dancvan/AlGaAs_electrooptic_effect/documents/internal_notes/stefan/coaximpedanceExpanded.pdf

cable | impedance
Typical | coax | cables | in | labs (

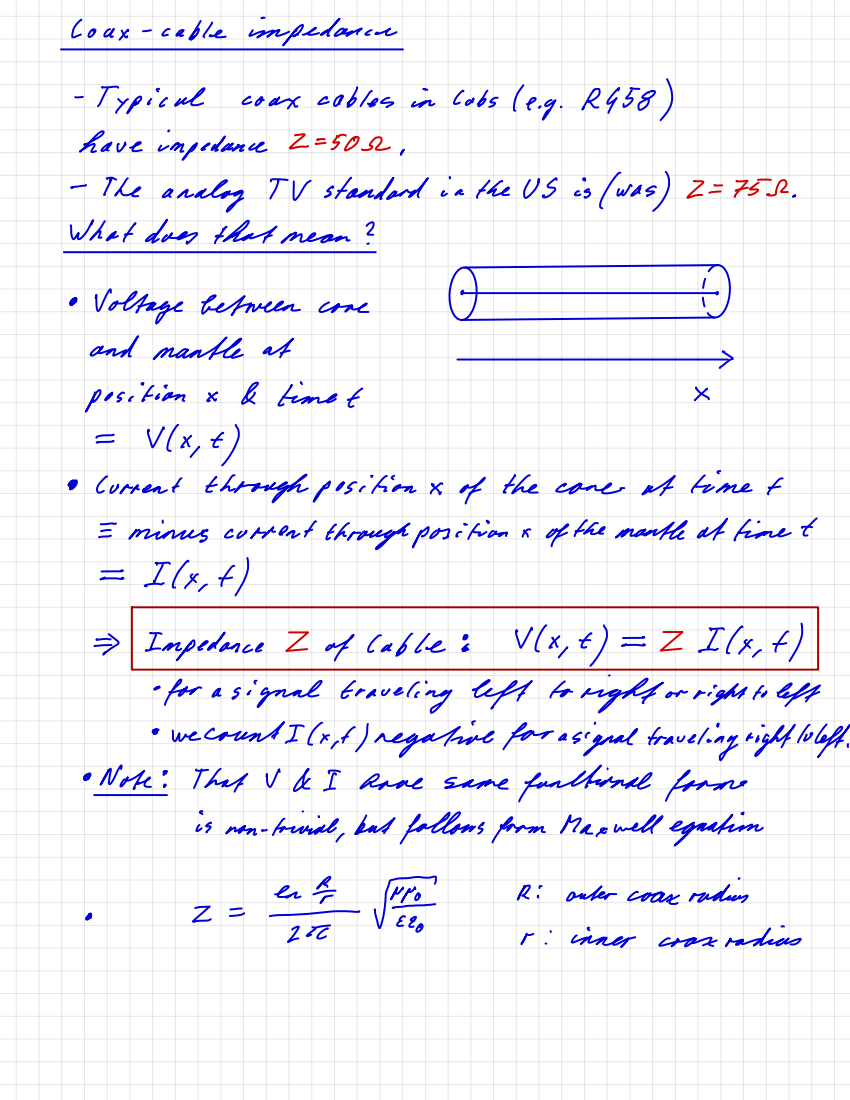
[picture p15: page 1]
Coax; have; impedance; The; analog; standard in; the; is (was); What does; thatmean; Voltage; between; cone; and; mantle; position; time t; Vlx,; Current; through position; cane; time; = minus; current throughposition; of the; mantle attime t; Itx. t; Impedance; cable; for a; signal; traveling; left; to nightor right to; • Note; That; same; functional; forme; non -; trivial,; butfollows from; Maxwell equation; JOE; outer coat radius; inner; coat; radius

• wecountI(xf)negative for a

signal traveling righttoleft.

A) | Cable | termination | & reflector | .

# Haq r

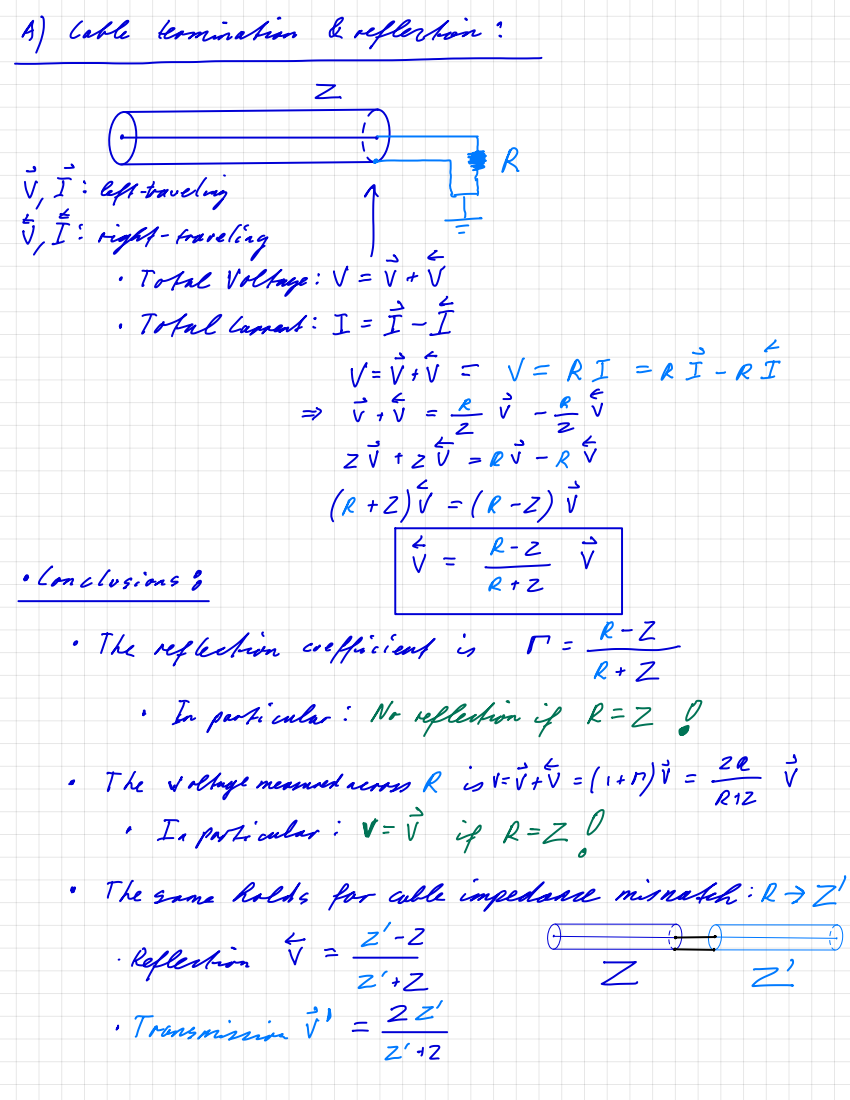
[picture p16: page 2]
I : eye.; traveling; right ⁻; Total; Voltage : V; Total Lamont :; Conclusions 8; reflection; coefficient; particular; reflection if; The; voltage measuredacross R; In particular; same; holds; for; cable; impedance; mismatch : R →; Reflection; Transmission

B) | Driving | a | coat | cable
.Ew# •

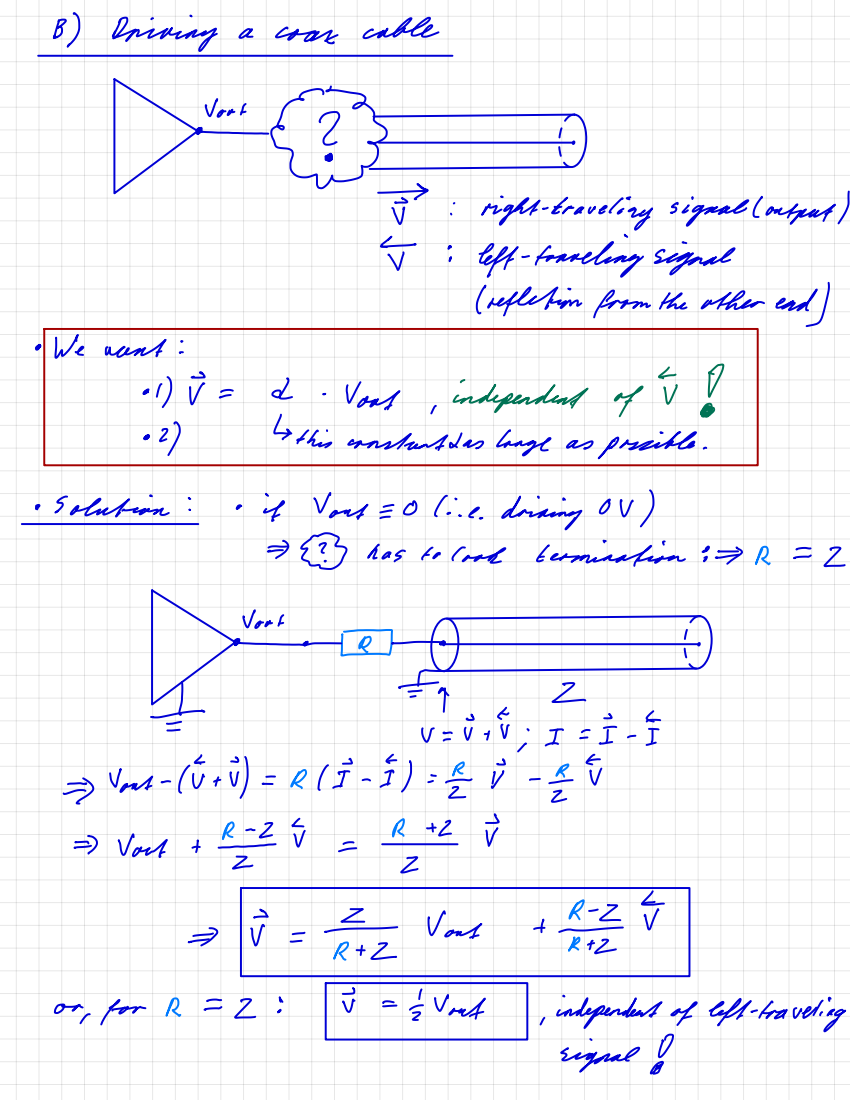
[picture p17: page 3]
right ⁻; traveling; signal⁽output); left ⁻; trawling signal; (reflection; from the; other; end) •; want; Voat; independent; ↳this; camshaftas; Lange; aspossible .; solution; Vont; driving; has to; cook; termination; ✓out; vomit; Van.; REZ; Vous; RLIF; ,for; Vout; independent af; left-; signal I

## On RF Interference and Noise Rejection

Stefan Ballmer, Dec 14, 2020

This write-up summarizes a few simple principles that help when dealing with RF noise.

- RF interference can be thought of as an additional voltage signal picked up along cables. Particularly bad are any induction loops, that is large areas outlined by separated signal and ground wires. Faraday’s law of Induction works against us in this situation.
- We therefore always route two wires (signal/ground, or signal & reference) together. Either in twisted pair cables or more commonly in our lab in coaxial cables.
- Note that we still pick up RF interference on the common signal of the pair (signal+reference), while we want to encode information of the differential signal (signal-reference).
- There are fundamentally two ways to try to reject signal contamination:
- Balanced lines: Example: twisted-pair cable. The idea is to have two conductors with the same impedance, so any RF interference affects both cables exactly equal. For this to work, the receiver has to be differential and balanced (i.e. same impedance on both receiver inputs). The driver also has to have balanced impedance on both lines. Note though that the driver DOES NOT have to be differential for the noise cancellation to work.
Wikipedia article:
https://en.wikipedia.org/wiki/Balanced_line
- Shielded (but unbalanced) cables: Example: coaxial cable. A coax cable has the advantage that the whole signal is contained between the inner conductor (or core) and the outer conductor (or shield). This helps to keep any unwanted signals out but requires as low as possible resistance on the shield. Thus, coax cables are typically not balanced. On long cables this can lead to some conversion of common to differential signal. There are simple strategies to kill this common signal, see e.g. the RF choke in the picture.
Wikipedia article:
https://en.wikipedia.org/wiki/Coaxial_cable
- Twin-axial cables are sometimes used to get shielded and balanced signal transmission.

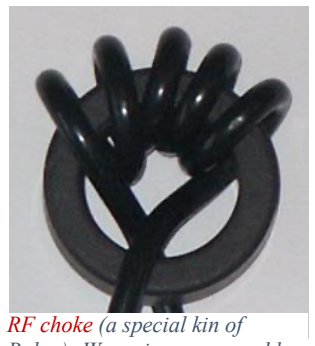
[picture p18: figure]
RF choke (a special kin of

Another link on balanced vs. unbalanced: http://www.bluejeanscable.com/articles/balanced.htm

Balun): Wrapping a coax cable around an iron core increases the inductance for the common mode signal (but not the
differential mode signal), thus killing any common-mode RF interference.

## Strategies for mitigating RF interference:

- Always use coaxial cables (between electronics boxes) or twisted pair (short connections inside an electronics box).
- Shield you RF electronics boxes (metal box, or metal-covered plastic box).
- Keep cables as short as possible, pay attention to routing.
- Use cables with heavy gauge shields.
- Maintain good connections. (You won’t believe how much time I have wasted due to bad connections.)
- Do not add unnecessary grounds. This might be surprising at first glance. But note that any additional ground connection forms an induction loop, putting additional signal on to your transmission line.
- Use ground isolators in problem signal paths.
- Install RFI filters in signal path. An example is the RF choke, or any balun.
- Locate and treat the offending source.

Here is an nice article on mitigating RF interference: https://www.svconline.com/resources/understanding-and-controlling-rf-interference-364849

## What about differential drive?

A common misconception is that a balanced line or a differential
receiver require a differential drive (i.e. a. drive that puts the same signal with opposite sign on each of the two leads). This is wrong. A
differential receiver obviously can receive single-sided signals. And
the figure shows an example of a balanced, single-ended drive.

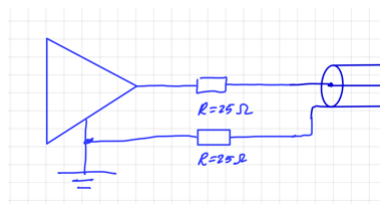
[picture p19: figure]

The only advantage of a differential drive is that the common-mode signal of a line is not driven. This reduces its effectiveness as antenna, thus reducing RF interference for other circuits.

Wikipedia article: https://en.wikipedia.org/wiki/Differential_signaling

## Simple rules to live by

- Make all drives single-sided. This also makes connecting an oscilloscope easy.
- Ground the cable shield at the driver end only.
- For RF signals put a 50 Ohm resistor in series between the driver opamp and the center conductor of the cable.
- The receiver should always be differential. Only exception:
- Receiver in the same box or rack as driver, with a strong common ground.
- An RF receiver should have 50Ohm impedance.
- A low-frequency receiver (below ~100kHz) should have high impedance (>1kOhm, 10kOhm is typical).

An example of a balanced,
single-ended drive.

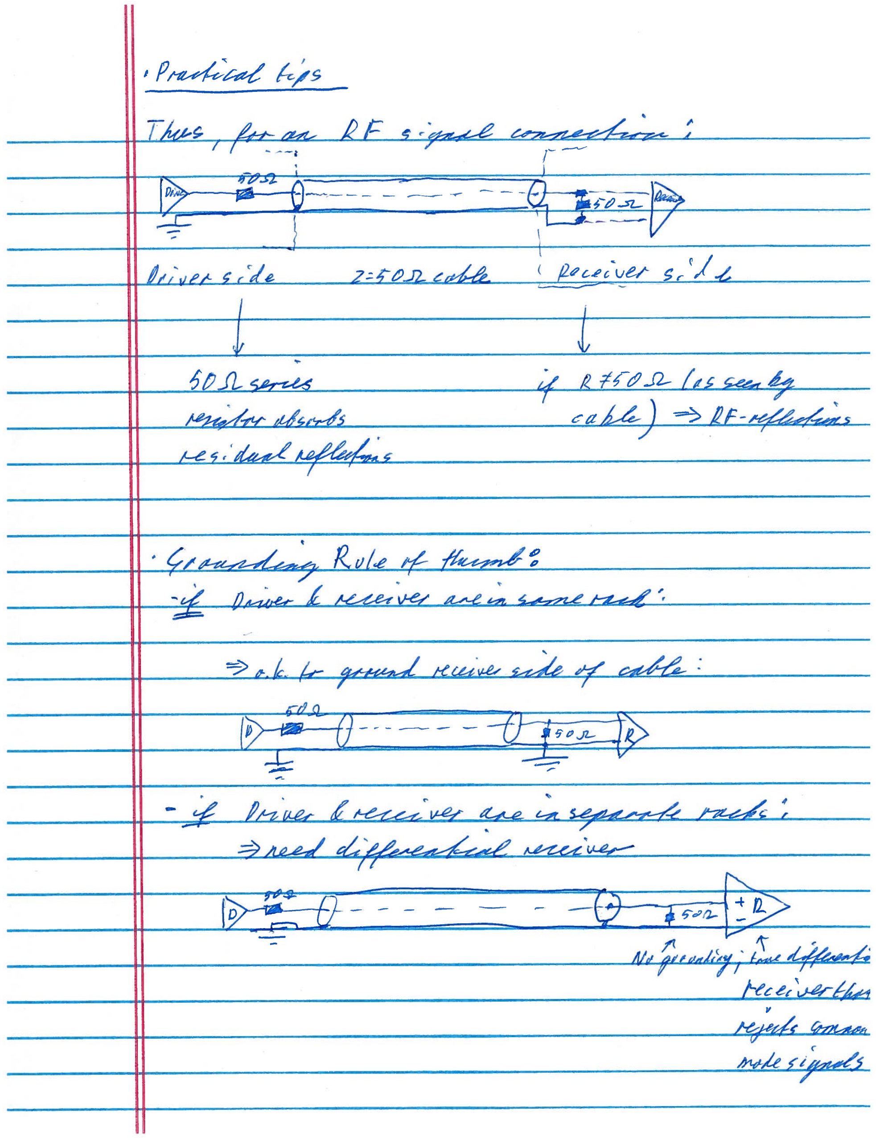
[picture p20: page 6]
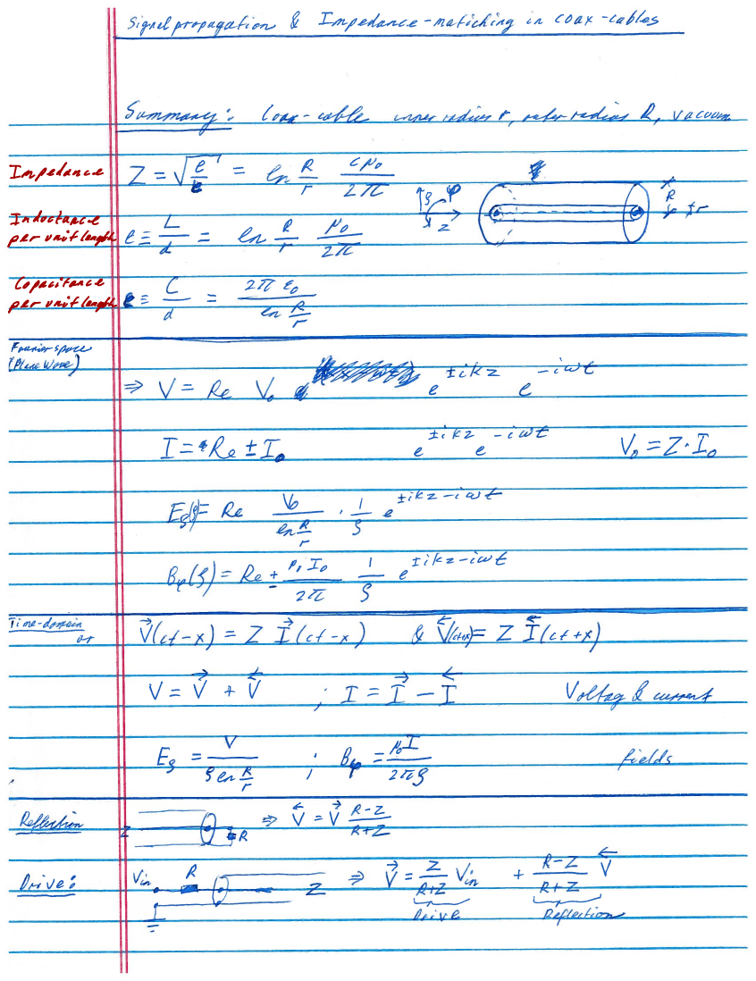
[picture p21: page 7]
Impedance; Inductance per unitlength; capacitance per unitlength
