dancvan/AlGaAs_electrooptic_effect/documents/internal_notes/mode_matching/modematching_notes.pdf

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
## Mode Matching to in-air cavity

MMT = Mode matching telescope
MML = Mode matching lens

## Initial plan

Beam scan after SM2 -> Which is now a 50-50 BS for s-polarization light Calculate the waist size necessary for the cavity
Measure lengths for approximate (waist position) cavity location
Insert parameters into JAMMT
Install MMT
Take another scan somewhere after the telescope to verify the solution Do best to match JAMMT to on-table situation
Install cavity
Calculate, Measure and Install all that is necessary for REFL PD Fine-tune cavity

## 10-23-2019

Set up 2 Lens MMT after SM2
f_MML1 = 57.4 mm
f_MML2 = 171.9 mm
Note: there should probably be a standardized procedure to make sure the center of the lenses will be at the same location within the holders We set up the MMT and steering mirrors but are having issues with the rough waist position
The only way to know how well the mode matching solution agrees with the JAMMT solution is to measure the lengths from all the optics after SM2 and scan the beam from after the last steering mirror

## 10-24-2019

Measure the lengths between installed optics after SM2
SM2 to MML1 : 4 and 20/32 inches (.1174 [m]) MML1 to MML2: 10 and 16/32 inches (.2667 [m]) MML2 to SM3*: 6 inches
SM3* to SM4*: 2 and 15/32 inches
SM4* to SM5*: 19 inches

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
Total distance between SM2 and SM5*: 1.08 meters Beam scan from SM5*
Results:

Report two sets of measurements between the two scans: Between u and v and minor and major respectively: U (x) vs minor:
Waist position difference: 7 mm Waist size difference: 20 um
V (y) vs major:
Waist position difference: .8 mm Waist size difference: 1 um
JAMMT solution was set so that the beam waist is to be approximately 1.330 (1.325-1.335) meters away from SM2
The measured x-waist position: 1.08 [m] + .338 [m] = 1.418 [m] Discrepancy of .008 [m] = 3.46 inches
Write log entry on which part of DataRay Software we should be measuring (consult with WinCamD manual) [DRAFTED]
Summary of what we want to measure:
Standard gaussian beam diameter / radius measurements (Where the intensity drops off 1/(e^2))
DataRay by default sets this for Clip[a]
To set the u-axis as the x-axis and the v-axis to the y-axis, set the cursors to zero degrees
Consult JAMMT solution again
How well reality reflects the model
Double check solution with proper lenses

10_24_2019
folder
162 KB

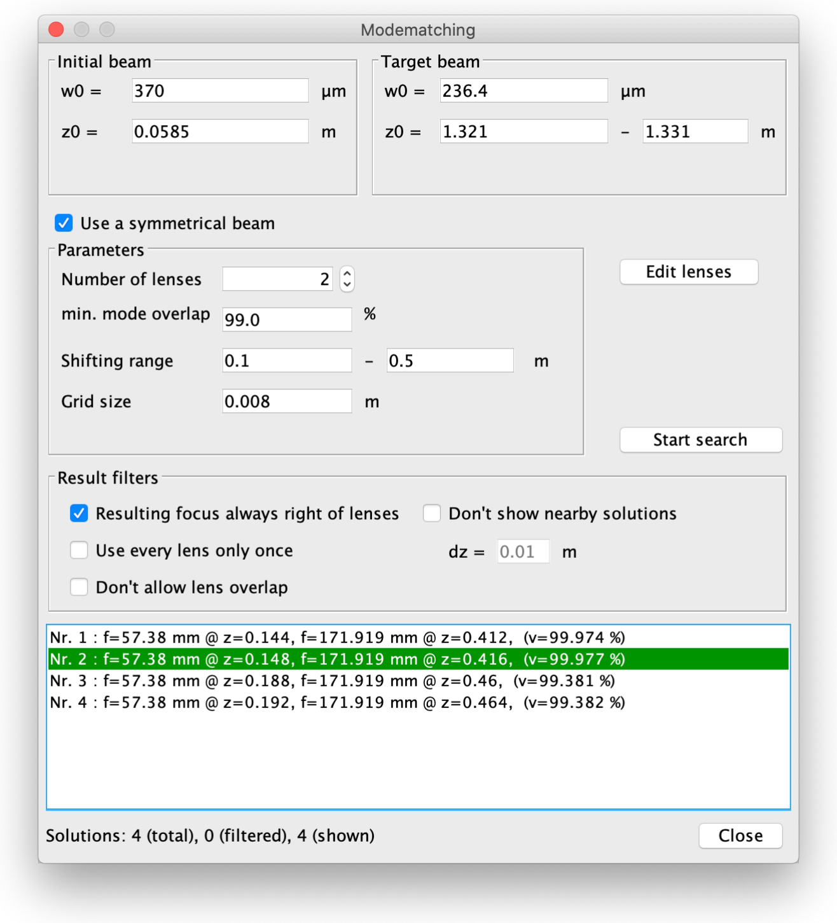
[picture p22: figure]

◆
◆

◆

◆
◆
◆

This assumes a beam size of 231.345 [um] at 1.331 [m]
Can actually perform a bit better with MML1 at 1.488 [m] which will shift your beam to 1.346 [m] away
Also suggests that if I am about a .8 mm off with the placement of MML1 then:
The beam position shifts by about .015 [m]
The beam size shifts by about 236.153 [um]
If we assume that this change is linear, then we can say that the final waist position shift and size shift (respectively) for a change in length between the two MMLs are: .01875 [m]/[mm] (or .74

◆

◆

◆

○

○

○
◆

[in] / [mm]) and 6 [um]/[mm]
Shift lenses to measured positions
With the measured positions we estimate that the waist size is 236.702 [um] and is 1.313 [m] away from SM3*
A secondary scan today revealed that the beam waist should be at 1.418
This amounts to a discrepancy of .105 [m]
Tackle discrepancy between JAMMT solution and solution on the table Currently are not including error bars on our length measurements Re-measure lengths and add error bars
Currently have not created a standardized procedure for centering the lens in the holder.
Re-install lenses that are approximately set (MAY NOT BE NECESSARY IF WAIST SIZE IS GOOD ENOUGH. CALCULATE % MM GIVEN SCAN MEASUREMENT [Power overlap])
Is astigmatism problematic?
Possibly (can include astigmatism in power overlap integral to see how bad mode matching might be)
Calculate mode overlap percentage Symmetric beams
Asymmetric beams

Scanned Documents

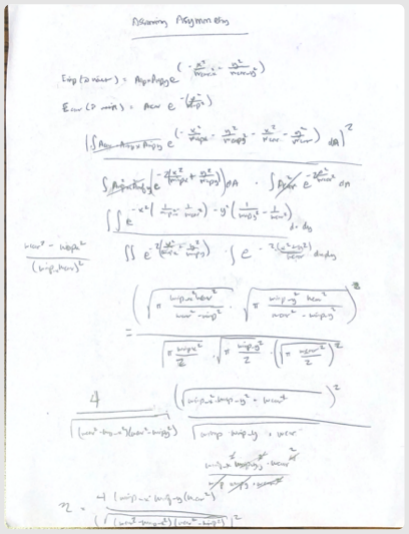
[picture p23: figure]
