dancvan/AlGaAs_electrooptic_effect/documents/internal_notes/PDH/LAB_PMC_T010037-00.pdf

LIGO-T010037-00-W | March 19,2001

## Characterization of the Pre-modecleaner for the Pre-stabilized Laser on the Hanford 4-km Interferometer

M. Rakhmanov and R. Savage

The goal of this effort is to assess the internal losses in the pre-modecleaner (PMC) utilized in the LIGO pre-stabilized laser system (PSL). We use design parameters for the dimensions of the pre-modecleaner cavity and laboratory measurements (cavity bandwidth, input power, transmitted powers, and reflected power) to estimate the mirror transmissions and losses due to absorption and scattering. We are unable to determine the losses for each mirror, so only the total cavity loss and average loss per mirror are given. We assume that the transmissions of the two flat mirrors are equal.

## FSR and Finesse

The PMC is a high-aspect-ratio, triangular Fabry-Perot cavity. If the base of the triangular optical path is denoted by d and the height by h, the optical path length, L, is given by,

L = d + p
d2 +4h2. | (1)

The free spectral range (FSR) of the cavity is given by

ffsr = c
L | (2)

where c is the speed of light. The finesse, F, is defined as the ratio of the free spectral range to the width (FWHM) of the cavity resonance peak,

F = ffsr
∆f , | (3)

where ∆f is the width of the resonance (power, measured in transmission or reflection). The design parameters and calculated values are given in Table 1, below.

1

Table 1: PMC Parameters

parameter | symbol num. value
height (cm) | h | 20
base (cm) | d | 2
path length (cm) | L | 42.1
free spectral range (MHz) | ffsr | 713.0

## Mirror Reflectivities

With the amplitude reflectivity and transmissivity of the cavity mirrors given by ri and ti for i =1, 2, 3, the corresponding power reflectivity and transmissivity are given by

Ri | = r2
i , | (4)
Ti | = t

2
i . | (5)

These are not entirely independent quantities. They are related by energy conservation;
Ri + Ti + Li =1, | (6)

where Li are the mirror power losses due to scattering and absorption. In what follows we assume that Ti and Li are independent variables, and determine Ri from energy conservation.
A useful quantity for these calculations is the round-trip field reflectivity, r, given by
r = r1r2r3. | (7)

The quantity which is directly related to the mirror reflectivities is the coefficient of finesse, F, given by

F = | 4r
(1 − r)² . | (8)

The coefficient of finesse, F, and the finesse, F, are related by
F = π

√
F
2 . | (9)

2

## Power Budget

The power of the laser beam incident on PMC is denoted by Plas. The incident laser power that is in the fundamental mode (TEM00in this case) of the PMC, the mode-matched power, is given by is

Pmm = MPlas, | (10)

where M is the mode-matching factor.
The laser power circulating in the cavity is given by
P = GPmm = GMPlas, | (11)

where G is the cavity amplification factor or power gain given by

G = | T1
(1 − r)² . | (12)

The subscript 1 denotes the input mirror of the cavity. Strictly speaking, the power in the cavity is different after reflection from the different cavity mirrors. P given above corresponds to the laser field immediately after the cavity input mirror. The powers inside the cavity immediately after the second and third mirrors are given by R2P and R3R2P, respectively. Thus the power transmitted (leaked) through the back mirror (the curved mirror at the vertex of the triangle between the two flat mirrors, mirror 3) is
Pleak = T3R2P. | (13)

The power transmitted through the cavity on resonance is given by

Ptr = T2P. | (14)

Therefore the cavity throughput, the ratio of transmitted to incident power, is given by

Tcav ≡

Ptr

Plas

= T1T2M
(1 − r)² . | (15)

## Visibility and Mode-matching

The power reflected by the cavity is maximum when the cavity is antiresonant (out of lock). In this case, for a reasonably high finesse cavity, it reflects almost all of the incident power,

Pmax ≈ Plas. | (16)

3

The minimum power reflected by the cavity (when it is in lock) is Pmin. When the power in the sidebands used to lock the cavity is negligible (as it is for the PMC in the PSL), then

Pmin ≈ Pref | (17)

where Pref is the power reflected by the cavity when it is locked. Plas, Pref, Ptr,and Pleak are measured in the laboratory.
To calculate the cavity reflectivity when on resonance , we separate the mode-matched and non-mode-matched powers. The mode-matched and non-mode-matched powers are given by MPlas, and (1 − M)Plas, respectively. The total power reflected by the cavity can be written as
Pref = RcavMPlas + R1(1 − M)Plas. | (18)

where Rcav ≡|ρ|

2 is the reflectivity of the cavity for perfectly mode-matched power. ρ is given by
ρ = r1 − t

2
1r2r3

1 − r1r2r3

. | (19)

The cavity visibility is defined as

V ≡

Pmax − Pmin

Pmax

. | (20)

It is related to the mode-matching factor as

V = M

µ

1 − Rcav

R1

¶
. | (21)

## Measurements

Plas, Ptr, andPrefwere measured using a Scientech calorimeter and Pleak was measured using an Ophir power meter. The cavity bandwidth was measured by sweeping the laser frequency using the FAST actuator and monitoring either the transmitted or reflected power. The parameters measured in March, 2001 are given in Table 2.

## Calculation of Mirror Transmissions and Losses

Using the measured power levels and cavity bandwidth, an iterative calculation is used to estimate the mirror transmissions and losses. First a a guess

4

Table 2: Measured Parameters

parameter | symbol num. value
input laser power (W) | Plas | 9.3
transmitted power (W) | Ptr | 6.13
reflected power (W) | Pref | 1.35
leakage power (W) | Pleak | 0.11
cavity bandwidth (MHz) | ∆f | 4.33

of the mode-matching factor (the visibility, V , is a good first guess) is used to calculate the mirror transmissions and losses. Then these parameters are used to obtain a better estimate of the mode-matching factor which is then used to improve the estimate of the transmissions and losses, and so on. First we calculate r using the measured cavity bandwidth and Eqs. (8) and (9). To start the iterative calculation, we provide an initial guess for the mode-matching factor, M. The T1T2 product is determined from the incident and transmitted power measurements using

Tcav ≡

Ptr

Plas

= MGT2 = T1T2M
(1 − r)² . | (22)

and is given by
T1T2 = Tcav
M (1 − r)
2. (23)

Assuming that the mirrors have equal transmissions we obtain

T1 = T2 =

s
Tcav
M (1 − r). | (24)

The transmission of the third mirror can be found from the leakage power by
T3 = Tleak
T1M (1 − r)
2. (25)

The average mirror losses are estimated as follows. Consider the product,

R | ≡ R1R2R3 | (26)
| = (1 −L1 − T1)(1 −L2 − T2)(1 −L3 − T3) | (27)
=1 − X
| i

# Li − X

i

Ti + X

i<j

TiTj | (28)

+X
| i<j LiL+

X

i≤j

LiT+higher order terms | (29)

5

Neglecting terms with LiTj , LiLj , and higher order terms, we have
R ≈ 1 − X

i

# Li − X

i

Ti + X

i<j

TiTj . | (30)

The combined losses are then given by
X

i

# Li =1 − R − X

i

Ti + X

i<j

TiTj . | (31)

Assuming that the losses per mirror are equal, i.e. L1 = L2 = L3, we obtain an estimate of the average loss per mirror,

L = 1
3

X

i

Li. | (32)

Using this result, we obtain a correction for the combined losses by considering the fifth and sixth terms in the last line of Eq. 26,

corr = 3L² +2L(T1 + T2 + T3), | (33)

Thus, a better estimate of the average loss per mirror is
L⇒L +

1
3
corr. | (34)

Using the estimates of mirror transmissions and losses, we now calculate a better estimate of the mode-matching factor using the measured visibility by
M = | V

1 − Rcav/R1

(35)

This value is then used to improve the estimates of the mirror transmissions and losses. This procedure is iterated until the estimates converge.
The results of the calculations are shown in Table 3.

6

Table 3: Calculated Parameters

parameter | symbol | num. value
cavity visibility | V | 0.85
mode-matching coefficient | M | 0.87
transmission of mirror # 1 and # 2 | T1 | 1.65 × 10−2
transmission of mirror # 3 | T3 | 2.95 × 10−4
average losses per mirror | L | 1.54 × 10−3

7
