dancvan/AlGaAs_electrooptic_effect/documents/internal_notes/reflected_phase-Edgard.pdf

# On the Phase Change in the reflected wave of a dielectric mirror (Checking Marty Fejer’s math)

Edgard Bonilla (Drawing heavy inspiration from Marty Fejer)

October 11, 2018

## 1 Introduction

The objective of this writeup is to check the calculations for the derivative of the phase of the reflected electromagnetic wave coming out of a quarter-wave stack of dielectric materials.
We assume that there is a scalar quantity γ that has an effect on the properties of the dielectric materials in question. We want to calculate the derivative:

dφ
dγ |γ=γ0

(1)

where φ is the phase of the reflected wave relative to the incident one. γ0 is the nominal value of the parameter γ, under which the system should look like a quarter-wave stack.
We also assume for most of the derivation that the electric field of the electromagnetic wave is parallel to the surface of the material. However, since we are interested in the normal incidence case this will have no effect on the results.

### 1.1 Notation

- The term ’nominal values’ is intended to represent the ideal conditions for the dielectric material stack. There, they look like a quarter wave stack and γ = γ0.
- x

0
represents the derivative of x with respect to γ.
- xˆ represents the quantity x evaluated at the nominal value γ0. This su-perscript will be ommited in quantities that are defined only at this value of γ
- xˆ0 represents the derivative of x with respect to γ, evaluated at the nominal values for the stack.

### 1.2 Definitions

We will start by assuming a result for the reflectivity of a multilayer dielectric (this is discussed, in Born and Wolf section 1.6, in a very detailed way).

1

The reflectivity for N alternating pairs of layers of thickness h2 and h3 and refractive indices n2 and n3, lying between a semi infinite input medium of index n1 and an output medium with index nf for a harmonic wave of vacuum wavelength λ0 is given by an expression of the form:

r =

A + iB
C + iD

(2)

Where the quantities A, B, C, D are real and related to the transfer matrix of the stratified medium M by:

A = p1M11 − pfM22 | (3)
B = p1pfM12 − M21 | (4)
C = p1M11 + pfM22 | (5)
D = p1pfM12 + M21 | (6)
(7)

The matrix elements here are defined so that all of them are real. They are given by:

M11 =

cos β2 cos β3 −

p3
p2

sin β2 sin β3

UN−1(a) − UN−2(a) | (8)

M12 = −

1
p3

cos β2 sin β3 +

1
p2

sin β2 cos β3

UN−1(a) | (9)
M21 = − [p2 sin β2 cos β3 + p3 cos β2 sin β3]UN−1(a) | (10)

M22 =

cos β2 cos β3 −

p2
p3

sin β2 sin β3

UN−1(a) − UN−2(a) | (11)
| (12)

where
a = cos β2 cos β3 −

1
2
p2
p3

+

p3
p2
sin β2 sin β3 | (13)

and the UN (a) are the Type II Chebyshev polynomials. Defined in the complex plane by:
UN (a) = sin ((N + 1) arccos(a))
sin(arccos(a)) | (14)

finally, for a non magnetic medium, pj = nj cos θj and βj =

2π
λ0

njhj cos θj .
Where θj is the incidence angle for the wave, measured from the normal to the surface and nj is the refractive index of the material.

### 1.3 Values for a quarter wave stack and normal incidence:

With the condition of normal incidence ˆpj = nj . Adding the condition for a quarter wave stack: βˆ
j =

π
2

2

### 1.3.1 Chebyshev polynomials:

In the nominal conditions for the stack, it is possible to give a very simple closed form expression for the Chebyshev polynomials involved in the calculation. For the sake of brevity, let z = (n2/n3). We can then write â as:

â = −

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
(15)

In order to evaluate equation 14, we can formally compute arccos(â) in the complex numbers as:

arccos(â) = −ilog
â +

p
â

2 − 1

(16)

From the definition of â, it can be calculated that â

2 − 1 =

1/2
z −

1
z

2
We need to choose a branch for the square root in equation 16. It does not matter which one we choose, since UN is going to be real valued. We select:

p
â

2 − 1 = −

1
2
z −

1
z
(17)

And so:

arccos(â) = −ilog
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
= −ilog (−z) (18)

We are finally ready to evaluate the Chebyshev polynomials. Using eqns 14 and 18:

UN (â) = sin (−(N + 1)ilog (−z))
sin(−ilog (−z)) =

e

(N+1) log(−z) − e

−(N+1) log(−z)
e

log(−z) − e⁻ log(−z)

UN (â) = (−z)

N+1 −

−

1
z

N+1 −z +
1 z | = (−1)N
1
zN+1 − z

N+1
z
1 − z

2

(19)

### 1.3.2 Matrix elements

We proceed to evaluate the values for the matrix elements for normal incidence in a quarter wave stack.
The off-diagonal elements are zero because βˆ

2 = βˆ
3 =

π
2

. Mˆ

12 = Mˆ
21 = 0.
The diagonal elements satisfy:

Mˆ
11 = −

1
z

UN−1(â)−UN−2(â) = (−1)N z 1 − z

2

1
zN+1 − z

N−1 −

1

zN−1

+ z

N−1

Mˆ

11 = (−1)N z
1 − z

2

1
zN+1 (1 − z

2

) = (−1)N 1
zN

(20)

Mˆ

22 = −zUN−1(â)−UN−2(â) = (−1)N z 1 − z

2

1

zN−1

− z

N+1 −

1

zN−1

+ z

N−1

Mˆ

22 = (−1)N z
1 − z

2

z

N−1
(1 − z

2

) = (−1)N z

N | (21)

3

### 1.3.3 The reflectivity coefficients A, B, C, D

Using the previous result for the off diagonal elements of Mˆ , we determine that Bˆ = Dˆ = 0 for a quarter wave stack and normal incidence. While Â and Dˆ satisfy:
Â = (−1)N
n1

1
zN

− nf z

N

(22)

Cˆ = (−1)N

n1

1
zN

+ nf z

N

(23)

## 2 Derivation

To derive the quantities of interest, we first find the phase of r from equation 2. Noting that the quantities A, B, C, D in the equation are real, it follows from the properties of complex numbers that the phase φ is just the difference of the phases of the numerator and denominator:

φ = arctan
B
A

− arctan
D
C
(24)

From which it follows that:

dφ
dγ =

dB
dγ A −

dA
dγ B
A² + B²

−

dD
dγ C −

dC
dγ D
C² + D²

(25)

Eevaluating this expression at the nominal values (section 1.3.3) yields:

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
Bˆ0Cˆ − Dˆ0Â
AĈˆ

(26)

### 2.1 The derivatives B⁰

, D⁰

We compute B⁰

, D⁰
should be analogous to it.

B

0 = (p1pf )

0M12 + (p1pf )M⁰

12 − M⁰
21
since at the nominal conditions M12 = M21 = 0, and we assume | ˆ (p1pf )
| 0 is
finite, then we only need the derivatives for the off-diagonal matrix elements. We evaluate B⁰ at the nominal values to obtain:

Bˆ0 = (n1nf )Mˆ ⁰

12 − Mˆ ⁰
21 | (27)

Similarly, for D⁰ we would have:

Dˆ0 = (n1nf )Mˆ ⁰

12 + Mˆ ⁰
21 | (28)

Once more we compute Mˆ 0

12 explicitly and Mˆ 0
21 is analogous.
By inspecting equation 9 we observe that the only surviving terms after taking a derivative and evaluating at the nominal conditions are the ones where we remove the simple zero of the cosines at β2 = β3 =

π
2

. In consequence:

Mˆ ⁰
12 = −
1
pˆ3

ˆ (cos β2)

0
sin βˆ
3 +

1
pˆ2

sin βˆ
2

ˆ (cos β3)

0

UN−1(â)

4

Using the chain rule and evaluating at the corresponding conditions:

Mˆ ⁰
12 =
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
UN−1(â) | (29)

similarly:
Mˆ ⁰
21 =

h
n2βˆ⁰
3 + n3βˆ⁰
2

i
UN−1(â) | (30)

### 2.2 Putting it all together:

We will put together equation 26 by parts:
First, the denominator. Using the values for A and C from equations 1.3.3 and 23:
AĈˆ =
(n1)

2

1
z

2N

− (nf )

2
z

2N

(31)

Second, the numerator. Using equations 2.1 and 2.1 together with the equations for A and C.

Bˆ0Cˆ = (−1)N

(n1nf )Mˆ0

12 − Mˆ0

21
n1

1
zN

+ nf z

N

Dˆ0Â = (−1)N

(n1nf )Mˆ0

12 + Mˆ0

21
n1

1
zN

− nf z

N

Identifying similar terms with different signs in the previous two equations we arrive at:

Bˆ0Cˆ − Dˆ0Â = 2(−1)N

n1(nf )

2
z

NMˆ0
12 − n1

1
zN Mˆ0

21
(32)

Using the identity for the Chebyshev polynomials (19), we parse the z dependent terms of the equation to expand the solution:

z

NM⁰
12 =
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
(−1)N−1
(1 − z

2N )

z
1 − z

2
1
zN M⁰
21 =

h
n2

ˆβ
0
3 + n3

ˆβ

0/2 i
(−1)N−1
1
z

2N

− 1

z
1 − z

2

Plugging these into equation 32, we find:

Bˆ0Cˆ − Dˆ0Â =

−2n1z
1 − z

2

(1 − z

2N )

(nf )

2
n2n3

(n2

ˆβ
0
2 + n3

ˆβ
0/3) −

1
z

2N

(n2

ˆβ
0
3 + n3

ˆβ
0/2)

(33)
Combining equations 31 and 33, multiplying by z

2N to simplify the fractions:

φˆ0 =

2n1z
1 − z

2

(z

2N − 1)

z

2N (nf )

2
n2n3

(n2

ˆβ
0
2 + n3

ˆβ
0/3) − (n2

ˆβ
0
3 + n3

ˆβ
0/2)
(n1)

2 − (nf )

2z

4N

(34)

with z =

n2
n3

and βj =

2π
λ0

njhj cos θj

5

### 2.3 Large N limit approximations

### 2.3.1 Case n2 < n3:

with the overall assumption that (nf )

2
z

4N
(n1)

2 < 1 we can expand the denominator with a geometric series, which gives:

φˆ0 =

2z(z

2N − 1)
(1 − z

2)n1

z

2N (nf )

2
n2n3

(n2

ˆβ
0
2 + n3

ˆβ
0/3) − (n2

ˆβ
0
3 + n3

ˆβ
0/2)

X∞

j=0

nf
n1

z

2N

2j

(35)
The leading order term for this expansion is:

ˆφ
0
0 =

2n2n3
((n3)

2 − (n2)

2) n1

(n2

ˆβ
0
3 + n3

ˆβ
0/2) | (36)

With the first correction being of order z

2N and given by:

ˆφ
0
1 =

−2n2n3
((n3)

2 − (n2)

2) n1
(nf )

2
n2n3

(n2

ˆβ
0
2 + n3

ˆβ
0/3) + (n2

ˆβ
0
3 + n3

ˆβ
0/2)

n2
n3
| 2N
| (37)

### 2.3.2 Case n2 > n3:

TBD.

## 3 Application to different effects (assumes n2 <

n3)

By setting the parameter γ to different physical properties that change uniformly on the stack, we can use equation 36 to compute the leading order term of the phase change caused by this parameter variation.
we only need to compute:

dβj
dγ |γ=γ0 =

2π
λ0

d
dγ (njhj cos(θj ))|γ=γ0 = βj

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
+ tan( ˆθj )

ˆθ
0
j

!
| (38)

In general, we expect the the derivative of the incidence angle θ

0
j
| to be finite,
which drops the last term (ˆθj = 0). If we define:

κγj =

d
dγ log(njhj )|γ=γ0 =

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
(39)

Then for a quarter wave stack and normal incidence:

β

0
j =

π
2
κγj | (40)

κγ∆γ is meant to be understood as the fractional change in the phase difference β as we vary the scalar γ uniformly in the dielectric medium.

6

With these definitions, the leading order term for φ

0
reads:

ˆφ
0
0 =

π
(1 − (n2/n3)
2) n1

(n3κγ2 + n2κγ3)

n2
n3
(41)

The first correction being:

ˆφ
0
1 =

−π
(1 − (n2/n3)
2) n1
(nf )

2 + (n3)

2
n3

κ2γ +

(nf )

2 + (n2)

2
n2

κ3γ

n2
n3

2N+1

(42)

### 3.1 Notes on κ:

- The quantity h

0
h

is the fractional change on the thickness of the dielectric layer. If γ represents temperature, this is the thermal expansion coefficient at temperature T0.

### 3.2 Notes on general assumptions:

This is a short list of the assumptions that I believe this derivation hinges on:

- The material is nonmagnetic. this would change the definition of p, but probably can be relaxed.
- There is no loss of energy from the electromagnetic field to the material. This is no longer true if the conductivity of the material cannot be neglected.
- None of the quantities involved in the definition for r change abruptly with respect to the parameter γ
- The boundary conditions for Maxwell’s equations remain the same even when we change γ (no free charges accumulate, etc.). this is to ensure that the solution for r(γ + δγ) has the same functional form.
- Similar to the point above, the quantity γ changes uniformly on the whole stack, there are no spatial gradients for it or they are negligible.
- The material properties (hj and nj ) do not change significantly with the electromagnetic wave going inside them.

7
