dancvan/AlGaAs_electrooptic_effect/documents/internal_notes/marty/Birefringence in Crystalline Coatings_v8.pdf

Birefringence in Crystalline Mirror Coatings v.8
M. M. Fejer
November 25, 2020
1. Introduction
While the dielectric tensor is isotropic in cubic materials like AlGaAs, the fourth-rank photoelastic tensor is not, which influences the form that the birefringence induced by thermal stresses will take. It is the purpose of this note to illustrate some aspects of thermoelastic birefringence in AlGaAs coatings.
1.1. Summary of the results
For a total absorbed power Pabs distributed as a Gaussian of 1/e2 radius w in a thin multilayer mirror of cubic symmetry on a thick substrate, simplified for the case where the square of the
photoelastic asymmetry parameter 44 | 11 | 12 Ap | pp ≡ | − 2 /( | ) is large (A2 = 33 in GaAs), the difference
between the reflection phase for light polarized along the two principal birefringent axes is given by [Eq. (6.12)]
0 ( | / ) | (1 | ) ( ) | ( ) sin 2 s B R rw B | fR f R m | m | s | s | m
α | ν | θ
α
- | ≡ | = | + | + | | | (1.1)
where
44 | 2 | 2
0 | 2

/
2 | 1( / )
abs | L | H
m | H L | LH
s | L | H
p | nn P B | n n nn
k w | nn
π α | | ≡− | | | + | | − | (1.2)
and the pIJ are photoelastic tensor components, nH and nL are the refractive index of the high and low index layers, respectively, α and αs are the thermal expansion coefficients of the mirror (assumed the same in the high and low index layers) and the substrate, respectively, ks is the thermal conductivity of the substrate, ν s is the substrate Poisson ratio, and θ is the angle with respect to the crystalline x axis of the coating, assumed to be oriented with the z axis normal to the mirror surface. The functions fm(R) and fs(R) defined in Eqs. (5.13), are plotted below

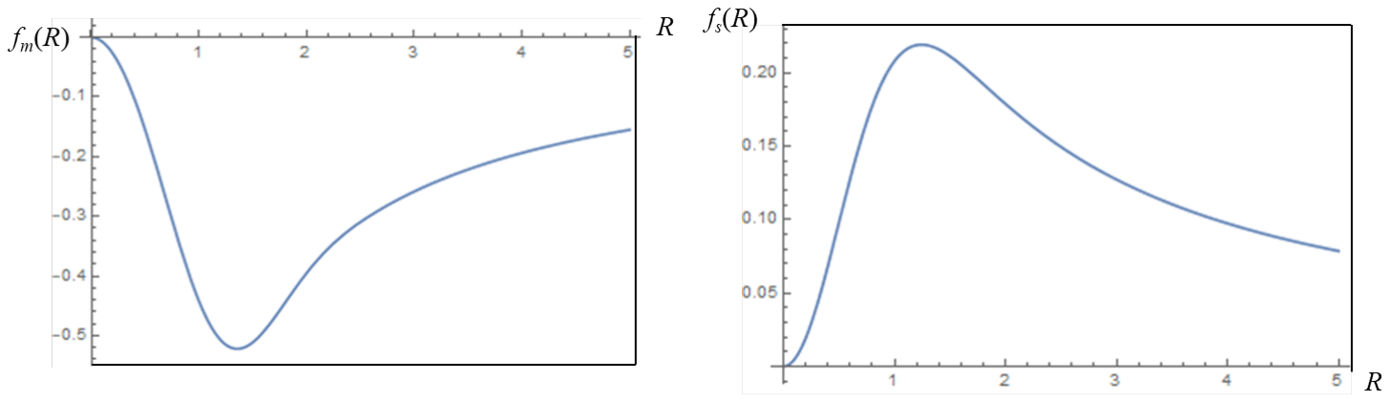
[picture p24: figure]

For an AlGaAs mirror (x = 0.9 and x = 0.1 assumed) on a silica substrate, the prefactor B0m is given by Eq. (6.14)

3
0

[W] 8.9 10
[cm]

abs
m

P B
w
− = | × | (1.3)
We see that for 5 W absorbed from a 5 cm radius beam, the maximum birefringent phase will be 4.5 mrad. Using the same scaling, if there were an absorber of 0.5 mm in size, it would create a birefringence of ~450 mrad per watt of absorbed power. Because of the weak (only 1/r) rolloff of the birefringence away from the absorber, a larger area than that of the absorber itself would be affected.
If irregularly distributed birefringence is introduced into the mirror during growth or bonding, there is no a priori way to predict the expected birefringent phase on reflection unless the irregular strains are known. Conversely, if measurements of the local birefringent phase and principal axes are available, the principal components and axes of the strain can be computed with the results of section 6.5.2, which may be of use in diagnosing the origin of the strains. The connection of the strain to birefringence in reflection for a general orientation of the principal birefringent axes is given in Eq. (6.16). For principal birefringence axes along the [011] direction for the same AlGaAs mirror considered in Eq. (1.3) the principal strain axes are in that same direction, and the result for their magnitude reduces to

6

1 | 2 | 9.3 10 | [mrad] m p SS | B ⁻ − | = | × | (1.4)
The corresponding difference in principal stresses is [Eq. (6.17)]
1 | 2 | 1.1MPa [mrad] m p TT | B − | = | (1.5)
1.2. Outline of the calculation
Section 2 outlines the formal description of photoelasticity, and computes the refractive index change and the birefringence induced in a thin layer, given specified elastic strains in that layer. Section 3 outlines the changes necessary to include thermoelasticity in the calculation, and relates the strains in an object of cylindrical symmetry to the Cartesian tensor components required for photoelastic computations. Section 4 considers the case of a thin layer of cubic symmetry on thick substrate. Section 5 applies the method to two cases, in 5.1 a layer on a substrate with uniform temperature change, and in 5.2 a Gaussian radial distribution of heat deposited on its surface, and shows some simplifications in highly photoelastically anisotropic materials like GaAs. The evaluation of built-in strains from measurements of the static birefringence are also given in Section 5.3. Section 6 relates the birefringence of the reflection phase of a mirror to the birefringence changes in each layer of the mirror, and computes the results for an AlGaAs mirror. Section 7 addresses possible extensions of the present calculation and related future work. Section 8 is an Appendix listing pertinent material properties.
2. Photoelasticity in cubic materials

2.1. Photoelastic tensor
Photoelasticity is generally formulated in terms of the impermeability tensor −1 b ≡ ε . For a strain field SJ in Voight notation, the perturbation to the impermeabiltiy tensor is given by the photoelastic tensor p
∆= b pS I | IJ J | (2.1)
Since p relates two second rank tensors, it is a fourth rank tensor, and has the same symmetry as the stiffness tensor c. For a cubic material, we have
11 | 12 | 12
12 | 11 | 12
12 | 12 | 11

44

44

44

0 | 0 | 0
0 | 0 | 0
0 | 0 | 0
0 | 0 | 0 | 0 | 0
0 | 0 | 0 | 0 | 0
0 | 0 | 0 | 0 | 0

ppp
p | pp
pp | p
p
p
p

=

p | | | | | (2.2)
In an isotropic material there is the additional constraint that 44 | 11 | 12 p | pp = | − ( | )/2 . The anisotropy of
the photoelastic response is often characterized by the anisotropy factor

44

11 12

2 p A

pp ≡ | − | (2.3)
which equals unity in isotropic materials, and with the data in Appendix 1 takes the value 5.76 in
GaAs.
2.2. Refractive index perturbation
2.2.1. Perturbed impermeability tensor
For propagation along the z axis, the x and y components of the dielectric (and hence impermeability) tensor are pertinent. In the principal axis frame of this subtensor b⊥ , the refractive index for light polarized along a principal axis direction is the square root of the reciprocal of the corresponding diagonal tensor component.
From Eqs. (2.1) and (2.2) we have for b⊥ , now in conventional tensor form
1 | 6
6 | 2

bb
bb ⊥
- | = | |
b | (2.4)
where

2
1 | 11 1 | 12 | 2 | 3
2
2 | 11 2 | 12 | 1 | 3
2
6 | 44 6 | ( | | )
( | )
b n | pS p S S
b n | pS p S S
b n | pS

−

−

−

= | + | + | +
= | + | + | +
= | +

(2.5)

2.2.2.Diagonalization, birefringence, principal axes
Call the two principal components of the symmetric two by two matrix in Eq. (2.5) bb, + − . Diagonalizing Eq. (2.4) we have
2 | 2
1 | 2 | 1 | 2 | 6 b | bb | bb | b ( | ) 4 | /2 ± = | +± | − | + | | | (2.6)
With Eqs. (2.5) and (2.6), we have
{[ | ] | }

1

3
2 | 2 | 22
11 | 12 | 1 | 2 | 12 3 | 11 | 12 | 1 | 2 | 44 6 ( | )( | ) 2 | ( | ) ( | ) 4 2

b
n n | n | p p S S | pS | p p | S S | pS

ε

ε

−
± | ±
± | ±

=

⇒ = | ≈− | + | + | + | ± | − | − | +

(2.7)
and the angle θ0 between an eigenvector (and thus a principal birefringent axis) and the x axis
obeys
6 | 44 6 | 6
0
1 | 2 | 11 | 12 | 1 | 2 | 1 | 2

6

1 | 2
2 | 2 tan 2
( | )( | )

isotropic

b | pS | S A
bb | p p S S | S S
| S SS
θ = | = | = − | − | − | −

→ −

(2.8)
where the isotropic limits take advantage of the isotropy condition 44 | 11 | 12 p | pp = | − ( | )/2 .
The birefringence is then
3 | 2 | 2 | 22
11 | 12 | 1 | 2 | 44 6
3 | 2 | 22
11 | 12 | 1 | 2 | 6
3 | 2 | 2
11 | 12 | 1 | 2 | 6
( | )( | ) 4
( | )( | )
( | )( | ) isotropic
B n n | n p p | S S | pS
n p p | S S | AS
np p | S S | S
= − =− | − | − | + + | −
=− | − | − | +
→− | − | − | +

(2.9)

2.2.3.Comparison of cubic vs isotropic media
It is useful to compare the photoelastic behavior of cubic vs isotropic media. Consider a purely compressional strain along different directions in the medium. Take the displacement to be
0 | 0 cos , | sin x | y u Ss | u Ss = | θ | θ = | (2.10)
where 2 | 2 s | xy ≡ | + , which could be considered a compression along a direction θ to the x axis. The
corresponding strains are then
(2.11)

2
1 | 0 | 0

2
2 | 0
6 | 0
cos | cos
sin
2 cos sin
x | x
x | y
u | u s | x S | S | S
x | sx | s
SS
u | u
S | S
y | x
θ | θ
| θ

θθ

∂ | ∂ ∂ = | = | = | = ∂ | ∂∂

=
∂ | | | | | ∂
= | + | =
∂ | | | | | ∂

(2.12)
Noting that with Eqs. (2.12) 1 | 2 | 0 SS S −= cos 2θ and 6 | 0 SS = sin 2θ , we have for the birefringence from
Eq. (2.9)
3 | 2 | 2 | 2 | 2
0 | 11 | 12 | 44
3 | 2 | 2 | 2
0 | 11 | 12
3
0 | 11 | 12
( | ) cos 2 4 sin 2
( | ) cos 2 | sin 2
( | ) isotropic
B | Sn p p | p
Sn p p | A
| Sn p p
θ | θ
θ | θ
=− | − | +
=− | − | +
→− | −

(2.13)
and with Eq. (2.8)the angle of a principal axis is

44
0
11 12

0

2 sin 2 tan 2 | tan 2
( | )cos 2

tan 2 isotropic

p | A
pp
θ θ | θ
θ
θ | θθ
= | ≡ −
→ | ⇒ =

(2.14)
We see that for an isotropic medium, the magnitude of the birefringence is independent of the in-plane direction of the compression and has a principal axis aligned with the direction of the compression, while these conditions will not hold in general for a cubic medium.

2.2.4.Effect of a free surface
For a thin layer with a stress free surface, we can eliminate S3, in terms of S1 and S2. Recall that
3 | 12 | 1 | 2 | 11 3
| | | | 12
3 | 1 | 2
| | | | 11
( | ) | 0
( | )
T c S S | cS
c S | SS
| c
= | + | + | =
⇒ | =− | + | (2.15)
With Eq. (2.15) in Eq. (2.7) for the principal refractive indexes, we find

3
12 | 2 | 2 | 22
11 | 12 | 1 | 2 | 11 | 12 | 1 | 2 | 44 6
11
2 1 | ( | ) ( | )( | ) 4 2
n | c n n | p p | S S | p p | S S | pS
c ±
- | | | | =− | + | − | + | ± | − | − | + | | | | | | |

(2.16)
We see that the free surface alters the average refractive index change for a specified in-plane dilation S1 + S2, but does not alter the birefringence from the form given in Eq. (2.9). Noting that
rr | 1 | 2 S S | SS + | =+ θθ | , Eq. (2.16) can be used equally well to include a free surface for cases where
cylindrical coordinates are used.
2.3. Axisymmetric strain
For cylindrical objects, the natural coordinate system is generally also cylindrical. For an axisymmetric displacement field

ˆr u | r = u | (2.17)
the strain fields in the plane normal to z are
, r | r
rr
du | u S | S
dr | r = | = θθ | (2.18)
It is more convenient to use rectangular coordinates for the photoelastic calculations. The coordinate transformation yields
2 | 2
2 | 2
2 | 2
2 | 2
cos | sin | ( | )cos sin
( | )cos sin | sin | cos
( / )cos | ( / )sin | ( / | / )cos sin
( / | / )cos sin | ( / )sin | ( / )cos
xx | xy | rr | rr
xy | yy | rr | rr
r | r | r | r
r | r | r | r
S | S | S | S | SS
S | S | SS | S | S
du dr | u r | du dr u r
du dr u r | du dr | u r
θθ | θθ
θθ | θθ
θ | θ | θθ
θθ | θ | θ
θ | θ | θθ
θθ | θ | θ
- | | + | − | = | | | − | +
- | + | − = | | − | +

(2.19)
For using these results in photoelastic calculations recall that 6 | 2 xy S | S =
2.3.1. Uniform strain
Note that for a uniform radial expansion
0 () | ˆ r u r Sr = | r | (2.20)
we find | 0 / | / r | r du dr u r S = | = , so that with Eq. (2.19) we find 0 , | 0 xx | yy | xy S | S | SS = | = | = , independent of θ .
With these strains in Eq. (2.9), and recalling that 6 | 2 xy S | S = | we see that the birefringence vanishes
for a uniform in-in-plane dilation.
3. Thermoelasticity
In a cubic medium including thermal expansion effects requires modifying the constitutive relations for Hook’s Law and for the thermo-optic effect to read as

1 | 1 11 | 12 | 12
2 | 2 12 | 11 | 12
3 | 3 12 | 12 | 11
4 | 4 44
5 | 5 44
6 | 6 44

1

2

3 | 3
I | IJ
4

5

6

2
0
0
0
T | S ccc
T | S ccc
T | S ccc
T | S c
T | S c
T | S c

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
ατ | β
ατ | β
ατ | β −
- | | −
- | | − | | | | − = | | | | | | | | | | |
- | − | | | − | | | − |
∆= | − | | | | | | | | | | |
bp | τ

(3.1)

respectively, where α is the thermal expansion coefficient, τ is the temperature increase with respect to a reference temperature T0 for which the strain in a uniform object is taken to vanish, p is given in Eq. (2.2), and β = dn dT / is the thermo-optic coefficient for a freely expanding (stress-free) object. Note that the thermo-optic contribution does not cause any birefringence, but will alter the average refractive index change.

4. Cubic layer on a large substrate
We typically are concerned about a thin layer of a cubic material like AlGaAs on a much thicker substrate. As is typically done for thermal noise calculations, we can assume that the elastic distortions of the substrate can be taken to be independent of the thin layer on its surface, and then use those distortions of the substrate as boundary conditions to compute the elastic field in the thin
layer.
4.1. Layer strains in cylindrical coordinates
The in-plane displacements must be continuous at the interface of substrate and film. Assuming an
axisymmetric distortion of the substrate, , () rs ur , then we must have in the layer , () | () r | rs ur u r = | . If
the temperature excursion in the layer is τ ()r , then the displacement of the film away from its free value unconstrained by the substrate is
, 0 | 0 () | () | ( ) | () | ( ) r | r
r | r | rs δu r u r | r dr u r | r dr = | − | = | − ατ ′ ′ | ατ ′ ′ ∫ | ∫ | (4.1)
The strain in the film is then

,

,
, 0
() | () | ()
1 () | ( ) | () | ()

r
rr | rr s
r r | rs
s
du Sr | S r | r
dr
u u
S r | r dr S r | r
r | r | r
θθ | θθ

δ
ατ

δ
α τ | ατ
= | = | −
= | = | − | ′ ′ ≡ | −∆ ∫

(4.2)

where the average temperature difference between the origin and a radius r is implicitly defined as
∆τ ()r in the final form of Eq. (4.2). Note that for a uniform temperature field 0 τ | τ ()r = , the averaged
temperature change takes the same value, i.e. | 0 ∆ | = | = τ | τ | τ () () r | r | .
4.2. Layer strains in rectangular coordinates
With the transformation given in Eq. (2.19) applied to the strains given in Eqs. (4.1) and (4.2), we find for the strains in rectangular coordinates
2 | 2
1 | ,
2 | 2
2 | ,
6 | ,
| | cos | sin
| | sin | cos
2 | 2 | 2 ( | )sin cos
xx | xx s
yy | yy s
xy | xy s
SS | S
SS | S
S | S | S
ατ | θ τ | θ
ατ | θ τ | θ
ατ τ θ θ
= | = | − | +∆ | |
= | = | − | +∆ | |
= | = | − | −∆

(4.3)

4.3. Thermo-optic index perturbation
For radially symmetric temperature and strain fields in a film with a free surface, the two principal refractive indexes in the layer are, with Eqs. (4.3) in Eq. (2.16)
( | ) ³
12
11 | 12 | 1, | 2,
11
2 | 2 2 | 2
11 | 12 | 1, | 2, | 44 | 6,
12 | ( | ) 2
( | ) | ( | )cos 2 | 4 | ( | )sin 2
s | s
s | s | s
n | c n | n | pp | S | S
c
p p | S | S | pS
ε | βτ | α τ τ
ατ τ | θ | ατ τ | θ
± | ±
= | ≈ + | − | + | − | | | + | − | +∆ | | |
- ± | − | − | − | −∆ | + | − | −∆ | | | | |

(4.4)
where we have added the thermo-optic contribution to the average index change, as required by Eq. (3.1)
The birefringence is then
2 | 2 3 | 2 | 2
11 | 12 | 1, | 2, | 44 | 6,
2 | 2 3 | 2
11 | 12 | 1, | 2, | 6,

2 3
11 | 12 | 1, | 2, | 6,
( | ) | ( | )cos 2 | 4 | ( | )sin 2
( | ) | ( | )cos 2 | ( | )sin 2
( | ) | ( | )cos 2 | (
s | s | s
s | s | s
isotropic | s | s | s
B n p p | S | S | pS
np p | S | S | A S
np p | S | S | S
ατ τ | θ | ατ τ | θ
ατ τ | θ | ατ τ | θ
ατ τ | θ | ατ τ
=− | − | − | − | −∆ | + | − | −∆ | | | | | |
=− | − | − | − | −∆ | + | − | −∆ | | | | | |
→− | − | − | − | − ∆ | + | − | − ∆ | |

2
- | )sin 2θ |

(4.5)
and using Eq. (2.8) a principal axis is at an angle θ0 to x obeying

6,
0
1, 2,

6,

1, | 2,
( | )sin 2 tan 2
( | )cos
( | )sin 2
( | )cos

s

s s

s
isotropic
s s

S
A
S S
S
S | S
ατ τ | θ
θ
ατ τ | θ
ατ τ | θ
ατ τ | θ
− | −∆ = | − | − | −∆ | 2
− | −∆
→
− | − | −∆ | 2

(4.6)

5. Applications
5.1. Uniform temperature change
If a layer is bonded to a substrate at room temperature and then cooled to a cryogenic temperature, strains will be induced in the film if its thermal expansion coefficient α is mismatched to that of the
substrate, α s . A uniform temperature excursion the substrate, i.e. | 0 τ | τ | τ () | () r | r = = ∆ | , would lead to a
displacement field
0 ˆ s u | r =ατ r | (5.1)
neglecting a z displacement irrelevant here. According to Eq. (2.20) and following, the substrate
strains are then 1 | 2 | 0 | 6 , | 0 s | s | s | s S | S | S = | = | = ατ | . According to Eq. (4.4), the index change in the film is
isotropic, and given by

3
12
0 | 11 | 12 | 1 | 2 | 0
11
3 | 12
0 | 11 | 12 | 0
11
2 1 | ( | 2) 2
2 1 | ( | )
s | s

s

n | c n | n | pp | SS
c
c
np p
c
δ | δ | βτ | ατ
βτ | α α τ
+ | −
= | = | − | + | − | + | − | | | |
= | + | + | − | − | | | |

(5.2)
and thus B = 0 . This result applies equally well to cubic and isotropic layers.
5.2. Temperature rise and strain due to absorption of a Gaussian beam
For absorption of the incident optical beam by the mirror layer, there will be a radially varying temperature field in the substrate and the mirror layer, and as a result there will be a radially varying strain in the mirror layer. For beams that are large compared to the mirror layer thickness, we can estimate the strain by computing the temperature field in the substrate neglecting thermal transport in the coating, computing the resulting strain in the substrate assuming it is unaffected by the mechanical properties of the mirror layer, and then assuming the mirror layer displacements follow those of the substrate. That problem is addressed analytically for a cylindrical mirror using a Dini series solution in P. Hello and J. Y. Vinet, “Analytical models of thermal distortions in massive mirrors heated by high power laser beams,” French J. Phys. 51, 1267–1282 (1990). With reasonable accuracy, those results can be approximated as described in P. Lu et al, “Wavefront distortion of the reflected and diffracted beams produced by the thermoelastic deformation of a diffraction grating heated by a Gaussian laser beam,” J. Opt. Soc. Am. A 24 pp. 659-668 (2007). When the beam is small compared to the mirror, some further simplifications are possible. When the beam is small compared to a characteristic length describing the importance of heat loss via radiation to the environment vs conduction into the substrate (discussed in following section), a simple universal form emerges for the temperature and strain fields. While detailed numerical accuracy would require FEM modeling or the use of the Hello and Vinet series results, the simple universal form here is adequate to understand the general magnitude and scaling of the problem, particularly in the central portion of the Gaussian beam.

5.2.1. Temperature and substrate displacement fields
For an incident Gaussian beam of the form | 2 | 2
0 ( ) | exp( 2 / ) G | G Ir I | r w = | − | , evaluating Eq. (A8) of Lu
assuming the characteristic length for surface heat loss by radiation, 3 | 3
0 / [4 ( | )] th | s | ext l k | TT ≡ | − εσ | , is
large compared to w, we find for the temperature distribution at the surface of the mirror
() | ( ) c τ | ττ r | R = | (5.3)
where
2 | 2
0

2
() ( )

abs
c
s
R

P
wk
R e JR

τ
π
τ −

≡

≡

(5.4)
R rw ≡ / , Pabs is the absorbed optical power, and s k is the thermal conductivity of the substrate, ε is the emissivity of the mirror, and σ is the Stefan-Boltzmann constant. Taking the emissivity to be 0.5, for room temperature th l is 47 m for silicon, 11 m for sapphire, and 0.46 m for silica. For cryogenic temperatures, th l is much larger due to the T3 factor in the denominator, and the increase in thermal conductivity. Corrections for finite w/lth are discussed in Lu.
With Eq. (B11) of Lu, we have the radial displacement in the substrate as
, | , () | ( ) rs | cs u r u uR = | (5.5)
where

2

,

2 | 2
0 | 1
(1 | ) 22
() | ( ) | ( )

s abs
c s | s
s
R

P
u
k
u R Re | I R | I R
α | ν
π

−

≡ | +
≡ | + | |

(5.6)
and ν s is the substrate Poisson ratio, and I0 and I1 are modified Bessel functions of the first kind.

5.2.2.Substrate strain fields in cylindrical coordinates
Given the displacement field in Eq. (5.6), the strain fields in the substrate are

2

,
, | ,
2 | 2
0 | 1

()
() | ( ) | ( )

c s
rr s | c s | rr

R
rr

du u
S | u | SR
dr | w
S R e | IR | IR ⁻
= | =
= | | − |

(5.7)
and

2

, | ,
,
2 | 2
0 | 1
() | | ( )
() | ( ) | ( )
rs | cs
s

R

u | u
S r | | SR
r | w
S R e | IR | IR
θθ | θθ

θθ

−

= | =
≡ | + | |

(5.8)

5.2.3.Substrate strain fields in rectangular coordinates
With the transformation given in Eq. (2.19) applied to the strains given in Eqs. (5.7) and (5.8), we have for the substrate strains in rectangular coordinates

2

2

2

,

2 | 2
1, | 0 | 1
2 | 2
2, | 0 | 1
2
6, | 1
[ ( , )] | ( , )
( , ) | ( , ) | ( ) | ( )cos(2 )
( , ) | ( , ) | ( ) | ( )cos(2 )
( , ) 2 ( , ) 2 | ( )sin 2

c s

R
s | xx
R
s | yy
| | | R
s | xy u
Sr | SR
| w
S R | S R | e | IR | IR
S R | S R | e | IR | IR
S R | S R | | e IR
θ | | θ
θ | θ | θ
θ | θ | θ
θ | θ | θ
| | −

−

| | | −
= | | |
= | = | | − |
= | = | | + |
= | = −

(5.9)

5.2.4. Photoelastic birefringence
The strains in the layer can be evaluated by substituting Eqs. (5.9) for the substrate strains and Eq.
(5.4) for the temperature field into Eqs. (4.3). Those in turn lead to the layer birefringence given in Eq. (4.5) taking the form

2

2

2 | 2 3 | 2 | 2
11 | 12 | 1, | 2, | 44 | 6,
3 | , | 2 | 2 | 2 | 2
11 | 12 | 1
3 | 2 ,
11 | 12 | 1
( | ) | ( | )cos 2 | 4 | ( | )sin 2
1 2 | ( | ) | ( ) | ( | ) cos 2 | sin 2 1
1 2 | ( | ) | () | ( | ) 1
s | s | s
c s | R
s | s
c s | R
isotropic
s | s
B n p p | S | S | pS
u
n | p p e IR | A
w
u
n p p e IR
w
ατ τ | θ | ατ τ | θ
α ττ | θ | θ
να
α
ττ
να

−

−

=− | − | − | − | −∆ | + | − | −∆ | | | | | |
- | =− | − | | + | −∆ | +
- +
→− | − | | + | − ∆
- +

(5.10)
The orientation of a principal axis is, with Eq. (4.6)

1
0

1 tan ( tan 2 )
2
θ | θ A ⁻ = | (5.11)
To evaluate these equations we need in addition to the temperature τ ()r the averaged temperature ∆τ ()r defined in Eq. (4.2).
5.2.5. Application to GaAs
We can simplify Eq. (5.10) taking advantage of the large anisotropy factor in GaAs, A2 = 33 >> 1 to keep only one term in the radicand. We find

2
2

2

3 | 2 ,
1 | 11 | 12 | 1
| | 3
2
44 | 1

0

1 2 | ( | ) | ( ) | ( | ) sin 2 1
1 | (1 | ) | ( ) ( | ) sin 2 2
(1 | ) ( ) | ( ) sin 2
c s | R
A
s | s
abs | s | R s

s

s
s | s | m

u
B | n | p p Ae I R
w
n P p | e IR kw
B | fR f R
α ττ | θ
να
α | α | ν | ττ | θ
π | α
α | ν | θ
α

−

−

→− | − | | + | − ∆
- +
- | = − | + | + −∆ | |
- | ≡ | + | + | |
(5.12)

where

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
() | ( )
() ( | )

abs

| s
R
s

m

np P B
k w
fR e IR
fR

α
π

ττ

−

≡−

≡
≡ −∆

(5.13)
The functions appearing in Eq. (5.12) are given in closed form as functions of R, (with 2 | 2
0 () R τ e JR ⁻ = | from Eq. (5.4)) with the exception of ∆τ which is an integral given in Eq. (4.2) as

2

1
0
1 | 2
0 0
() | ( )
| ()

R

R | R
R R | R dR
R | e J R dR
τ | τ ⁻
− | − ′
∆ | = | ∆ | ′ | ′
= | ′ | ′

∫
∫

(5.14)
which must be evaluated numerically. The following is a plot of () () | () mfR | R | R = | −∆ τ | τ | vs R.

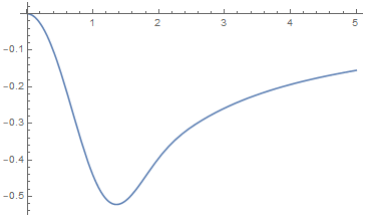
[picture p25: figure]

We see that () mfR has a peak value of -0.52 at R = 1.38, and goes as ~0.77/R for R >~2 .
The other function in Eq. (5.12), () sfR , which is less important for GaAs on SiO2 due to the latter’s much smaller thermal expansion, is plotted as

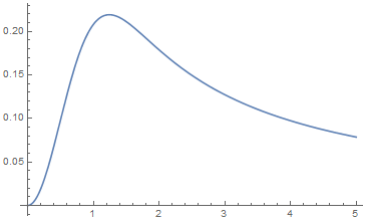
[picture p26: figure]

5.3. Irregular birefringence
Strains introduced during mirror growth or bonding may not be azimuthally symmetric or uniform across the face of the mirror (for example, if stick-slip motion occurs during bonding). For such cases there is no a priori model for the birefringence expected without knowledge of the strains. However, given a measurement of the strength and principal axes of the birefringence, one can compute the strength and principal axes of the strains that must be present to cause that birefringence, which may be of use in diagnosing and ameliorating their source. We first address the case of a single layer. The generalization to a multilayer mirror is given in section 6.4.
Assume a measurement of the birefringence B and θ0 , its principal axis orientation with respect to the crystalline x axis is available. We seek to compute the principal axis orientation of the strain, θ
- ,
and the difference of the two principal strain components, 1 2 SS − .
We begin with Eqs. (2.9) and (2.8). Eq. (2.8) can be written as
6 | 1 | 2 | 0 AS | S S = | − ( | ) tan 2θ | (5.15)
With Eq. (5.15) in Eq. (2.9), we have for the birefringence
3 | 2
11 | 12 | 1 | 2 | 0

0
1 | 2 | 3
11 | 12
( | )( | ) 1 tan 2
cos 2
| ( | )

B np p S S
B SS
np p

θ
θ
=− | − | − | +
⇒ | − =− | −

(5.16)
Eq. (5.16) in Eq. (5.15) then yields
0 | 0
6 | 3 | 3
11 | 12 | 44
1 | sin 2 | sin 2
( | ) | (2 )
B | B S
An p p | n p
θ | θ = − | = − − | (5.17)
The principal axis system for the strain is the one in which the shear 6 S vanishes. Rotate the strain tensor by an angle θ
- with respect to the crystalline x axis. In this system, rotation of the strain tensor in the crystal axis system shows that
2 | 2
1 | 1 | 2 | 6
2 | 2
2 | 1 | 2 | 6
2 | 2
6 | 1 | 2 | 6
1 | 2 | 1 | 2 | 6
6 | 1 | 2 | 6
cos | sin | cos sin
sin | cos | cos sin
2sin cos | 2cos sin | (cos | sin )
cos 2 ( | ) sin 2
| sin 2 ( | | ) cos 2
S | S | S | S
S | S | S | S
S | S | S | S
SS | SS | S
S | SS | S
θ | θ | θθ
θ | θ | θθ
θ θ | θθ | θ | θ
θ | θ
θ | θ
= | + | +
= | + | −
=− | + | + | −
⇒−= | − | +
=− | − | +

(5.18)
With Eq. (5.18), we can find the principal axis orientation θ p
- by setting 6 S = 0 . We find

6
0
1 | 2
1 tan 2 | tan 2 p

S
SS A
θ | θ = | = −
- (5.19)
where second form follows with Eq. (5.15).
To find the principal strains, begin with Eqs. (5.17) and (2.8) in Eq. (5.18):

( )

0

1 | 2 | 1 | 2 | 6

0
3 | 0
44
0 | 2 | 2 | 2 | 2 | 2
3 | 3 0 | 0 | 0
44 | 44
/4 | 3
| 44
cos 2 ( | | ) sin 2
sin 2 sin 2 1 cot 2 | cot 2
(2 )
sin 2 | 1 | cot 2 | sin 2 | cos 2
(2 ) | (2 )

(2 )

p | p p
p | p
SS | SS | S
B | | A
np
B | B A | A
np | | np
| B np

θπ

θ | θ
θ | θ | θ | θ
θ | θ | θ | θ

→

− | = | − | +
= − | + | |
=− | + | =− | +

→−

(5.20)
where second step follows from using Eq. (5.19) for cot 2θ p
- . By similar substitutions it can be
verified that 6, | 0 p S = | .
Eqs. (5.19) and (5.20) are the desired relation between the measured quantities B and θ0 and the principal strain magnitudes and axes. Since the birefringence is only sensitive to the difference between the principal strains, determining their absolute magnitude would require another measurement such as the phase on reflection (rather than just the difference of the phase for orthogonal polarizations) or direct strain characterization via XRD or other material characterization methods.
The case of a mirror rather than a single layer with irregular birefringence is addressed in section
6.4.
6. Multilayer mirrors
The previous analysis applies to a single uniform layer. Actual mirrors are of course comprised of a a multilayer dielectric stack. Computation of the changes in the properties of the mirror will depend on the changes in properties of each layer individually.
6.1. Refractive indexes in each layer
Tracing through the analysis for the cubic case, we see that to find the changes to the refractive index in each layer, we simply have to assign the appropriate material properties in each layer, while noting that the temperature τ , as well as the strains S1, S2, and S6 are continuous through the layers, so do not require a subscript J . Eq. (2.15) for S3 accounting for the free surface becomes

12,
3, | 1 | 2
| 11,
( | 2) J
J | J | J
| J

c
S | SS
c
− | =− | + − ατ | ατ | (6.1)
Eq. (2.7) for the principal refractive indexes in layer J becomes

3
12, | 2 | 2 | 2 | 2
11, | 12, | 1 | 2 | 11, | 12, | 1 | 2 | 44, | 6
11,
1 2 | ( | ) ( | )( | ) 4 2
J | J
J | J | J | J | J | J | J
J
n | c
n | n | p | p | SS | p | p | SS | pS
c ±
≈− | + | − | + | ± | − | − | + | | |

(6.2)
where the subscript J indicates a quantity evaluated in layer J.
The displacement away from its free value in each layer is modified from the form in Eq. (4.1) to
, | , 0 | 0 () | () | ( ) | () | ( ) r | r
rJ | r | J | rs | J δu r u r | r dr u r | r dr = | − | = | − ατ ′ ′ | ατ ′ ′ ∫ | ∫ | (6.3)
Following through to Eq. (4.4) for the principal refractive indexes in each layer
( | ) ³
12,
, | 11, | 12, | 1, | 2,
11,
2 | 2 2 | 2
11, | 12, | 1, | 2, | 44, | 6,
12 | ( | ) 2
( | ) | ( | )cos 2 | 4 | ( | )sin 2
J | J
J | J | J | J | J | s | s | J
J
J | J | s | s | J | J | s | J
n | c
n | n | p | p | S | S
c
p | p | S | S | p | S
βτ | α τ τ
ατ τ | θ | ατ τ | θ

±

≈ + | − | + | − | | | + | − | +∆ | | |
- ± | − | − | − | −∆ | + | − | −∆ | | | | |

(6.4)
The birefringence in each layer changes from that in Eq. (4.5) to
2 | 2 3 | 2 | 2
11, | 12, | 1, | 2, | 44, | 6,
2 | 2 3 | 2
11, | 12, | 1, | 2, | 6,

3
11, | 12, | 1, | 2,
( | ) | ( | )cos 2 | 4 | ( | )sin 2
( | ) | ( | )cos 2 | ( | )sin 2
( | ) | (
J | J | J | s | s | J | J | s | J
J | J | J | s | s | J | J | s | J
isotropic | J | J | J | s | s | J
Bnp | p | S | S | p | S
np | p | S | S | A S
np | p | S | S
ατ τ | θ | ατ τ | θ
ατ τ | θ | ατ τ | θ

ατ τ

=− | − | − | − | −∆ | + | − | −∆ | | | | | |
=− | − | − | − | −∆ | + | − | −∆ | | | | | |
→− | − | − | − | − ∆ | 2 | 2
6, )cos 2 | ( | )sin 2 s | J | θ | ατ τ | θ + | − | −∆ | S | |

(6.5)
and the orientation of the principal axis in each layer is instead of Eq. (4.6) given by

6,
0.
1, 2,

6,

1, | 2,
( | )sin 2 tan 2
( | )cos
( | )sin 2
( | )cos
s | J
J | J
s | s | J
s | J
isotropic
s | s | J

S
A
S S
S
S | S
ατ τ | θ
θ
ατ τ | θ
ατ τ | θ
ατ τ | θ
− | −∆ = | − | − | −∆ | 2
− | −∆
→
− | − | −∆ | 2

(6.6)

6.2. Reflection phase of the mirror stack
Changes in the reflection phase from the mirror stack due to photo-elastic effects can be calculated similarly as that from electro-optic effects. In the document “Electro-optic phase shifts in AlGaAs mirrors” it is shown that for an isotropic mirror stack, given the logarithmic derivative of the optical path length of each layer with respect to a parameter γ , i.e.

1 J 3,J
J
J

dn dS
nd d

κ
γ | γ
= | + | (6.7)
where 3 S is the strain in the surface normal direction, the reflectivity of a quarter-wave stack operated at the center of the reflection band is changed by

2
0
/ ( | )1( / )
L | H
LH | H L
L | H
d | nn
n | n
d | nn
φ | πκ | κ
γ
≈− | + | − | (6.8)
where subscripts J = [L, H] stand for low and high index layers, respectively.
For a birefringent stack, one should in principle use, rather than the conventional 2x2 transfer matrix description, a 4x4 transfer matrix description to account for the possible polarization conversion in each layer (I believe this is given in Pochi Yeh’s Optical Waves in Layered Media text, but I don’t have it handy to check). For the present purposes, and in any case absent data for the photoelastic tensor in different AlGaAs compositions, we assume that the principal axes are aligned in each of the mirror layers, so that the conventional results for an isotropic mirror can be applied to each of the principal axes of the birefringent mirror, the important result being the difference in reflection phase for light polarized along the two principal axes.
6.3. Mirror thermoelastic birefringence.
For thermoelasticity, we take the parameter Pabs γ = , so that we can compute the birefringence per watt of absorbed power. With Eq. (6.8) the mirror birefringent reflection phase is then
[ | ] 2

2

2

/ | ( | ) | ) 1( / )

/
1( / )
/
1( / )
m | abs
| abs | abs
L | H
L | H | H | H | L | L | abs
L | H
L | H | L | H | H | H | L | L
abs
L | H | H | abs | abs | L | abs | abs
L | H
L | H
d | d B | P
dP | dP
nn | n | n | P
nn
n n | n dn | dn | n dn | dn | P
n n | n dP | dP | n dP | dP
nn
nn
φ | φ φ φ
π | κ | κ | κκ

π

π

+ | −
+ | −
+ | − | + | −
+ | − | + | −
- | =−= | − | |
- | = − | | − | +( | −
- −
- | | | | | = − | | | | | − | + | −
- | − | | | | |
= − | −
L | H | H | L
abs
H | abs | L | abs
n dB | n dB P
n dP | n dP
- | | | | +

(6.9)
where the isotropic change in length described by S3, drops out in the third form, and the fourth form uses the definition of the birefringence in each layer.
Eq. (6.9) can be evaluated with the expression for the birefringence from Eqs. (5.12)and (5.13). We
find
0 | 0
2
/ | (1 | ) ( ) | ( ) sin 2 1( / )
L | H | L | H H | L | s
m | abs | s | s | m
L | H | H | abs | L | abs
nn | n | n dB | dB B | P | fR f R n n | n dP | n dP
α
π | ν | θ
α
- | | | = − | | | + | + | + | | − | | | | (6.10)
The only parameters of the coating that appear in B0 from Eq. (5.13)are 44 α, ,and p | n .
6.4. Mirror with irregular birefringence
The evaluation of the principal strains and principal axes from measurements of the birefringence on reflection from a multilayer mirror can be connected to the analysis of a single layer given in section 5.3 in much the same way that the thermoelastic birefringence of a mirror was related in section 6.3 to the single layer birefringence given in section 5.2.4. We specialize here to a quarter-wave stack, though the method is generalizable to other mirror designs.
Rewriting Eq. (6.9) for the birefringent phase in reflection for a mirror stack, in the form

2

2

2

/
1( / )
(/ ) 1
1( / )
L | H | L | H
m | H | L
H | L | L | H
L | L | H
H
H | L | H
n | n | nn B | B | B
n | n | nn
n | nn B
n | nn

π

π

≈− | + | | −
≈− | + | | −

(6.11)
where the second form follows with the assumption that the photoelastic properties other than the n3 factor are similar in the high and low index layers. With Eq. (6.11) the birefringent phase measured for the mirror stack can be related to that of the high index layer, which in turn can be related to the strain magnitude and principal axes according to Eqs.(5.19) and (5.20).
6.5. Application to AlGaAs mirrors
6.5.1. Thermoelastic birefringence
The thermal expansion coefficients of GaAs and AlGaAs appear to be similar, and I don’t have data for the photoelastic coefficients of AlGaAs, so we may as well take them as the same in the two materials. In that case, Eq. (6.10) reduces to
0 | (1 | ) ( ) | ( ) sin 2 s B B | fR f R m | m | s | s | m
α | ν | θ
α
- | = | + | + | | | (6.12)
where
44 | 2 | 2
0 | 2

/
2 | 1( / )
abs | L | H
m | H L | LH
s | L | H
p | nn P B | n n nn
k w | nn
π α | | ≡− | | | + | | − | (6.13)
With material properties from Appendix 1, we find
[ | ] ³ [W] 8.9 10 | 0.11 ( ) | ( ) sin 2 [cm]
abs
m | s | m
P B | fR f R
w
θ ⁻ = | × | + | (6.14)
We see that for 5 W absorbed from a 5 cm radius beam, the max birefringent phase will be 4.5 mrad. Using the same scaling, if there were an absorber of 0.5 mm in size, it would create a birefringence of ~450 mrad per watt of absorbed power. Because of the weak (only 1/r) rolloff of the birefringence away from the absorber, a larger area than that of the absorber itself would be affected.

6.5.2.Irregular birefringence
Under the same assumptions for material properties as in section 6.5.1, the relation between birefringence of reflection phase for an AlGaAs HR and the birefringence in the high index layer is

18.2

m
H
B B = | (6.15)
With Eq. (5.20) for the connection between layer birefringence and the difference between the principal strain components we have

0

2 | 2 | 2
1 | 2 | 3 | 0 | 0
44
2 | 2 | 2
| | 3 | 0 | 0
44
6 | 2 | 2 | 2
0 | 0
6
/4

sin 2 cos 2
(2 )
/18.2 sin 2 cos 2
(2 )
9.3 10 | [mrad] sin 2 | cos 2
9.3 10 | [mrad]

H
p | H
| m
| H

m

m

B SS | A
np
B | A
np
B | A

B θπ

θ | θ
θ | θ
θ | θ ⁻

−
→
− | = | +
= | +
= | × | +
→ ×
(6.16)
The difference in the principal stress components corresponding to these strains will depend on the orientation of the principal axes. For the case 0 θπ = /4 the result is
1 | 2 | 44 | 1 | 2 2 | S
~ 1.1MPa [mrad]
p | p

m

TT | c | S B
− | = | − |

(6.17)
where c44 = 59.4 GPa is the shear stiffness of GaAs. Note that this is the difference between the principal stresses – their individual magnitudes could be much larger.
7. Extensions and future work
There are several approximations involved in the results given here.
The incorporation of the stress-free surface into the strain fields of a single layer given in Eq. (2.15) was used for the individual layers of a multilayer in Eq. (6.1). Strictly speaking, this is correct only if the ratio 12 11 cc/ is the same in both the mirror layer materials (effectively that the Poisson ratio is the same). One could more properly evaluate the effective tetragonal-symmetry material tensors of the multilayer using the results of “Effective Thermoelastic Medium”, and trace through an analysis similar to the one given here with those effective parameters, but this added complexity is perhaps worthwhile only if reliable data for the stiffness tensors and the thermal expansion coefficients vs composition of AlGaAs were available.
The thermal and strain fields for a Gaussian-distributed heat source at the surface of the mirror are simple analytical approximations, and neglect the finite diameter of the mirror compared to the beam size. The exact series results of Hello and Vinet, or FEM calculations could be used to obtain greater accuracy, but the results given here capture the scaling with absorbed power, beam size, and material parameters, and are accurate to ~20% for typical LIGO geometries, and negligibly different from more detailed calculations for beams or other heat sources small compared to the mirror diameter.

If the thermoelastic birefringence proves to be problematic for the interferometer performance, it is likely that mirror coating designs other than a simple quarter wave stack could be found to partially mitigate the problem. These however would be different from those used to eliminate thermoelastic noise, as those make use of the interplay between thermal expansion, thermo-optic and thermoelastic effects. as the former two are isotropic while the latter is birefringent, they could not fully compensate for the latter.

8. Appendix 1: Material parameters
8.1. GaAs
8.1.1. photoelastic tensor
p11 = -0.165, p22 = -0.140, p44 = -0.072, A = 5.76
8.1.2. thermal expansion
α = 5.73 x 10-6 K-1
8.1.3. refractive index: AlxGa1-xAs
nH(x = 0.1) = 3.45, n(x = 0.9) = 3.00
8.2. Silica
kth = 1.38 W-m-1K-1
αs = 0.55 x 10-6 K-1
νs = 0.17
