dancvan/AlGaAs_electrooptic_effect/code/fea_electrodes/matlab_script_stefan/poisson/results_04_07_2020/front_of_optic_voltage.png

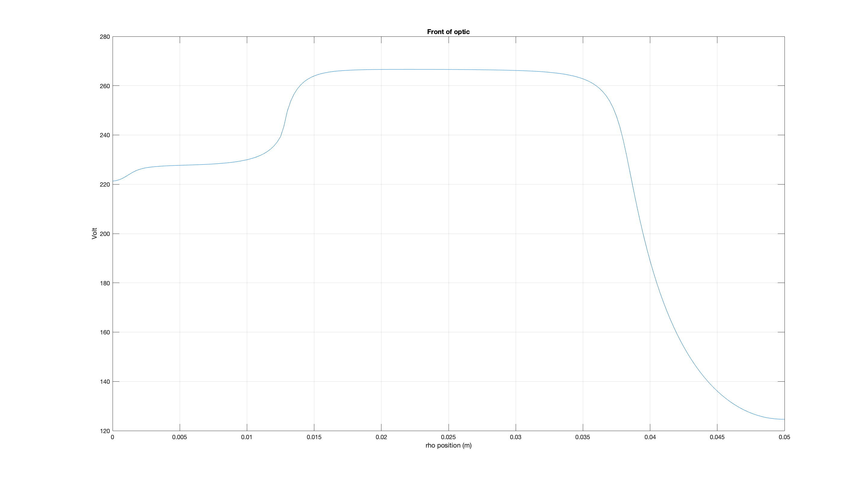
code/fea_electrodes/matlab_script_stefan/poisson/results_04_07_2020/front_of_optic_voltage.png
