dancvan/AlGaAs_electrooptic_effect/documents/internal_notes/blackboards/office_blackboard1.jpg

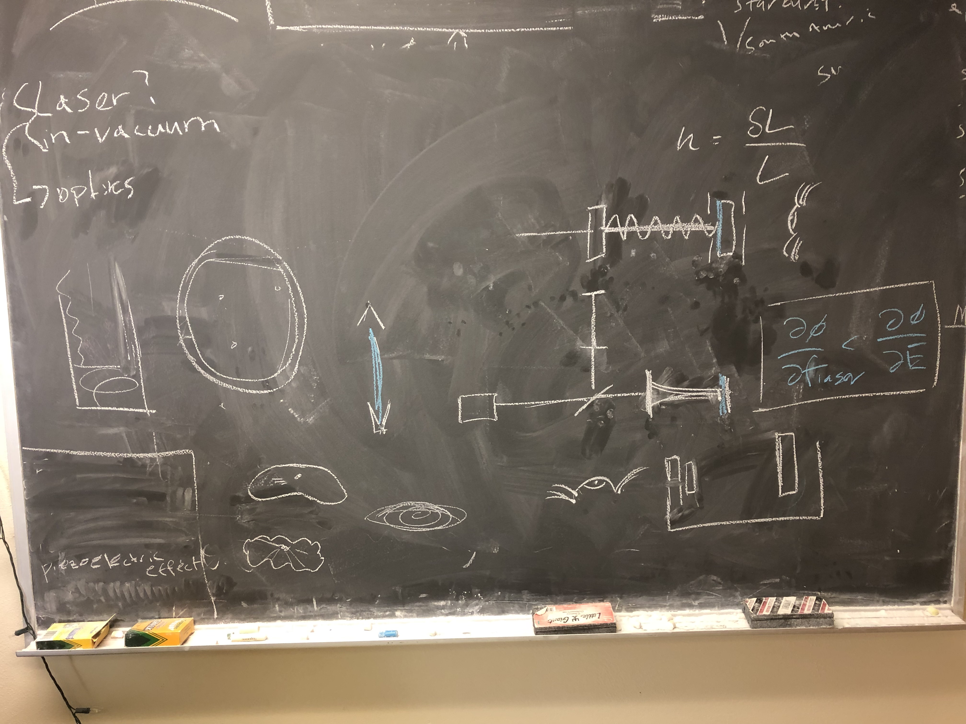
documents/internal_notes/blackboards/office_blackboard1.jpg
