dancvan/AlGaAs_electrooptic_effect/documents/internal_notes/elogs/811/811_20200924172152_silicatantalacoating.png

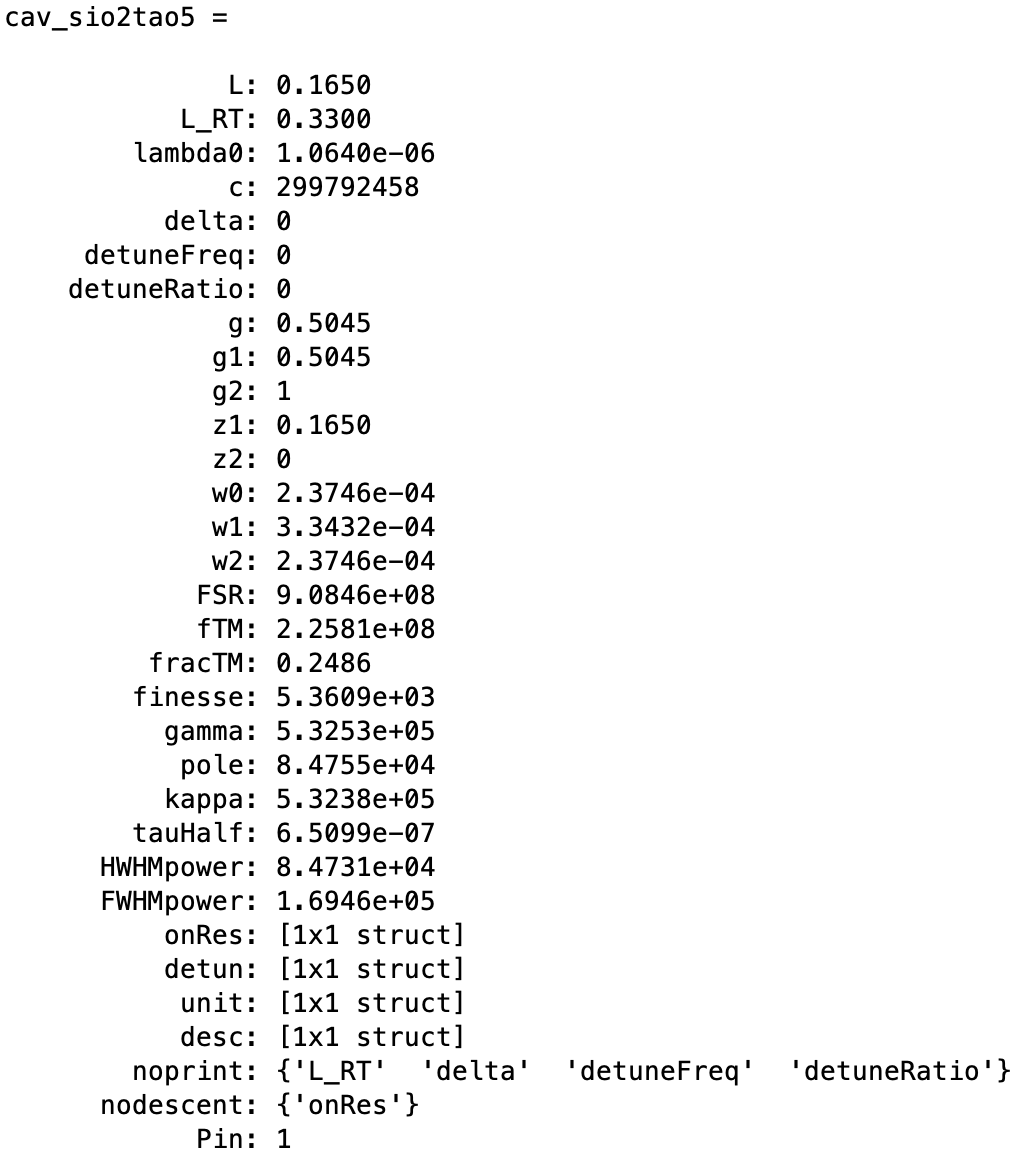
documents/internal_notes/elogs/811/811_20200924172152_silicatantalacoating.png
