dancvan/AlGaAs_electrooptic_effect/documents/internal_notes/elogs/815/815_20201021042615_spicediagram.png

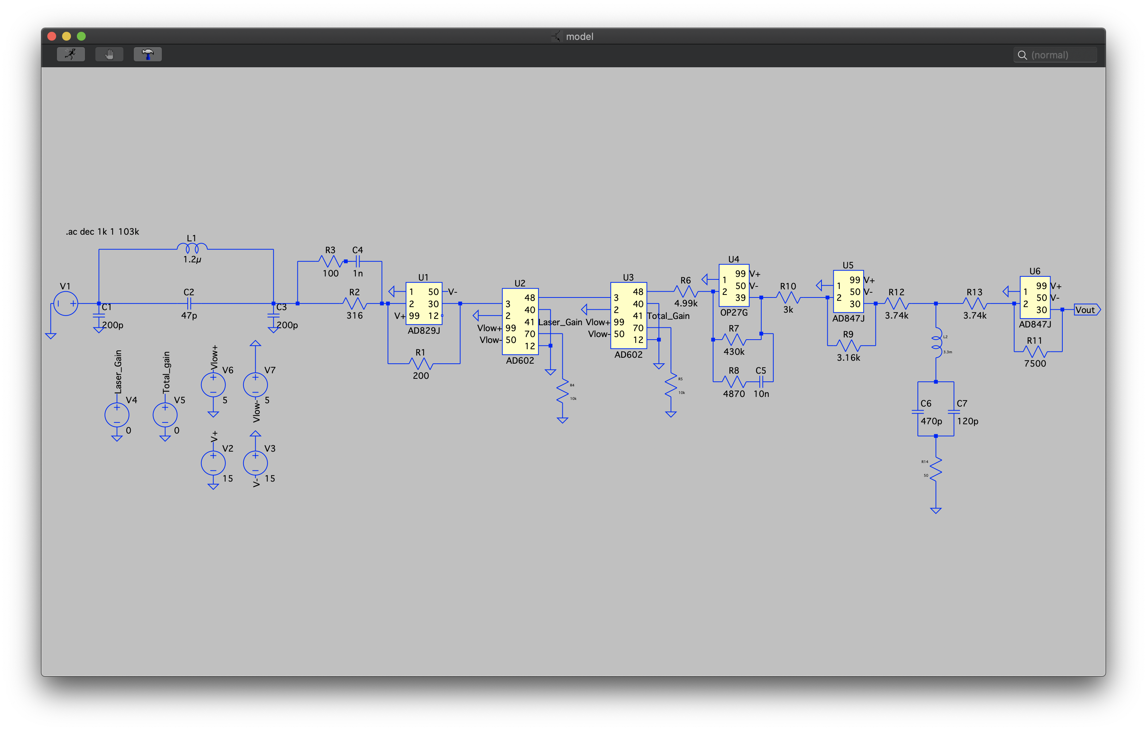
documents/internal_notes/elogs/815/815_20201021042615_spicediagram.png
