dancvan/AlGaAs_electrooptic_effect/documents/internal_notes/elogs/815/815_20201021050724_fsslgtg.png

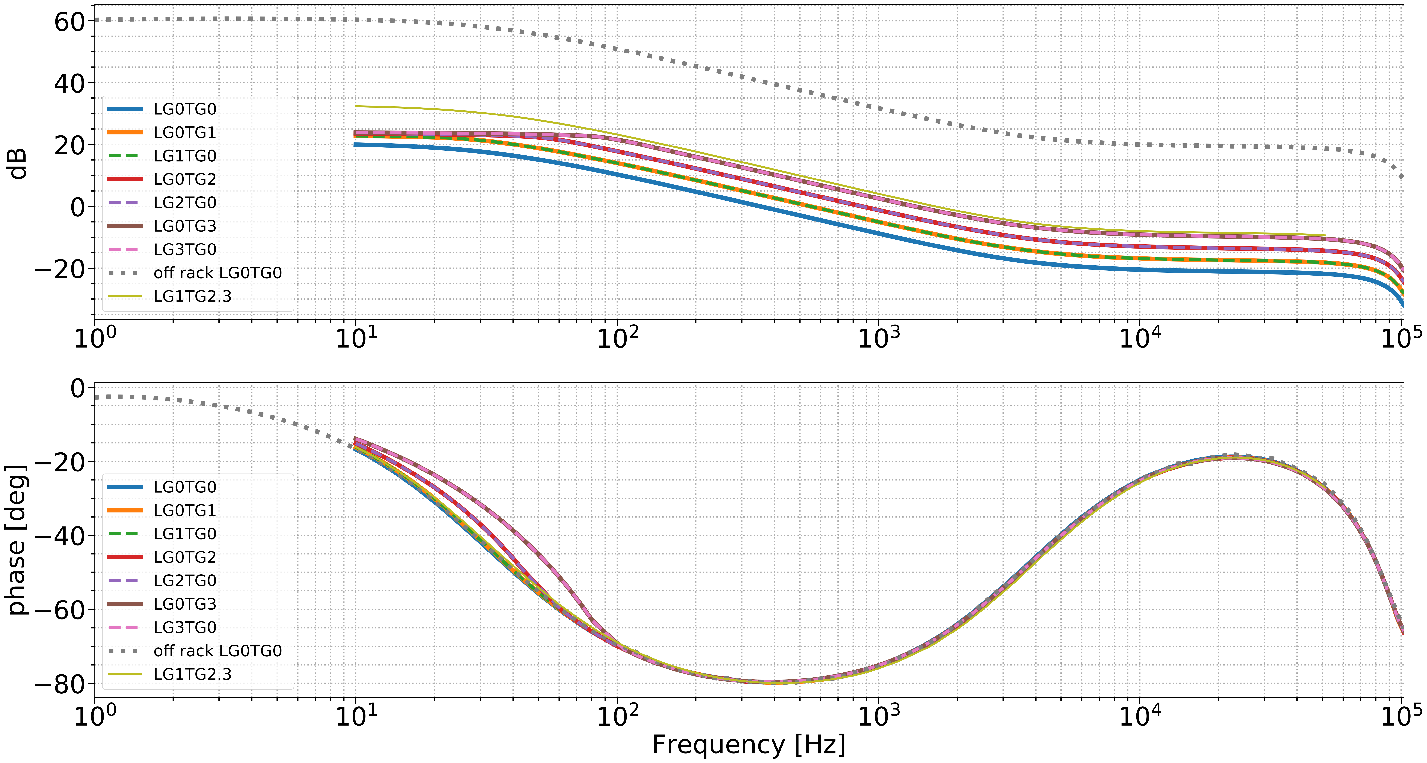
documents/internal_notes/elogs/815/815_20201021050724_fsslgtg.png
