dancvan/AlGaAs_electrooptic_effect/documents/internal_notes/meeting_notes/group_meeting_05_30_2019/IMG_9926.jpg

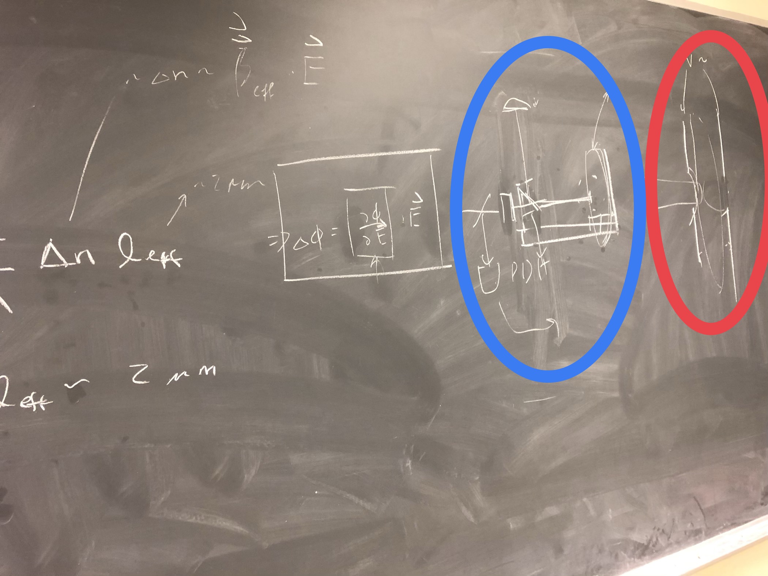
documents/internal_notes/meeting_notes/group_meeting_05_30_2019/IMG_9926.jpg
