dancvan/AlGaAs_electrooptic_effect/documents/internal_notes/meeting_notes/noise/stefan_back_of_the_envelope_computations/back_of_the_envelope_noise.jpg

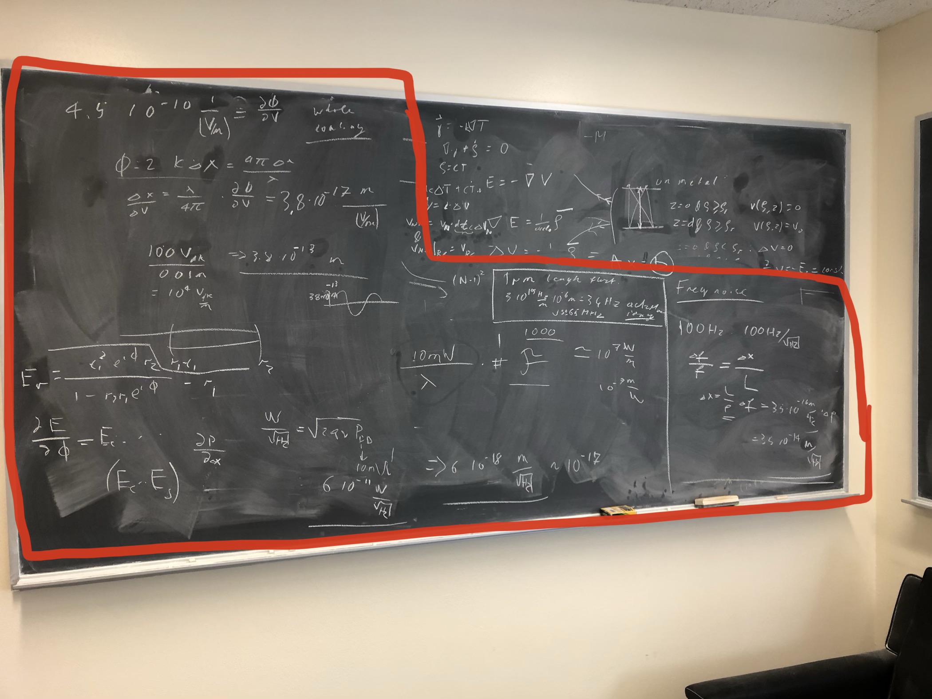
documents/internal_notes/meeting_notes/noise/stefan_back_of_the_envelope_computations/back_of_the_envelope_noise.jpg
