dancvan/AlGaAs_electrooptic_effect/documents/internal_notes/meeting_notes/update_1/PDH_closed_loop.png

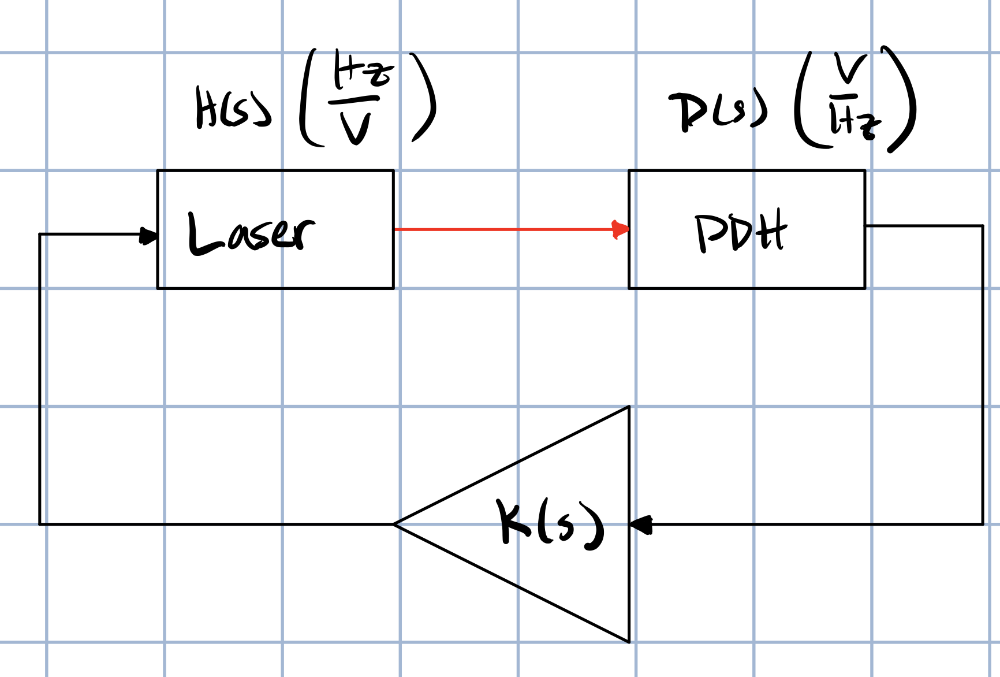
documents/internal_notes/meeting_notes/update_1/PDH_closed_loop.png
