dancvan/AlGaAs_electrooptic_effect/documents/internal_notes/meeting_notes/update_1/Screen Shot 2019-06-17 at 12.55.35 PM.png

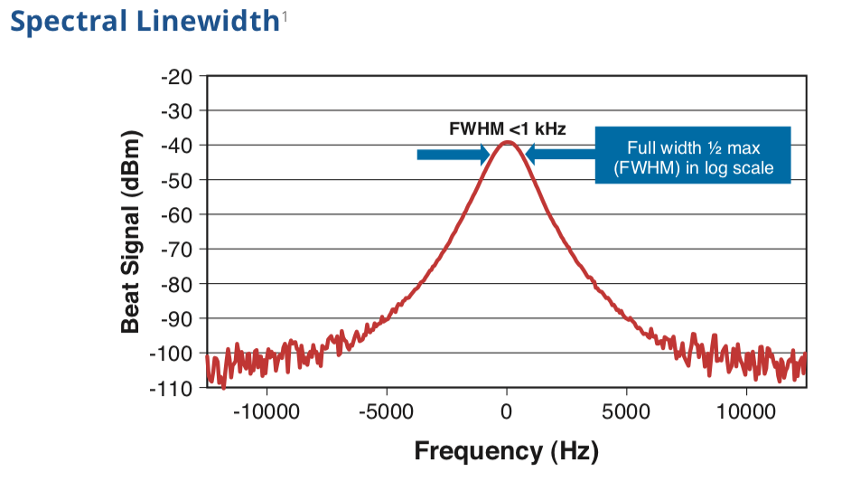
documents/internal_notes/meeting_notes/update_1/Screen Shot 2019-06-17 at 12.55.35 PM.png
