dancvan/AlGaAs_electrooptic_effect/measurements/single_frequency/sio2ta2o5/03_04_2020/displacement_spectra_LVK_null.png

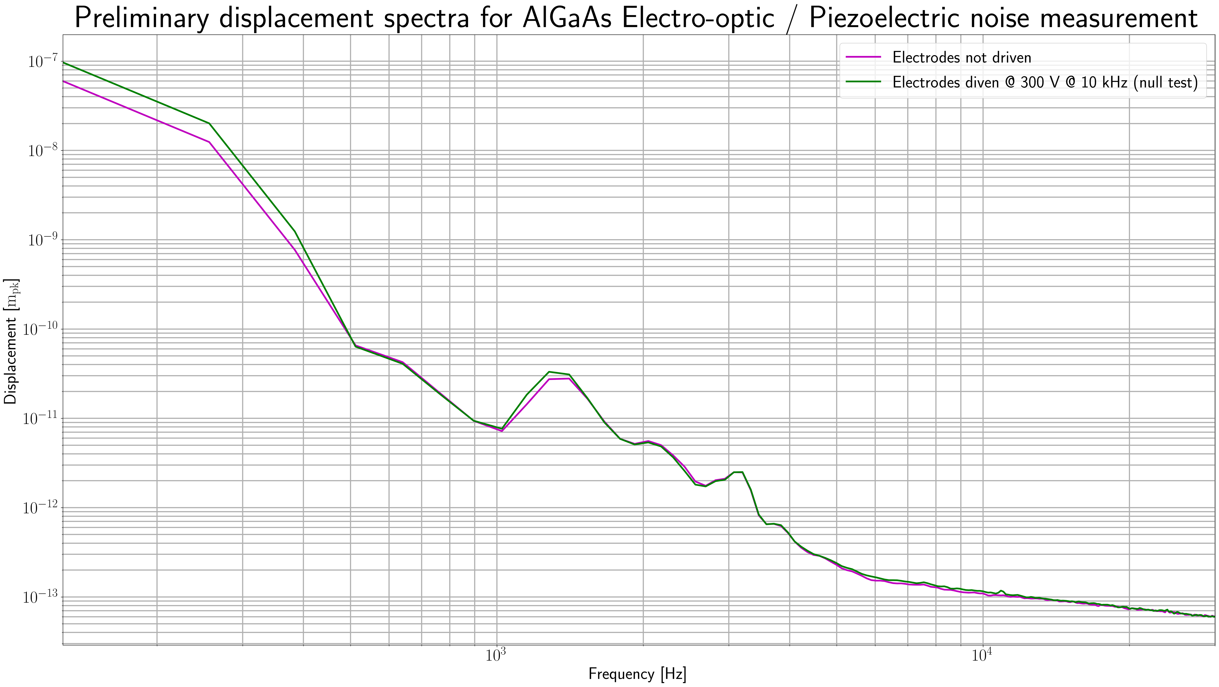
measurements/single_frequency/sio2ta2o5/03_04_2020/displacement_spectra_LVK_null.png
