dancvan/AlGaAs_electrooptic_effect/results/figures/electrodes/split_electrodes_concept.png

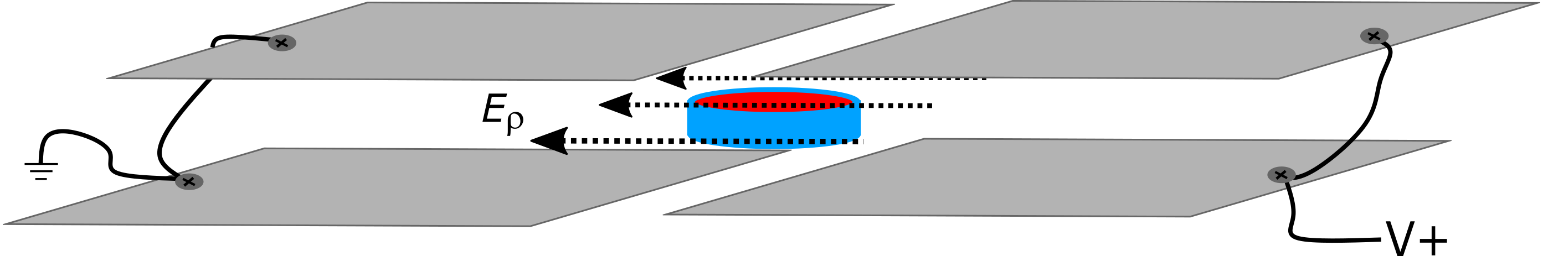
results/figures/electrodes/split_electrodes_concept.png
