dancvan/AlGaAs_electrooptic_effect/results/frequency_comb/03_13_2021b_comb_pk_sio2ta2o5/Hz_spectra_03_13_2021b_comb_pk_sio2ta2o5.png

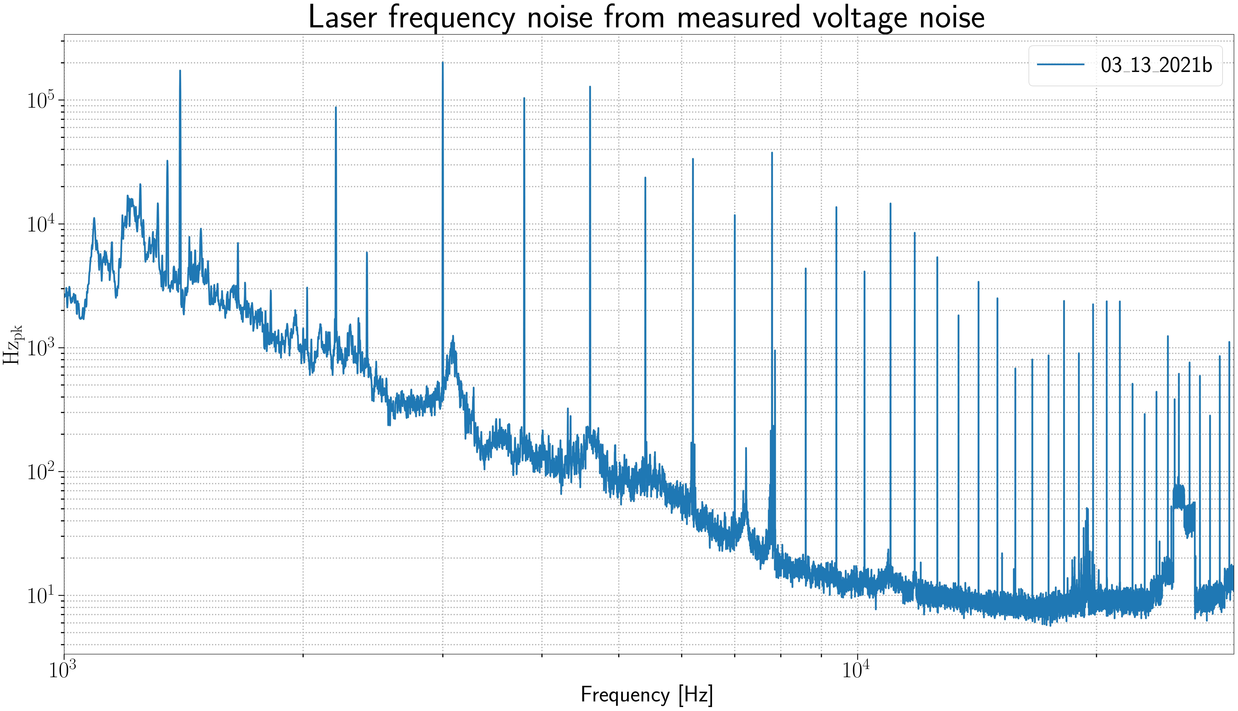
results/frequency_comb/03_13_2021b_comb_pk_sio2ta2o5/Hz_spectra_03_13_2021b_comb_pk_sio2ta2o5.png
