dancvan/AlGaAs_electrooptic_effect/results/frequency_comb/FEB172021freqcomb/Hzpk_spectra_FEB172021freqcomb.png

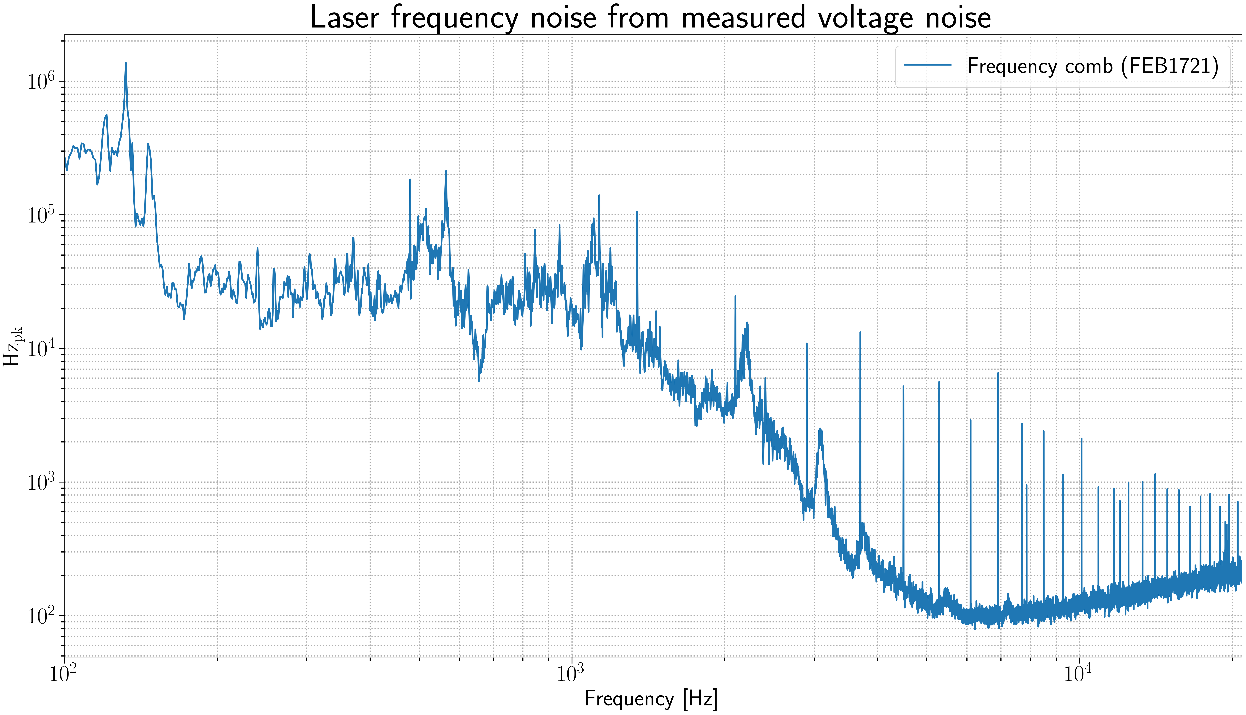
results/frequency_comb/FEB172021freqcomb/Hzpk_spectra_FEB172021freqcomb.png
