dancvan/AlGaAs_electrooptic_effect/results/frequency_comb/FEB172021noise/Hzpk_spectra_FEB172021noise.png

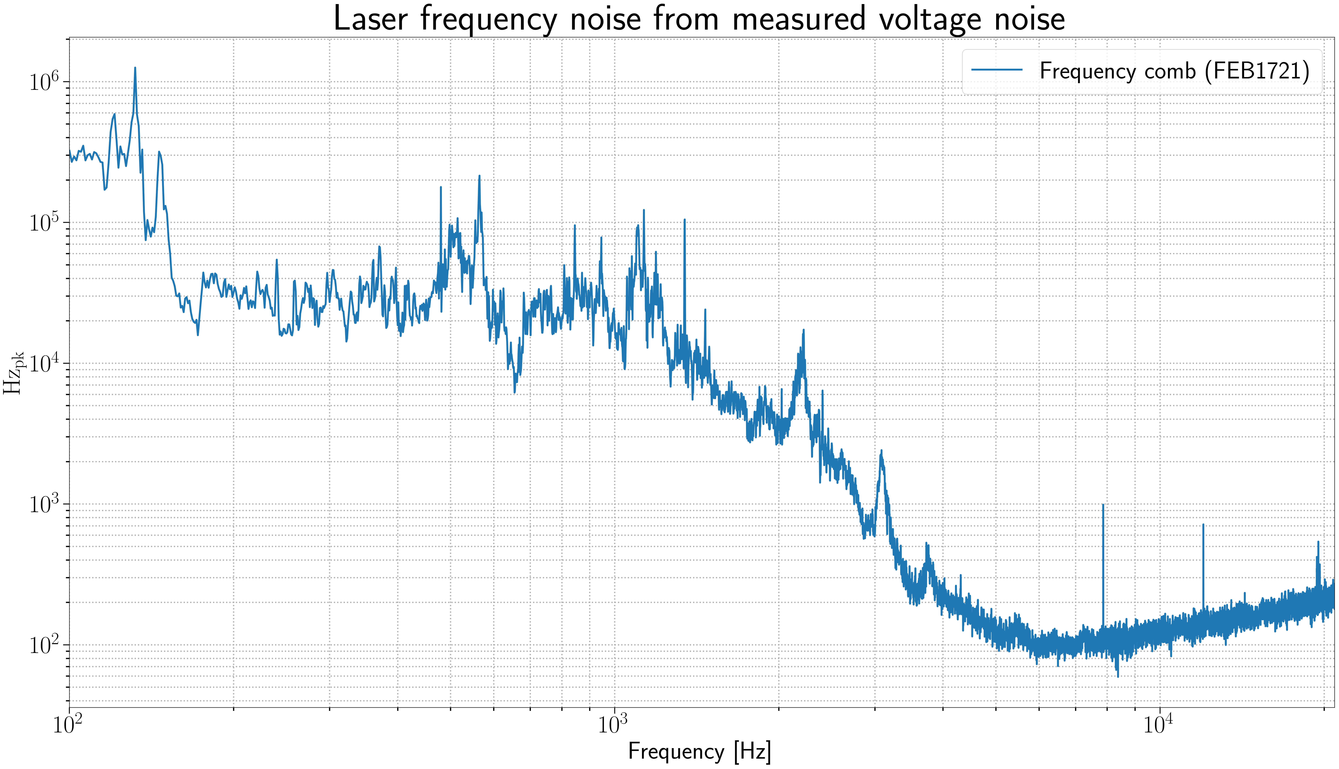
results/frequency_comb/FEB172021noise/Hzpk_spectra_FEB172021noise.png
