dancvan/AlGaAs_electrooptic_effect/results/frequency_comb/FEB172021noise/vpk_spectra_FEB172021noise.png

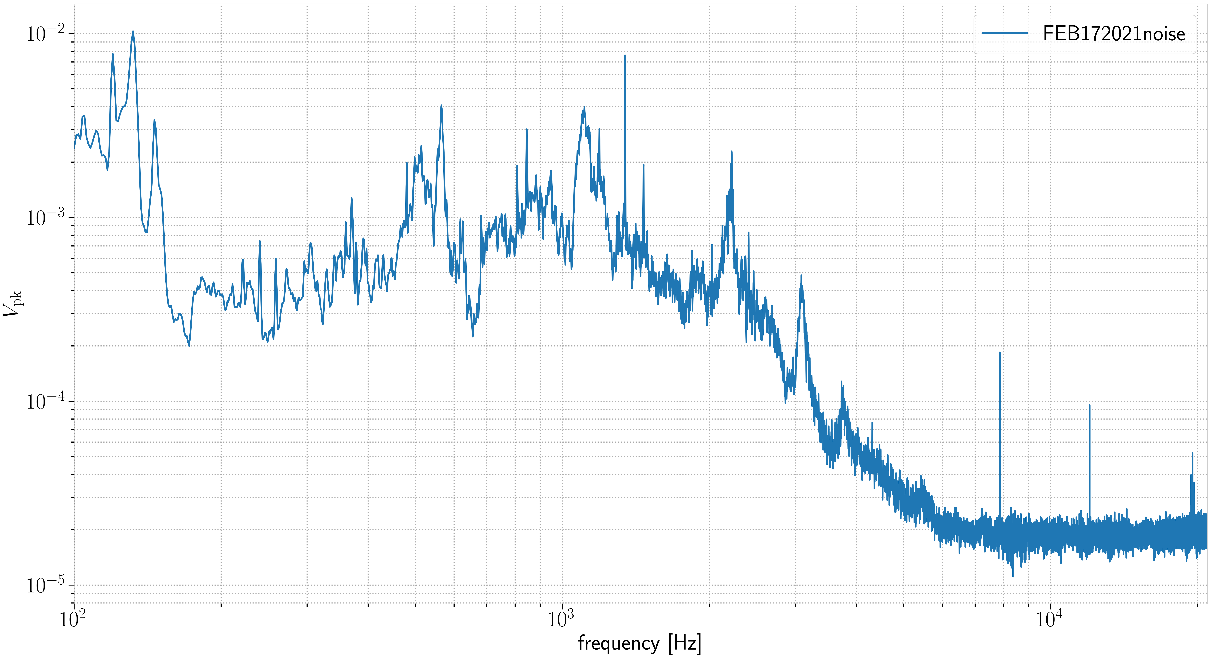
results/frequency_comb/FEB172021noise/vpk_spectra_FEB172021noise.png
