dancvan/AlGaAs_electrooptic_effect/results/noise/03_07_2021_frequency_comb_pk/v_spectra_03_07_2021_frequency_comb_pk.png

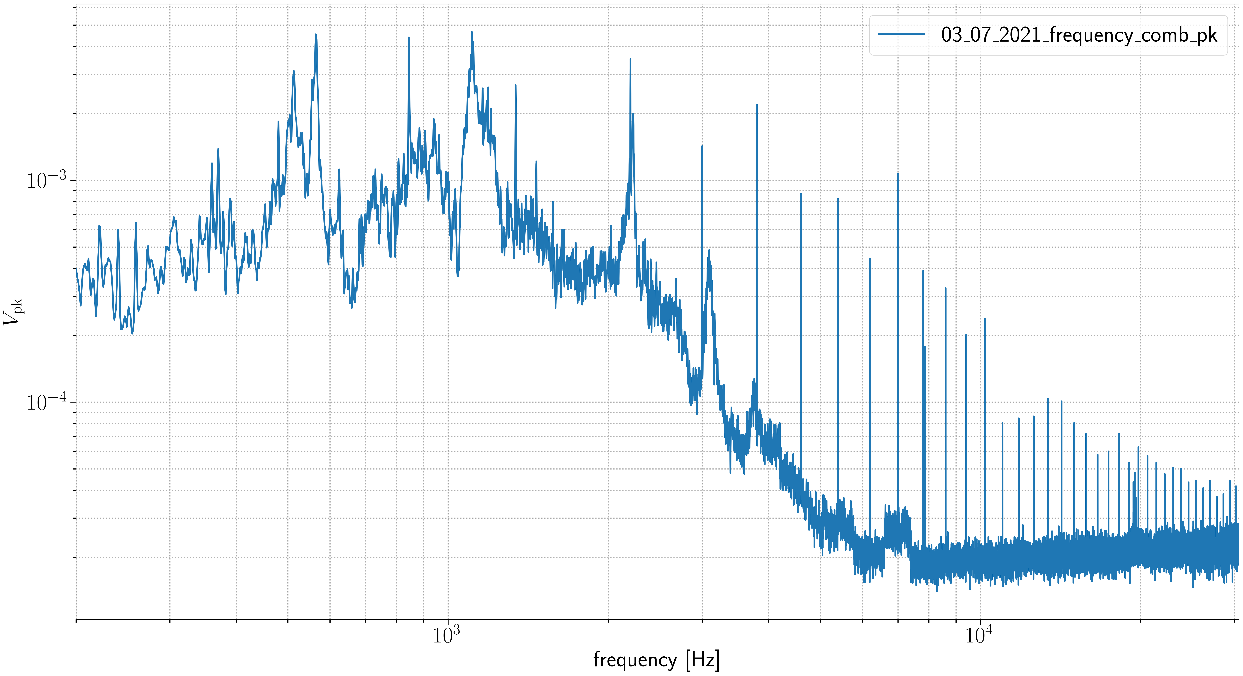
results/noise/03_07_2021_frequency_comb_pk/v_spectra_03_07_2021_frequency_comb_pk.png
