dancvan/AlGaAs_electrooptic_effect/results/noise/03_07_2021_noise_pk/v_spectra_03_07_2021_noise_pk.png

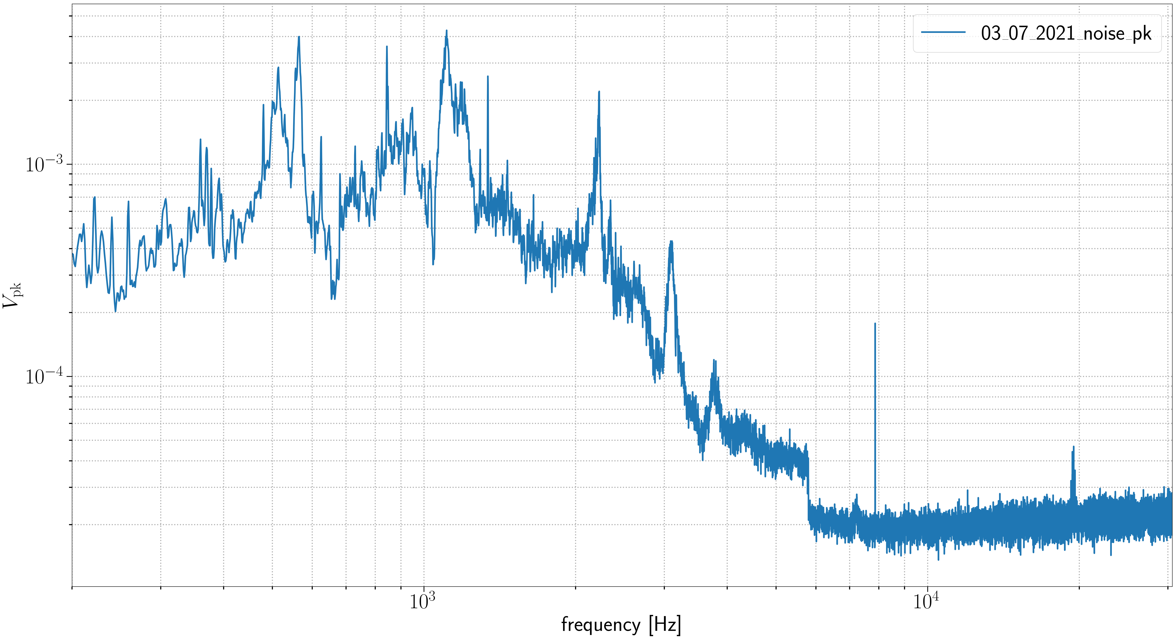
results/noise/03_07_2021_noise_pk/v_spectra_03_07_2021_noise_pk.png
