dancvan/AlGaAs_electrooptic_effect/results/noise/03_13_2021b_noise_pk_sio2ta2o5/Hz_spectra_03_13_2021b_noise_pk_sio2ta2o5.png

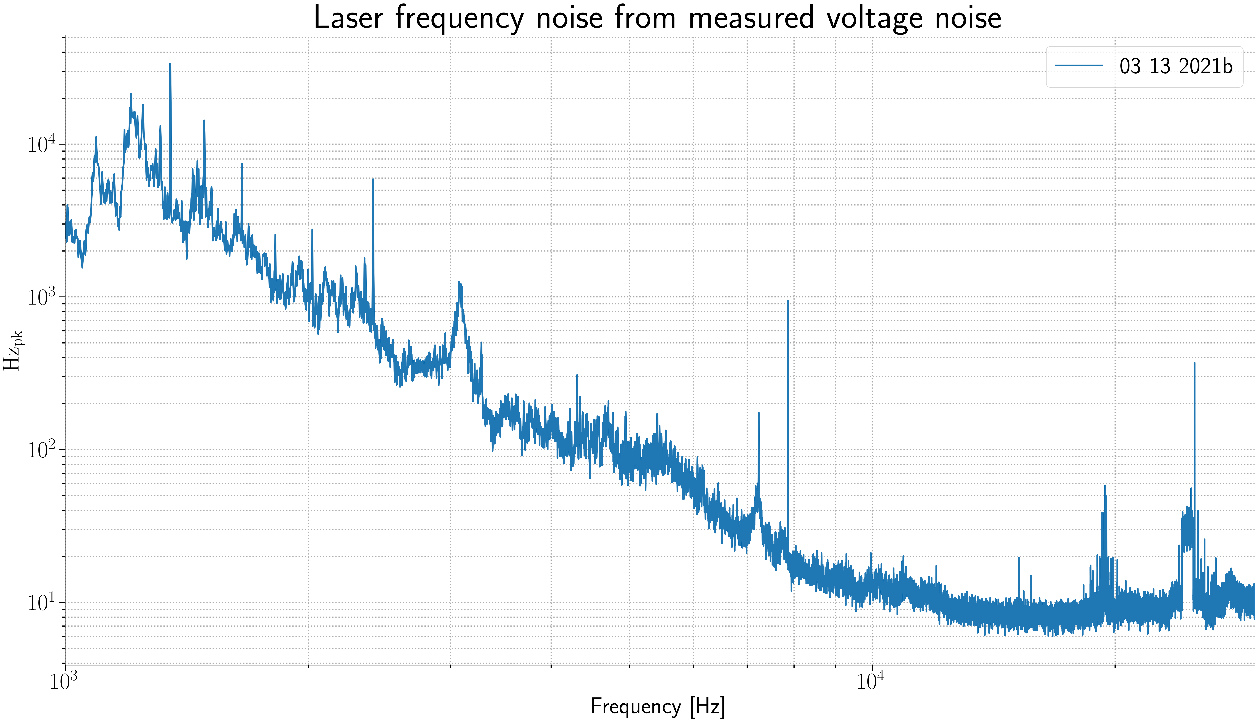
results/noise/03_13_2021b_noise_pk_sio2ta2o5/Hz_spectra_03_13_2021b_noise_pk_sio2ta2o5.png
