dancvan/AlGaAs_electrooptic_effect/results/swept_frequency/02_22_2021_swept_pk/Hz_spectra_02_22_2021_swept_pk.png

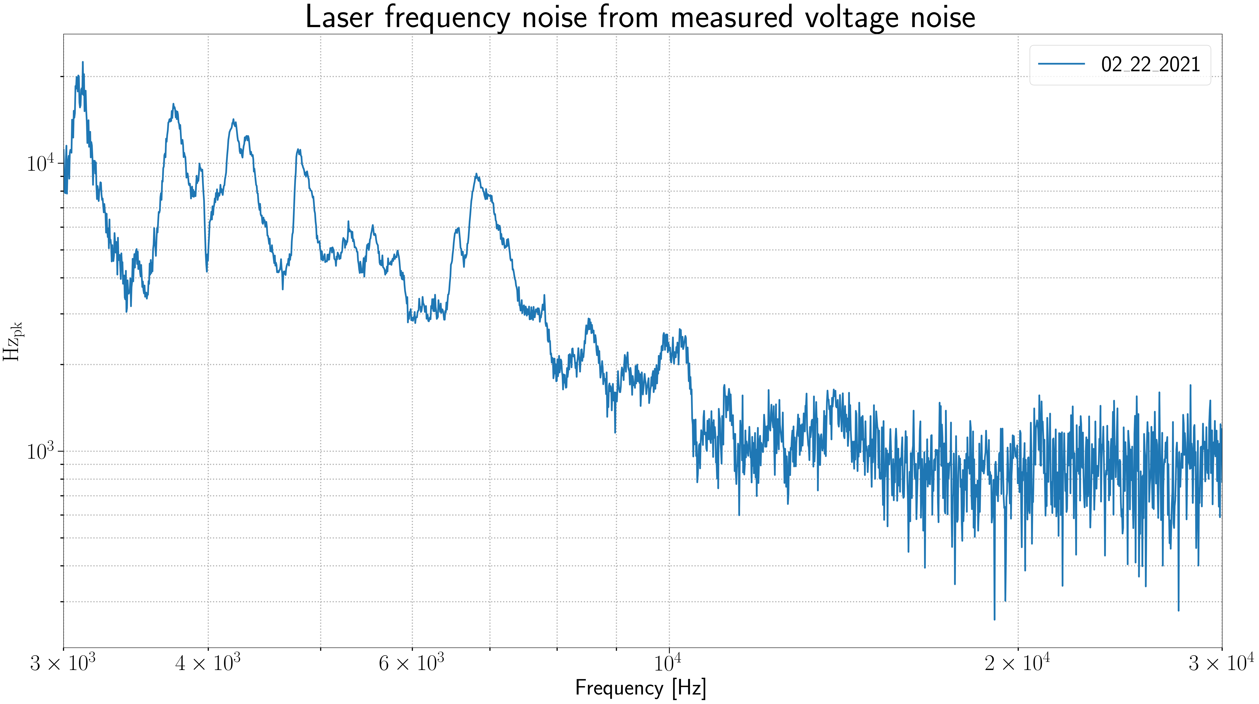
results/swept_frequency/02_22_2021_swept_pk/Hz_spectra_02_22_2021_swept_pk.png
