dancvan/AlGaAs_electrooptic_effect/results/swept_frequency/03_03_2021_comb_pk/v_spectra_03_03_2021_comb_pk.png

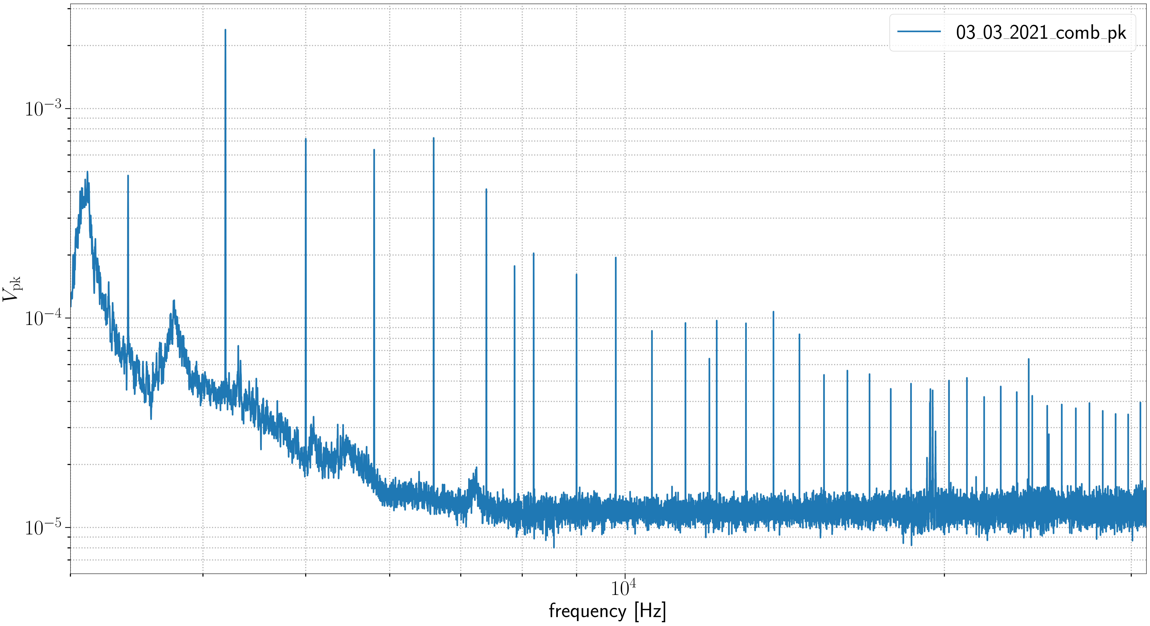
results/swept_frequency/03_03_2021_comb_pk/v_spectra_03_03_2021_comb_pk.png
