dancvan/AlGaAs_electrooptic_effect/results/swept_frequency/03_03_2021_noise_pk/v_spectra_03_03_2021_noise_pk.png

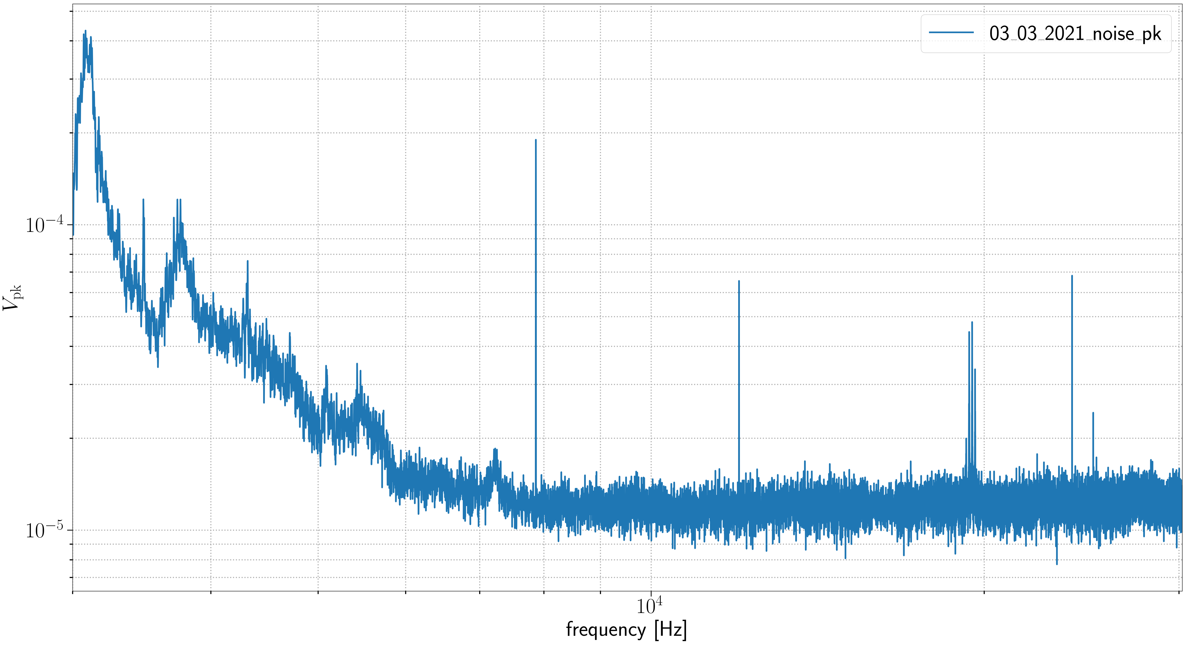
results/swept_frequency/03_03_2021_noise_pk/v_spectra_03_03_2021_noise_pk.png
