dancvan/AlGaAs_electrooptic_effect/measurements/FSS_tfs/spice/imported_components/Draft4_AD602drive15.png

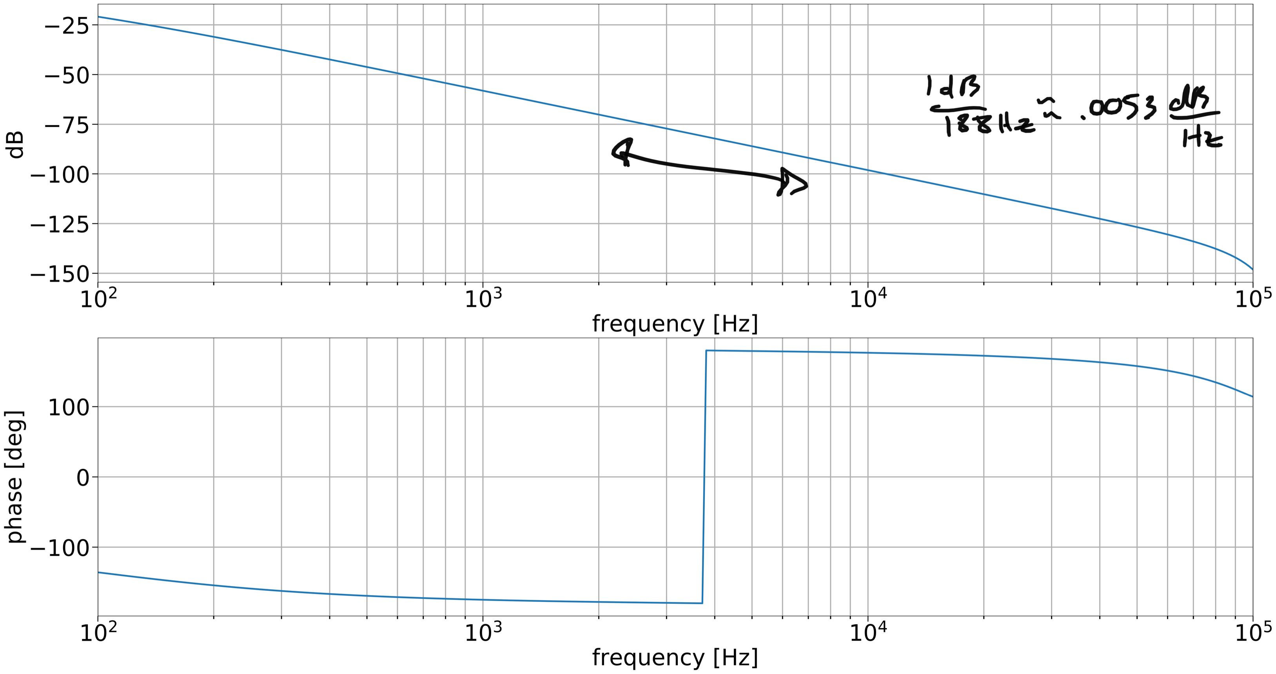
measurements/FSS_tfs/spice/imported_components/Draft4_AD602drive15.png
