dancvan/AlGaAs_electrooptic_effect/measurements/FSS_tfs/spice/imported_components/Draft4_AD602drive640m.png

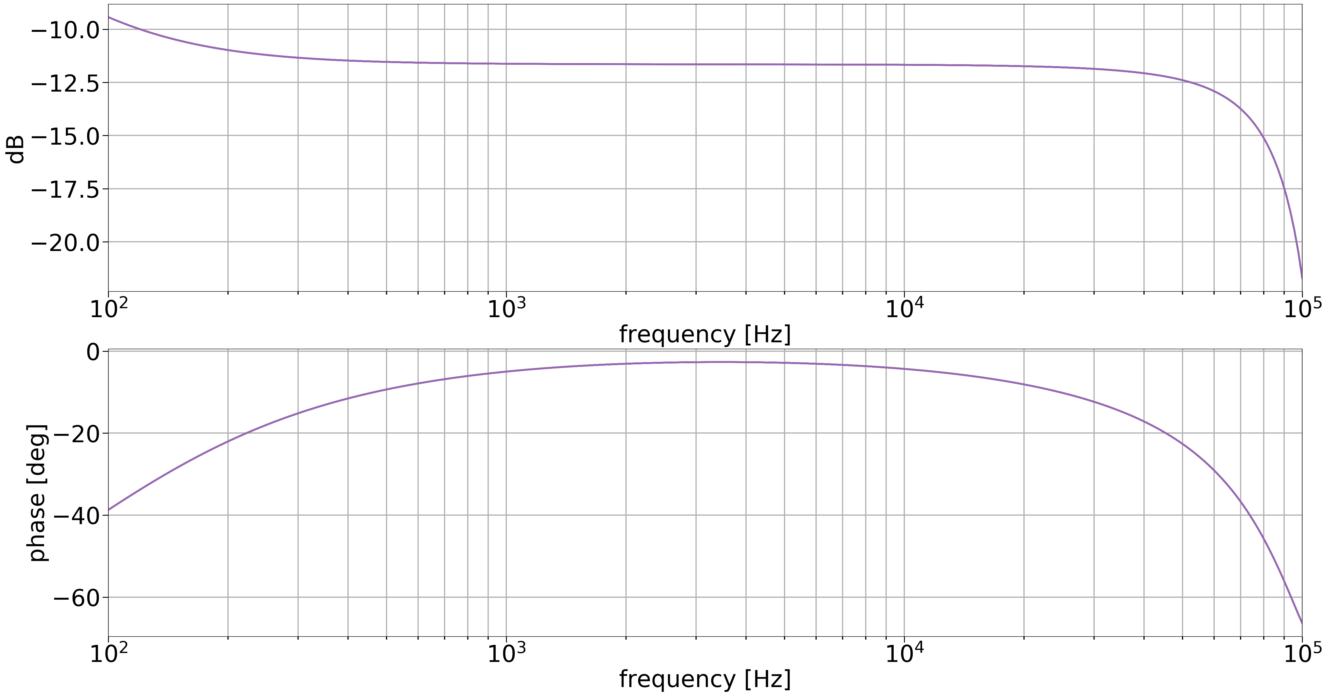
measurements/FSS_tfs/spice/imported_components/Draft4_AD602drive640m.png
