dancvan/AlGaAs_electrooptic_effect/results/updates/12_08_2020/3d_printed_mount_with_machined stabilizers.png

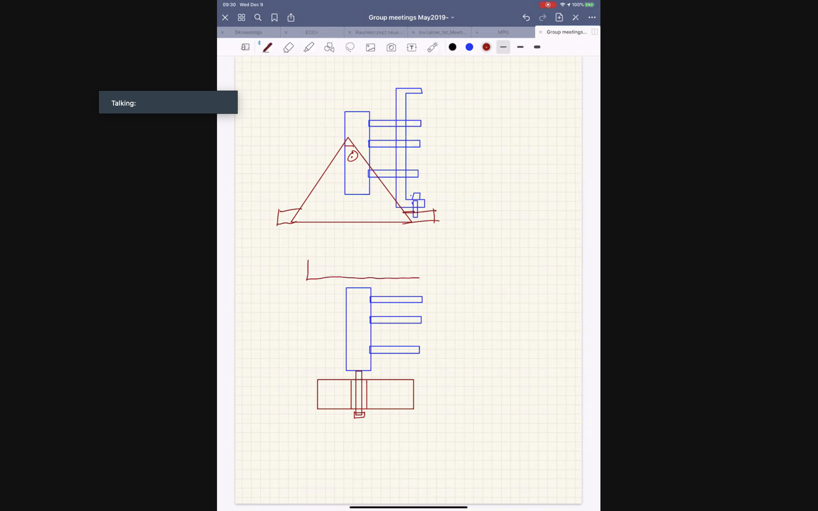
results/updates/12_08_2020/3d_printed_mount_with_machined stabilizers.png
