dancvan/AlGaAs_electrooptic_effect/measurements/laser_pzt_sweep/03_23_2021/w_set_screws/TEK00000.CSV

TIME | CH1 | CH2
-1.3480e-01 | 0.386 | -0.2
-1.3478e-01 | 0.386 | -0.202
-1.3476e-01 | 0.382 | -0.202
-1.3474e-01 | 0.388 | -0.2
-1.3472e-01 | 0.388 | -0.204
-1.3470e-01 | 0.386 | -0.204
-1.3468e-01 | 0.384 | -0.202
-1.3466e-01 | 0.388 | -0.2
-1.3464e-01 | 0.39 | -0.198
-1.3462e-01 | 0.384 | -0.204
-1.3460e-01 | 0.384 | -0.21
-1.3458e-01 | 0.386 | -0.202
-1.3456e-01 | 0.388 | -0.204
-1.3454e-01 | 0.384 | -0.204
-1.3452e-01 | 0.388 | -0.2
-1.3450e-01 | 0.392 | -0.208
-1.3448e-01 | 0.384 | -0.21
-1.3446e-01 | 0.388 | -0.206
-1.3444e-01 | 0.386 | -0.204
-1.3442e-01 | 0.384 | -0.204
-1.3440e-01 | 0.382 | -0.204
-1.3438e-01 | 0.386 | -0.208
-1.3436e-01 | 0.392 | -0.2
-1.3434e-01 | 0.386 | -0.208
-1.3432e-01 | 0.386 | -0.2
-1.3430e-01 | 0.384 | -0.208
-1.3428e-01 | 0.388 | -0.204
-1.3426e-01 | 0.382 | -0.202
-1.3424e-01 | 0.386 | -0.204
-1.3422e-01 | 0.386 | -0.206
-1.3420e-01 | 0.39 | -0.208
-1.3418e-01 | 0.386 | -0.204
-1.3416e-01 | 0.386 | -0.206
-1.3414e-01 | 0.384 | -0.202
-1.3412e-01 | 0.386 | -0.2
-1.3410e-01 | 0.388 | -0.2
-1.3408e-01 | 0.388 | -0.204
-1.3406e-01 | 0.392 | -0.206
-1.3404e-01 | 0.386 | -0.202
-1.3402e-01 | 0.382 | -0.202
-1.3400e-01 | 0.39 | -0.204
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
