dancvan/AlGaAs_electrooptic_effect/measurements/laser_pzt_sweep/03_23_2021/wo_set_screws/TEK00000.CSV

TIME | CH1 | CH2
-1.2360e-01 | 0.394 | -0.222
-1.2358e-01 | 0.392 | -0.224
-1.2356e-01 | 0.396 | -0.228
-1.2354e-01 | 0.392 | -0.228
-1.2352e-01 | 0.396 | -0.226
-1.2350e-01 | 0.392 | -0.23
-1.2348e-01 | 0.392 | -0.23
-1.2346e-01 | 0.398 | -0.23
-1.2344e-01 | 0.386 | -0.228
-1.2342e-01 | 0.392 | -0.224
-1.2340e-01 | 0.388 | -0.224
-1.2338e-01 | 0.386 | -0.228
-1.2336e-01 | 0.392 | -0.222
-1.2334e-01 | 0.396 | -0.228
-1.2332e-01 | 0.394 | -0.228
-1.2330e-01 | 0.404 | -0.234
-1.2328e-01 | 0.392 | -0.224
-1.2326e-01 | 0.392 | -0.224
-1.2324e-01 | 0.4 | -0.23
-1.2322e-01 | 0.394 | -0.222
-1.2320e-01 | 0.39 | -0.23
-1.2318e-01 | 0.392 | -0.228
-1.2316e-01 | 0.39 | -0.228
-1.2314e-01 | 0.392 | -0.232
-1.2312e-01 | 0.396 | -0.23
-1.2310e-01 | 0.396 | -0.226
-1.2308e-01 | 0.392 | -0.232
-1.2306e-01 | 0.39 | -0.232
-1.2304e-01 | 0.388 | -0.23
-1.2302e-01 | 0.392 | -0.228
-1.2300e-01 | 0.394 | -0.224
-1.2298e-01 | 0.394 | -0.224
-1.2296e-01 | 0.396 | -0.228
-1.2294e-01 | 0.392 | -0.228
-1.2292e-01 | 0.39 | -0.232
-1.2290e-01 | 0.396 | -0.228
-1.2288e-01 | 0.392 | -0.226
-1.2286e-01 | 0.394 | -0.23
-1.2284e-01 | 0.396 | -0.232
-1.2282e-01 | 0.392 | -0.232
-1.2280e-01 | 0.392 | -0.232
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
