dancvan/AlGaAs_electrooptic_effect/measurements/D1002969_transimpedence/259/time_in_259_signal_generator_1MHz.CSV

Record Length | 2.500000e+03 | -0.000006400000 | 0.92000
Sample Interval | 4.000000e-09 | -0.000006396000 | 0.92000
Trigger Point | 1.600000000000e+03 | -0.000006392000 | 0.92000
 |  | -0.000006388000 | 1.00000
 |  | -0.000006384000 | 1.04000
 |  | -0.000006380000 | 1.08000
Source | CH1 | -0.000006376000 | 1.08000
Vertical Units | V | -0.000006372000 | 1.08000
Vertical Scale | 1.000000e+00 | -0.000006368000 | 1.12000
Vertical Offset | 0.000000e+00 | -0.000006364000 | 1.12000
Horizontal Units | s | -0.000006360000 | 1.12000
Horizontal Scale | 1.000000e-06 | -0.000006356000 | 1.16000
Pt Fmt | Y | -0.000006352000 | 1.20000
Yzero | 0.000000e+00 | -0.000006348000 | 1.20000
Probe Atten | 1.000000e+00 | -0.000006344000 | 1.28000
Model Number | TBS1154 | -0.000006340000 | 1.24000
Serial Number | C020573 | -0.000006336000 | 1.24000
Firmware Version | FV:v26.05 | -0.000006332000 | 1.24000
 |  | -00.000006328000 | 1.28000
 |  | -00.000006324000 | 1.32000
 |  | -00.000006320000 | 1.32000
 |  | -00.000006316000 | 1.32000
 |  | -00.000006312000 | 1.32000
 |  | -00.000006308000 | 1.36000
 |  | -00.000006304000 | 1.40000
 |  | -00.000006300000 | 1.36000
 |  | -00.000006296000 | 1.40000
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
