dancvan/AlGaAs_electrooptic_effect/measurements/D1002969_transimpedence/259/time_out_250_signal_generator_1MHz.CSV

Record Length | 2.500000e+03 | -0.000006400000 | -0.00960
Sample Interval | 4.000000e-09 | -0.000006396000 | -0.01040
Trigger Point | 1.600000000000e+03 | -0.000006392000 | -0.00880
 |  | -0.000006388000 | -0.00960
 |  | -0.000006384000 | -0.00960
 |  | -0.000006380000 | -0.00880
Source | CH2 | -0.000006376000 | -0.01040
Vertical Units | V | -0.000006372000 | -0.00800
Vertical Scale | 2.000000e-02 | -0.000006368000 | -0.00960
Vertical Offset | 0.000000e+00 | -0.000006364000 | -0.00960
Horizontal Units | s | -0.000006360000 | -0.00800
Horizontal Scale | 1.000000e-06 | -0.000006356000 | -0.00800
Pt Fmt | Y | -0.000006352000 | -0.00800
Yzero | 0.000000e+00 | -0.000006348000 | -0.00800
Probe Atten | 1.000000e+00 | -0.000006344000 | -0.00720
Model Number | TBS1154 | -0.000006340000 | -0.00720
Serial Number | C020573 | -0.000006336000 | -0.00720
Firmware Version | FV:v26.05 | -0.000006332000 | -0.00640
 |  | -00.000006328000 | -0.00560
 |  | -00.000006324000 | -0.00640
 |  | -00.000006320000 | -0.00560
 |  | -00.000006316000 | -0.00560
 |  | -00.000006312000 | -0.00560
 |  | -00.000006308000 | -0.00640
 |  | -00.000006304000 | -0.00560
 |  | -00.000006300000 | -0.00480
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
