dancvan/AlGaAs_electrooptic_effect/measurements/D1002969_transimpedence/259/time_out_259.CSV

Record Length | 2.500000e+03 | -0.000000025000 | -0.64000
Sample Interval | 2.000000e-11 | -0.000000024980 | -0.60000
Trigger Point | 1.250000000000e+03 | -0.000000024960 | -0.60000
 |  | -0.000000024940 | -0.56000
 |  | -0.000000024920 | -0.56000
 |  | -0.000000024900 | -0.52000
Source | CH2 | -0.000000024880 | -0.52000
Vertical Units | V | -0.000000024860 | -0.48000
Vertical Scale | 1.000000e+00 | -0.000000024840 | -0.44000
Vertical Offset | 0.000000e+00 | -0.000000024820 | -0.44000
Horizontal Units | s | -0.000000024800 | -0.40000
Horizontal Scale | 5.000000e-09 | -0.000000024780 | -0.40000
Pt Fmt | Y | -0.000000024760 | -0.36000
Yzero | 0.000000e+00 | -0.000000024740 | -0.32000
Probe Atten | 1.000000e+01 | -0.000000024720 | -0.32000
Model Number | TBS1154 | -0.000000024700 | -0.28000
Serial Number | C020573 | -0.000000024680 | -0.24000
Firmware Version | FV:v26.05 | -0.000000024660 | -0.24000
 |  | -00.000000024640 | -0.20000
 |  | -00.000000024620 | -0.20000
 |  | -00.000000024600 | -0.16000
 |  | -00.000000024580 | -0.12000
 |  | -00.000000024560 | -0.12000
 |  | -00.000000024540 | -0.08000
 |  | -00.000000024520 | -0.04000
 |  | -00.000000024500 | -0.04000
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
