dancvan/AlGaAs_electrooptic_effect/measurements/laser_pzt_sweep/10_27_2020/REFL_full_FSR.CSV

-3.7200e-02 | 0.54
-3.7190e-02 | 0.54
-3.7180e-02 | 0.54
-3.7170e-02 | 0.54
-3.7160e-02 | 0.54
-3.7150e-02 | 0.54
-3.7140e-02 | 0.55
-3.7130e-02 | 0.54
-3.7120e-02 | 0.57
-3.7110e-02 | 0.54
-3.7100e-02 | 0.52
-3.7090e-02 | 0.55
-3.7080e-02 | 0.52
-3.7070e-02 | 0.54
-3.7060e-02 | 0.54
-3.7050e-02 | 0.54
-3.7040e-02 | 0.51
-3.7030e-02 | 0.56
-3.7020e-02 | 0.54
-3.7010e-02 | 0.54
-3.7000e-02 | 0.54
-3.6990e-02 | 0.55
-3.6980e-02 | 0.56
-3.6970e-02 | 0.52
-3.6960e-02 | 0.54
-3.6950e-02 | 0.55
-3.6940e-02 | 0.55
-3.6930e-02 | 0.54
-3.6920e-02 | 0.54
-3.6910e-02 | 0.54
-3.6900e-02 | 0.56
-3.6890e-02 | 0.55
-3.6880e-02 | 0.55
-3.6870e-02 | 0.54
-3.6860e-02 | 0.54
-3.6850e-02 | 0.55
-3.6840e-02 | 0.54
-3.6830e-02 | 0.53
-3.6820e-02 | 0.54
-3.6810e-02 | 0.55
-3.6800e-02 | 0.54
-3.6790e-02 | 0.55
-3.6780e-02 | 0.56
-3.6770e-02 | 0.53
-3.6760e-02 | 0.54
-3.6750e-02 | 0.54
-3.6740e-02 | 0.55
-3.6730e-02 | 0.54
-3.6720e-02 | 0.54
-3.6710e-02 | 0.54
-3.6700e-02 | 0.54
-3.6690e-02 | 0.54
-3.6680e-02 | 0.54
-3.6670e-02 | 0.56
-3.6660e-02 | 0.54
-3.6650e-02 | 0.54
-3.6640e-02 | 0.54
-3.6630e-02 | 0.54
-3.6620e-02 | 0.54
-3.6610e-02 | 0.56
-3.6600e-02 | 0.54
-3.6590e-02 | 0.54
-3.6580e-02 | 0.53
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
