dancvan/AlGaAs_electrooptic_effect/code/fea_electrodes/hole_size_tests_results/Injection_field_estimate.png

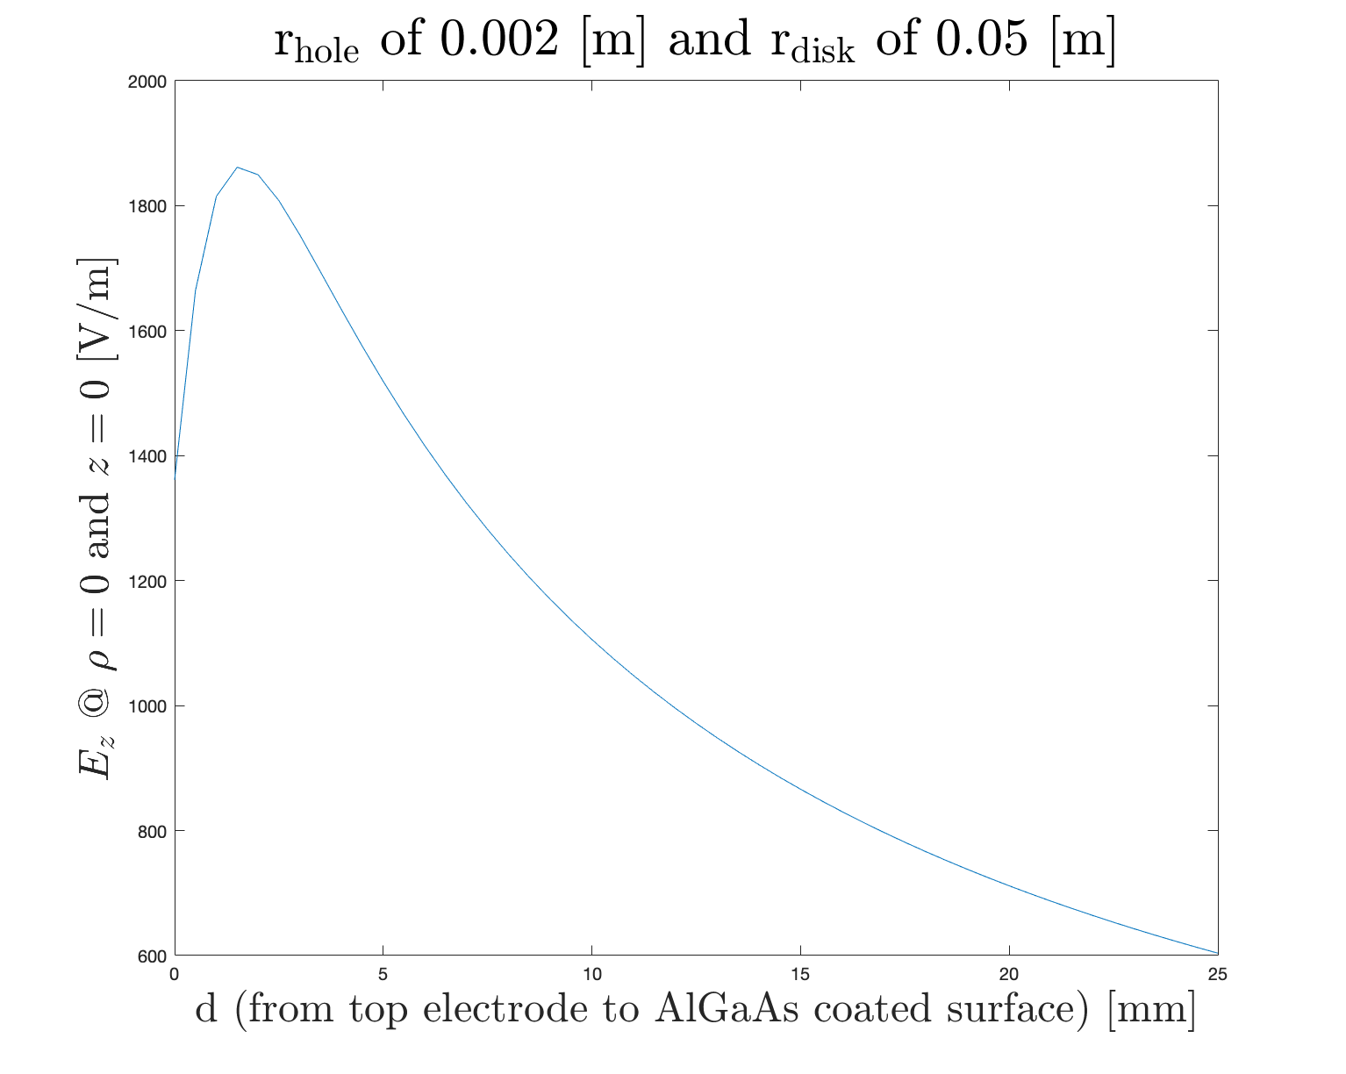
code/fea_electrodes/hole_size_tests_results/Injection_field_estimate.png
