dancvan/AlGaAs_electrooptic_effect/code/fea_electrodes/matlab_script_stefan/poisson/optics_call_results/Screen Shot 2020-05-04 at 7.12.04 PM.png

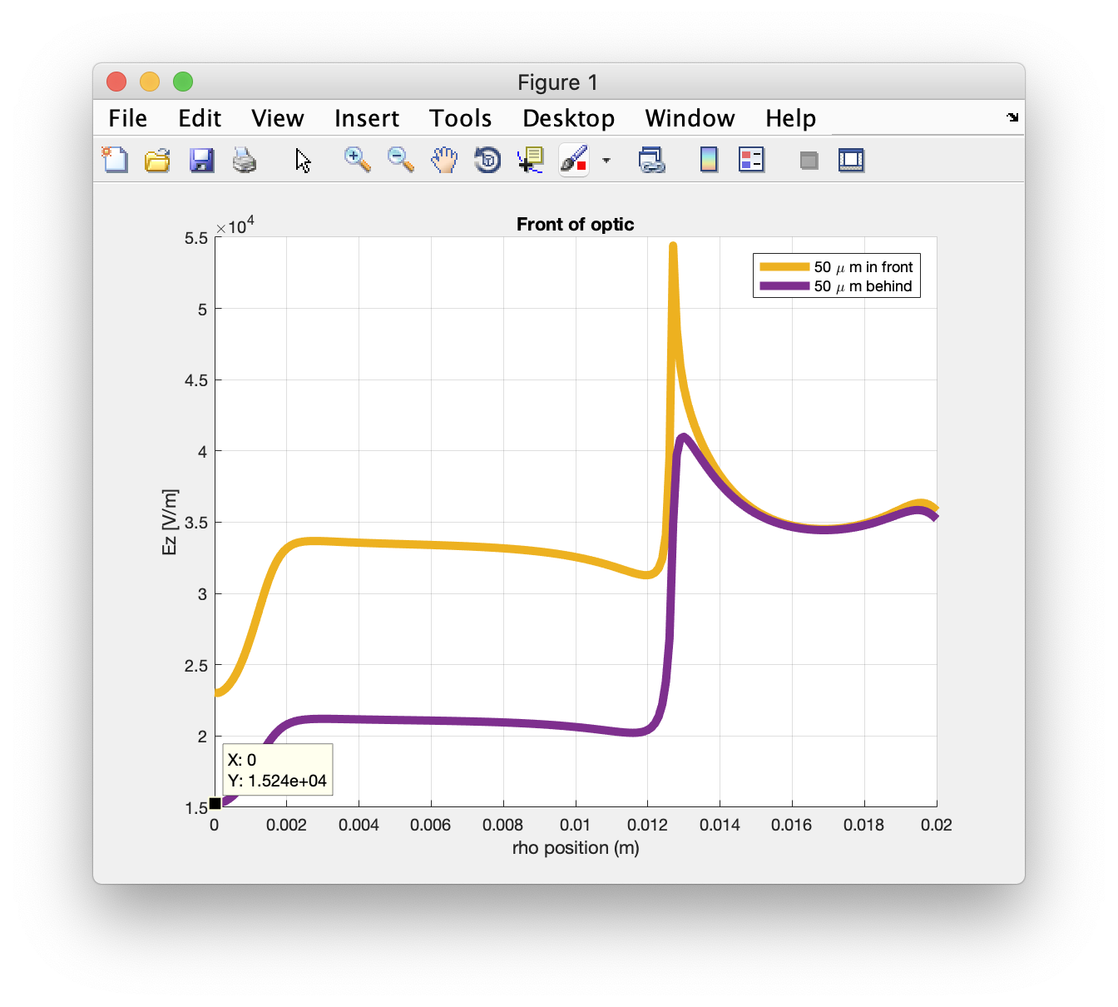
code/fea_electrodes/matlab_script_stefan/poisson/optics_call_results/Screen Shot 2020-05-04 at 7.12.04 PM.png
