dancvan/AlGaAs_electrooptic_effect/code/fea_electrodes/matlab_script_stefan/poisson/results_04_07_2020/E_z.png

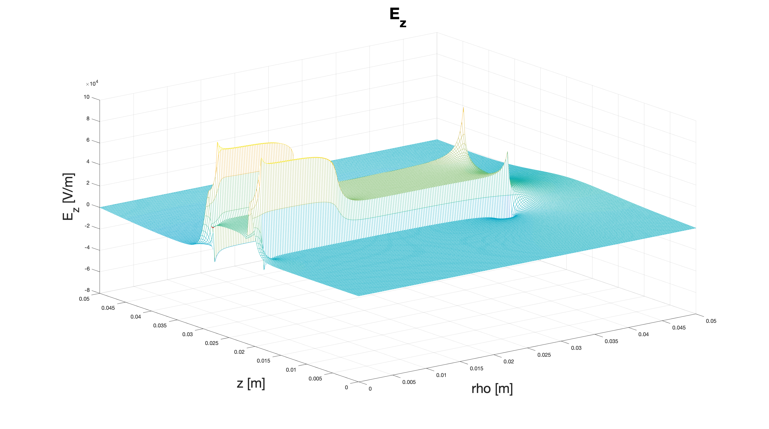
code/fea_electrodes/matlab_script_stefan/poisson/results_04_07_2020/E_z.png
