dancvan/AlGaAs_electrooptic_effect/code/notebooks/pockels_calibration/results/08_13_2021_swept_pk_meas1_algaas/Displacement spectra for AlGaAs Pockels effect measurement.png

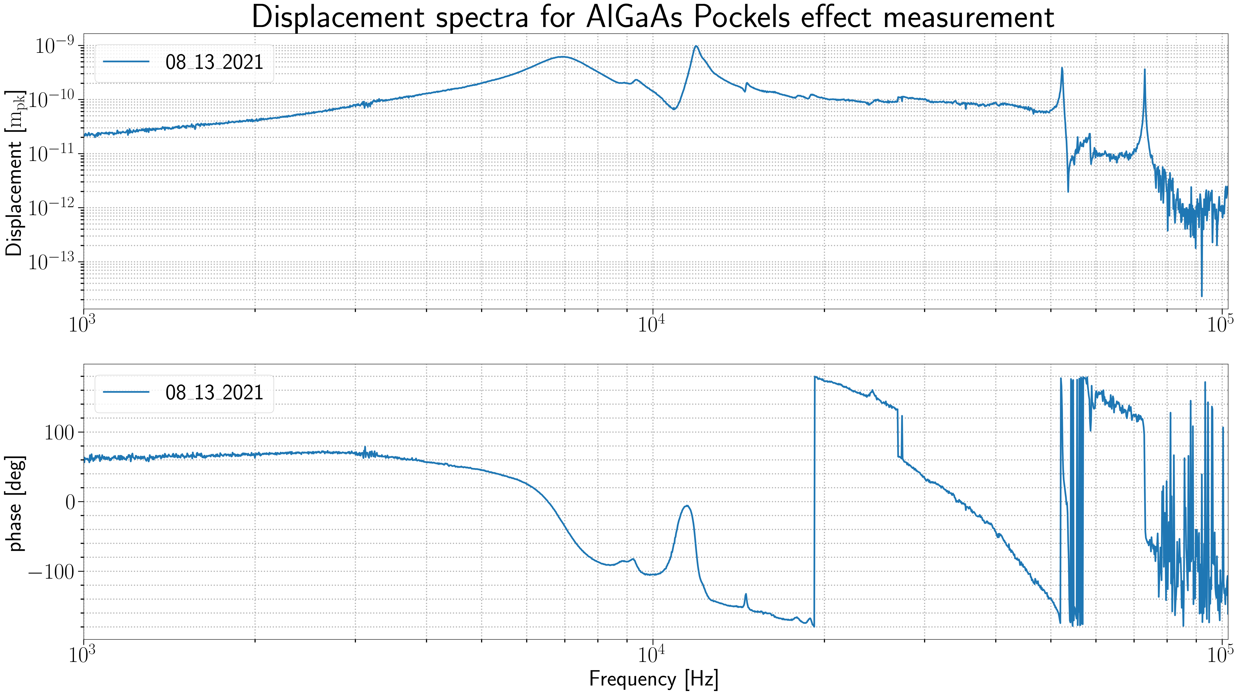
code/notebooks/pockels_calibration/results/08_13_2021_swept_pk_meas1_algaas/Displacement spectra for AlGaAs Pockels effect measurement.png
