dancvan/AlGaAs_electrooptic_effect/documents/internal_notes/elogs/815/815_20201021034627_tp14modelvmeasured.png

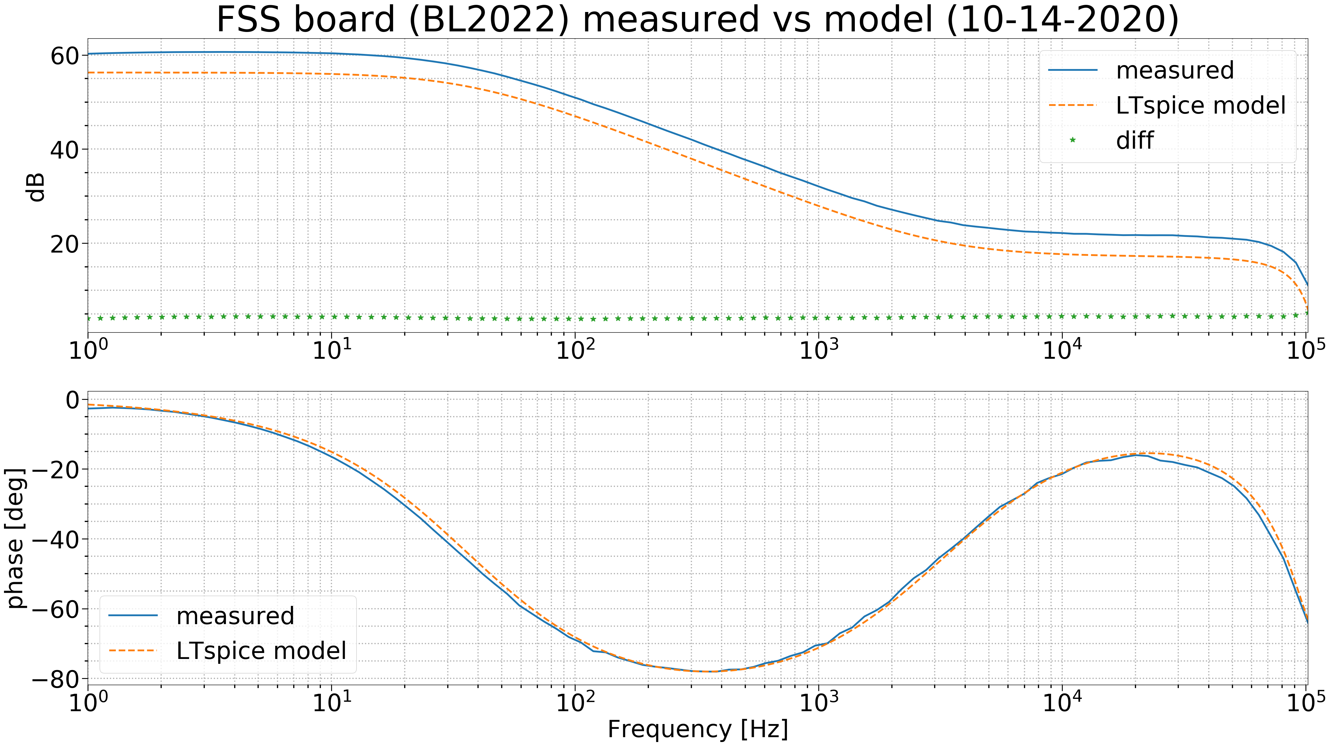
documents/internal_notes/elogs/815/815_20201021034627_tp14modelvmeasured.png
