dancvan/AlGaAs_electrooptic_effect/measurements/beam_scans/01_12_2021/01_12_2021_results.png

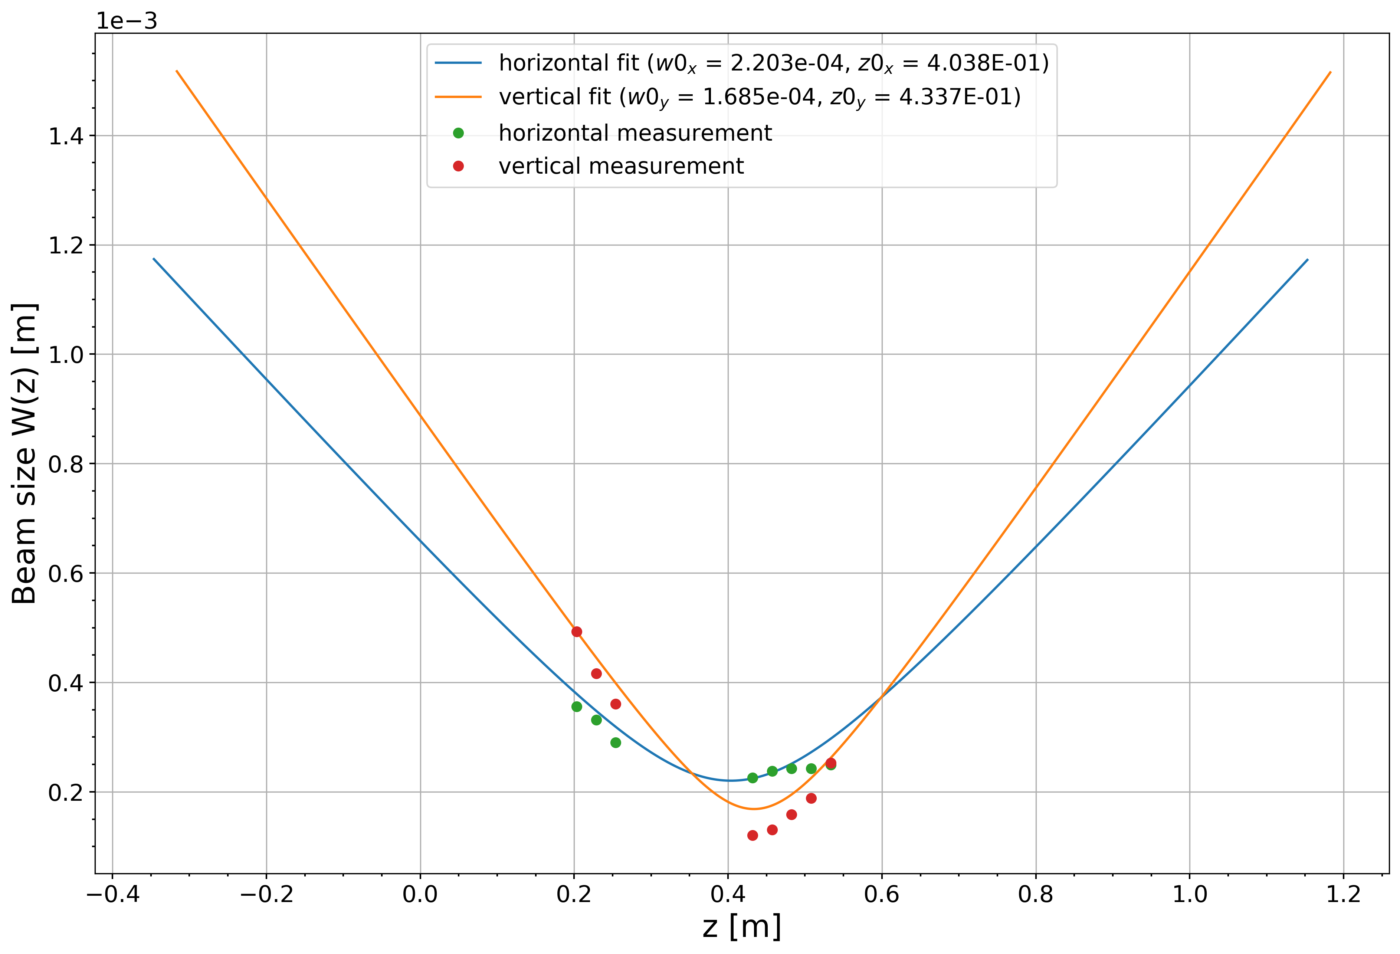
measurements/beam_scans/01_12_2021/01_12_2021_results.png
