dancvan/AlGaAs_electrooptic_effect/measurements/beam_scans/10_16_2019/BS_10_16_2019_results.png

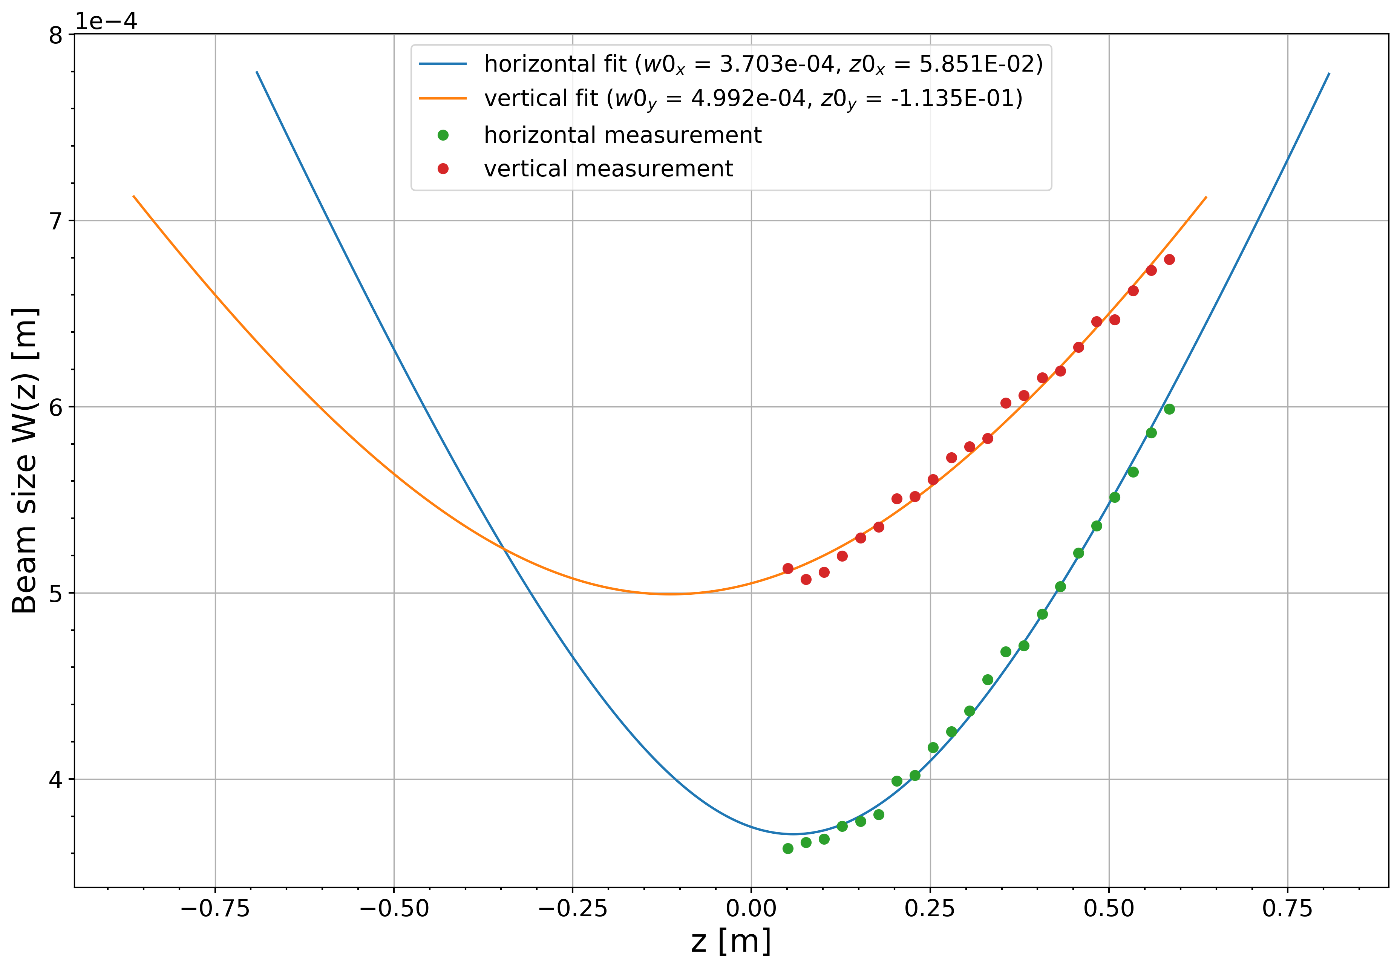
measurements/beam_scans/10_16_2019/BS_10_16_2019_results.png
