dancvan/AlGaAs_electrooptic_effect/measurements/beam_scans/10_24_2019/BS_10_24_2019_results.png

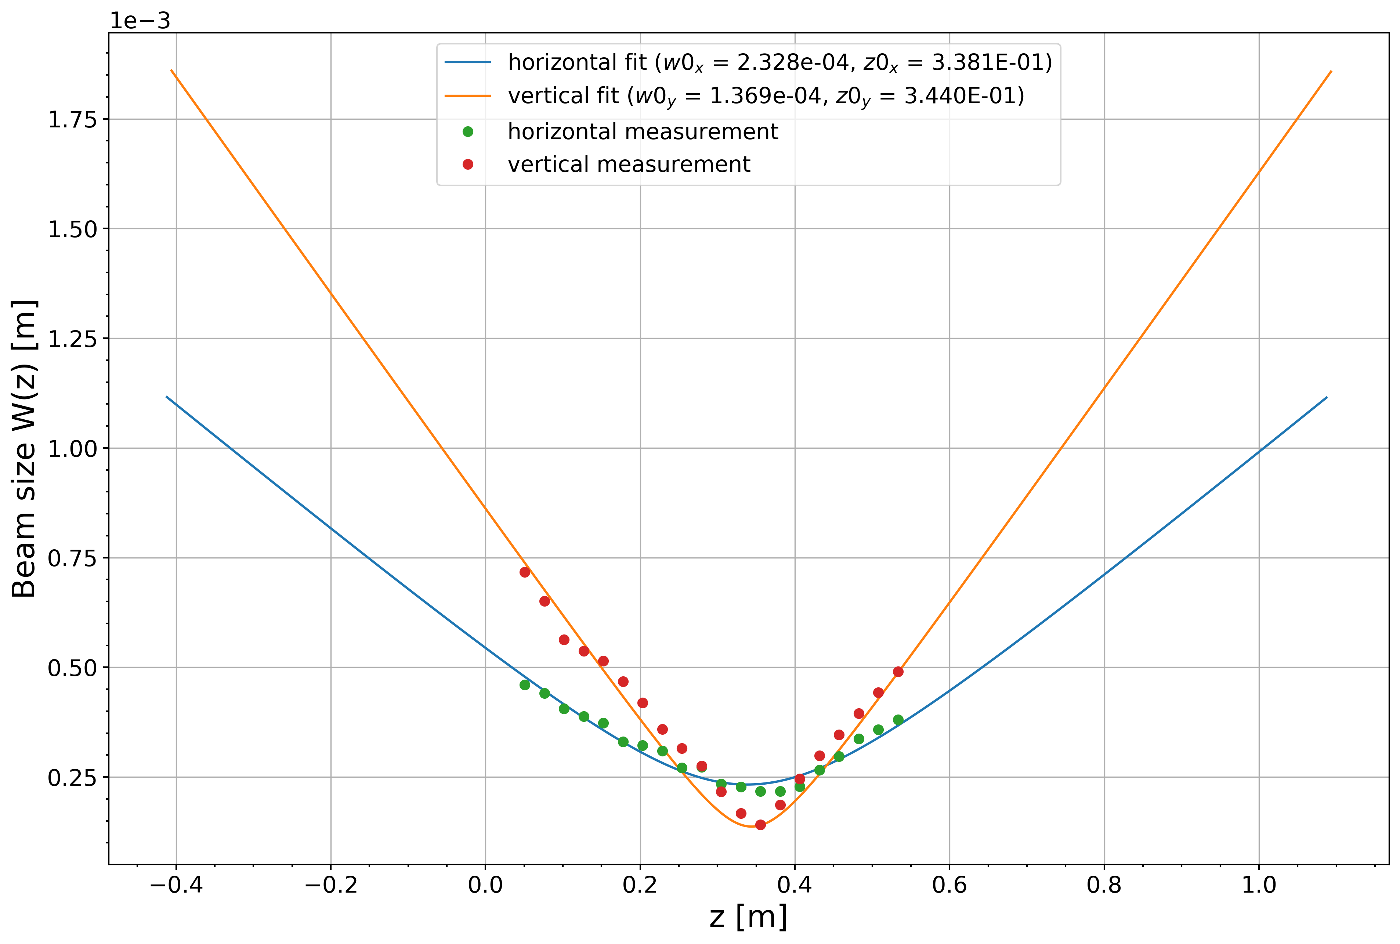
measurements/beam_scans/10_24_2019/BS_10_24_2019_results.png
