dancvan/AlGaAs_electrooptic_effect/measurements/beam_scans/12_18_2020/12_18_2020_results.png

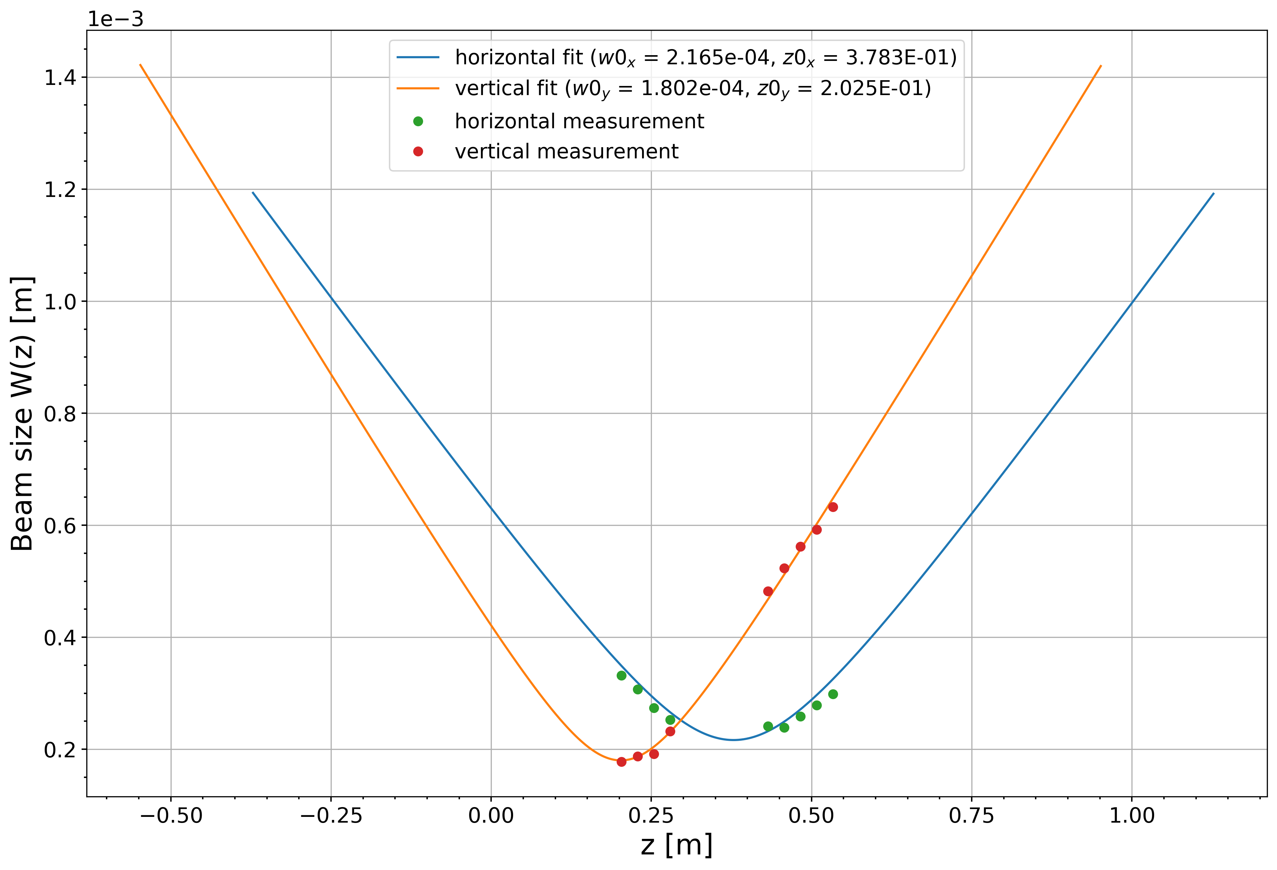
measurements/beam_scans/12_18_2020/12_18_2020_results.png
