dancvan/AlGaAs_electrooptic_effect/measurements/cavity_scan/12_05_2019/FSR_12_05_2019_results.png

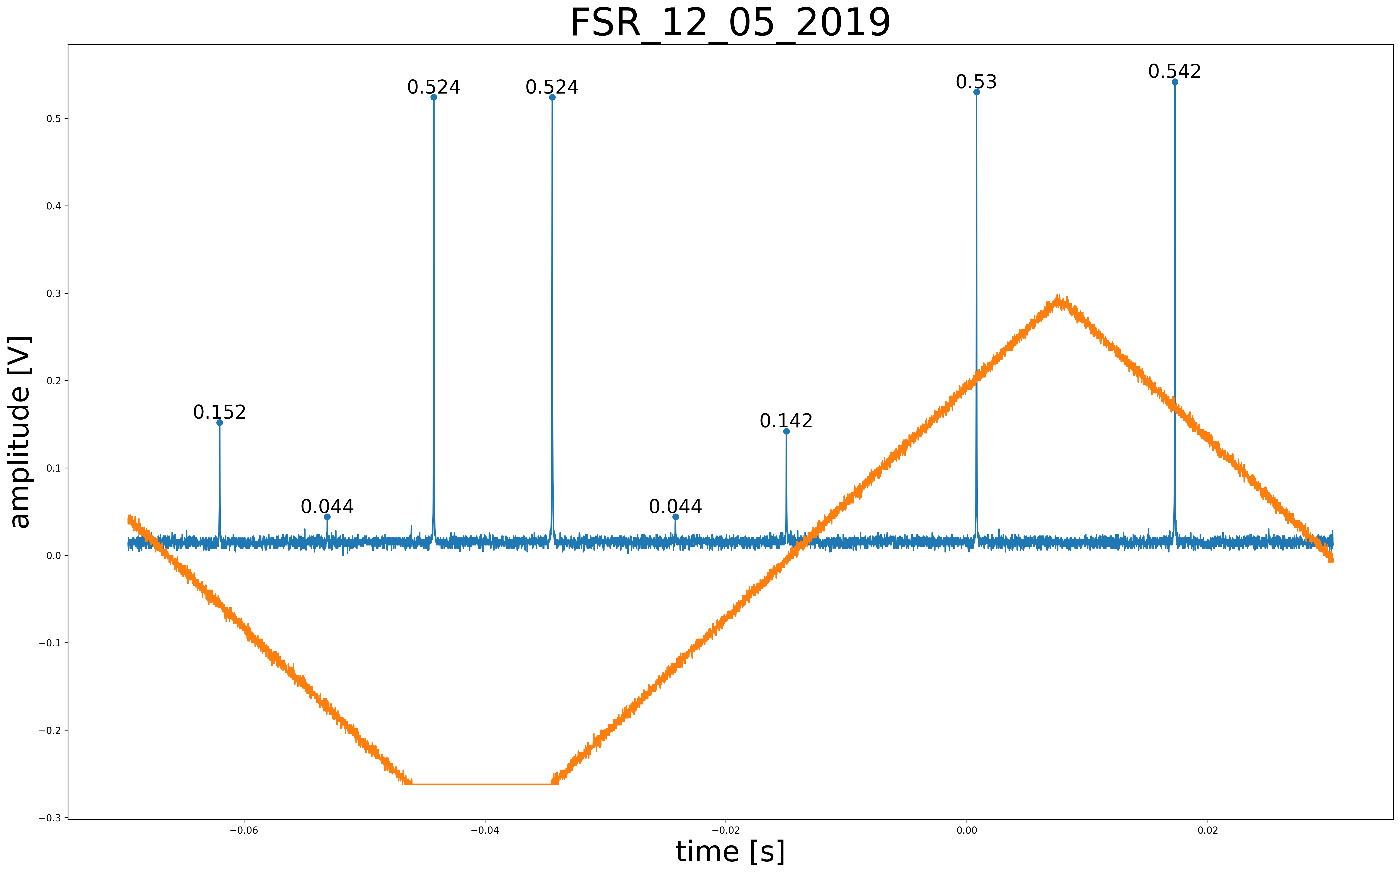
measurements/cavity_scan/12_05_2019/FSR_12_05_2019_results.png
