dancvan/AlGaAs_electrooptic_effect/measurements/D1002969_transimpedence/RF_transimpedence.png

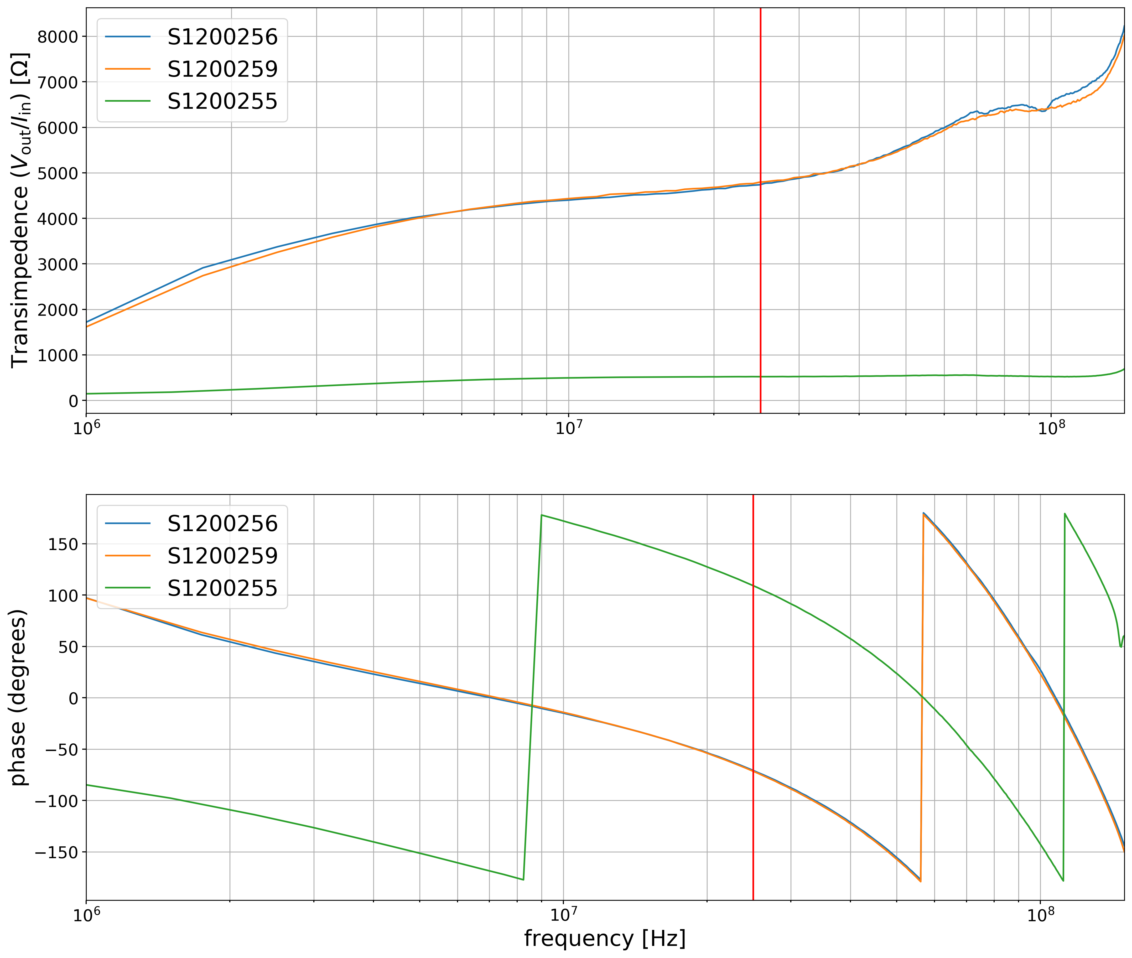
measurements/D1002969_transimpedence/RF_transimpedence.png
