dancvan/AlGaAs_electrooptic_effect/measurements/electrode_capacitence/disk/03_11_2020/HVA_SVR.png

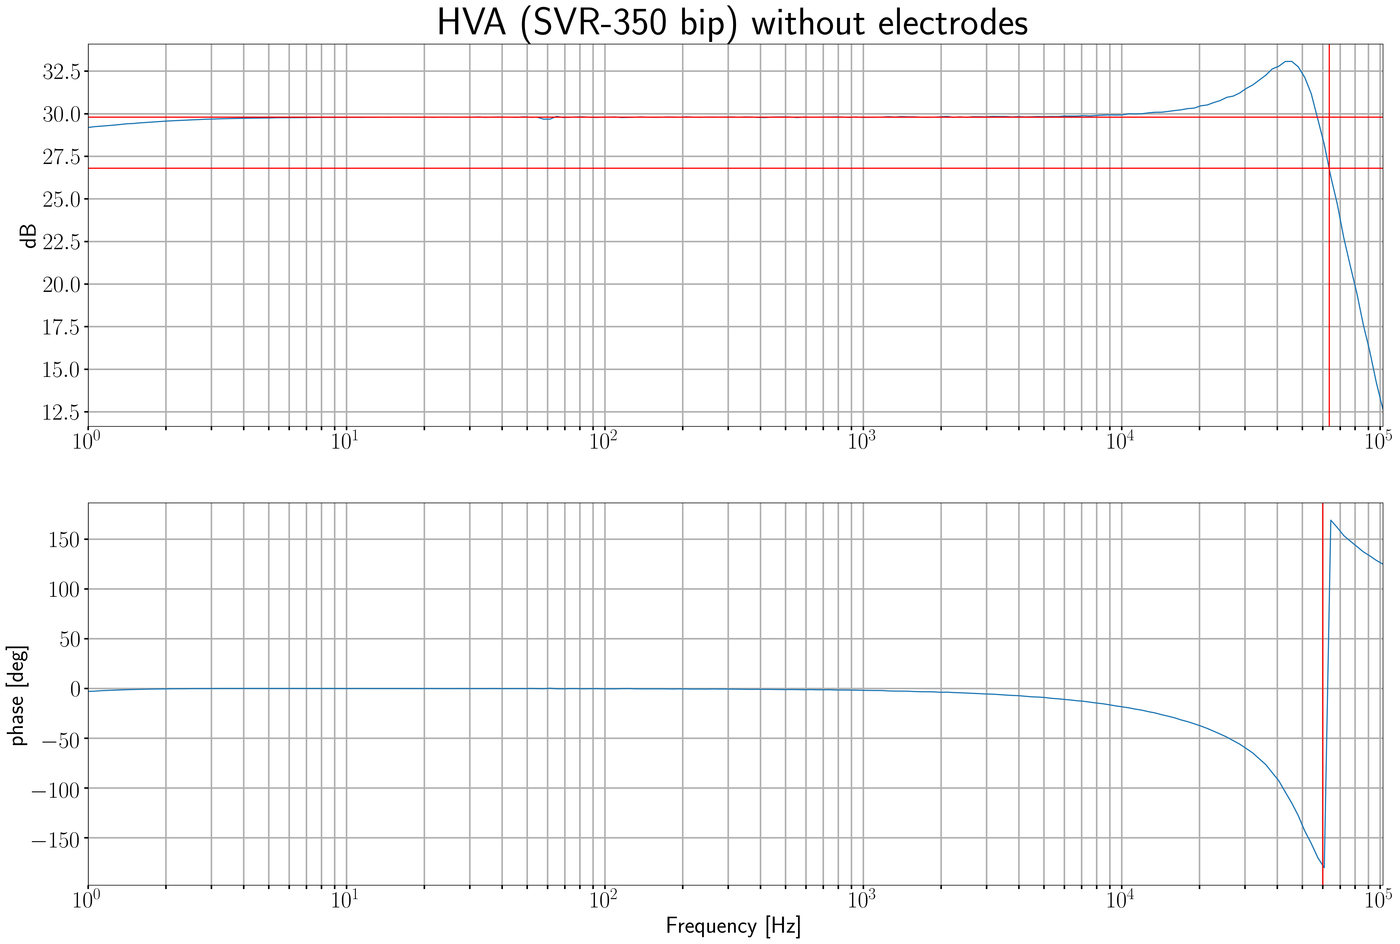
measurements/electrode_capacitence/disk/03_11_2020/HVA_SVR.png
