dancvan/AlGaAs_electrooptic_effect/measurements/electrode_capacitence/disk/03_11_2020/LPF_electrodes.png

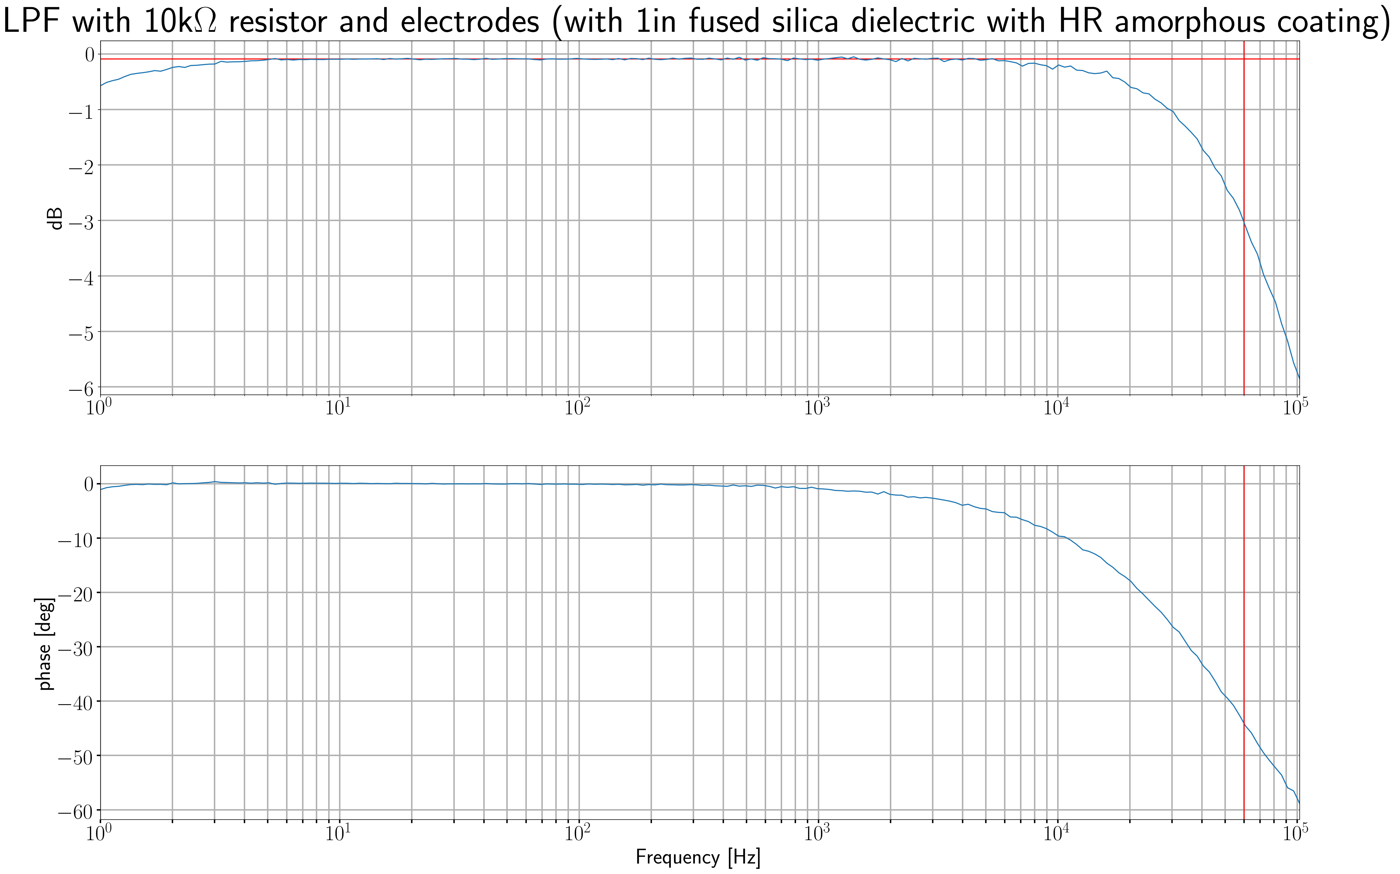
measurements/electrode_capacitence/disk/03_11_2020/LPF_electrodes.png
