dancvan/AlGaAs_electrooptic_effect/measurements/FSS_tfs/05_31_2020/exc1V/plot.png

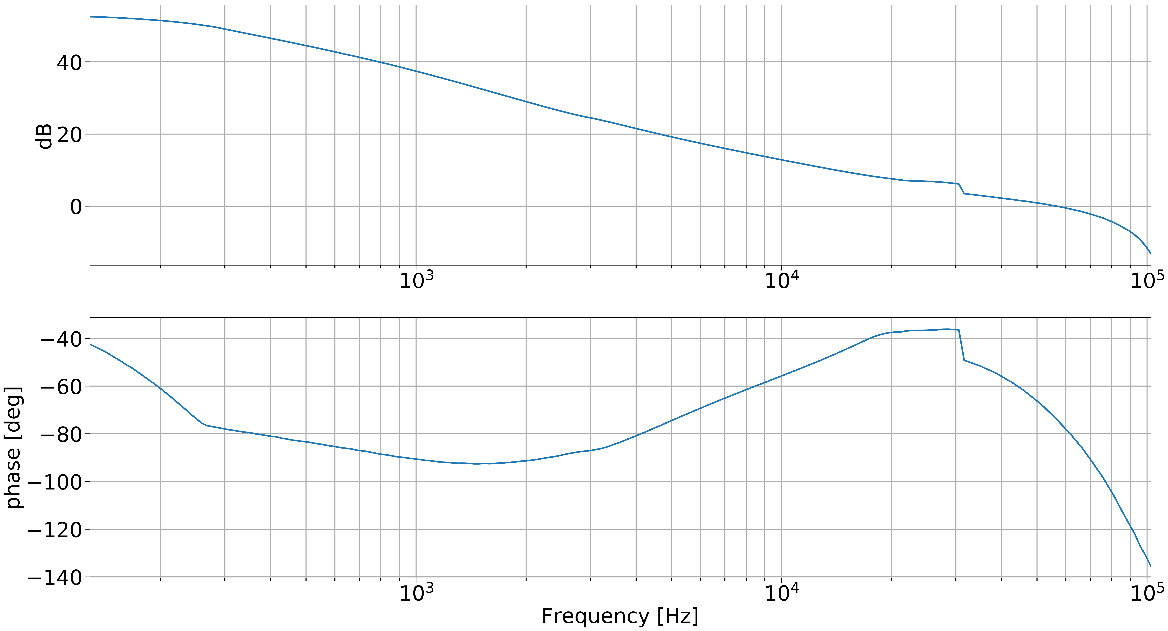
measurements/FSS_tfs/05_31_2020/exc1V/plot.png
