dancvan/AlGaAs_electrooptic_effect/measurements/FSS_tfs/05_31_2020/exc300mV_long_range/plot.png

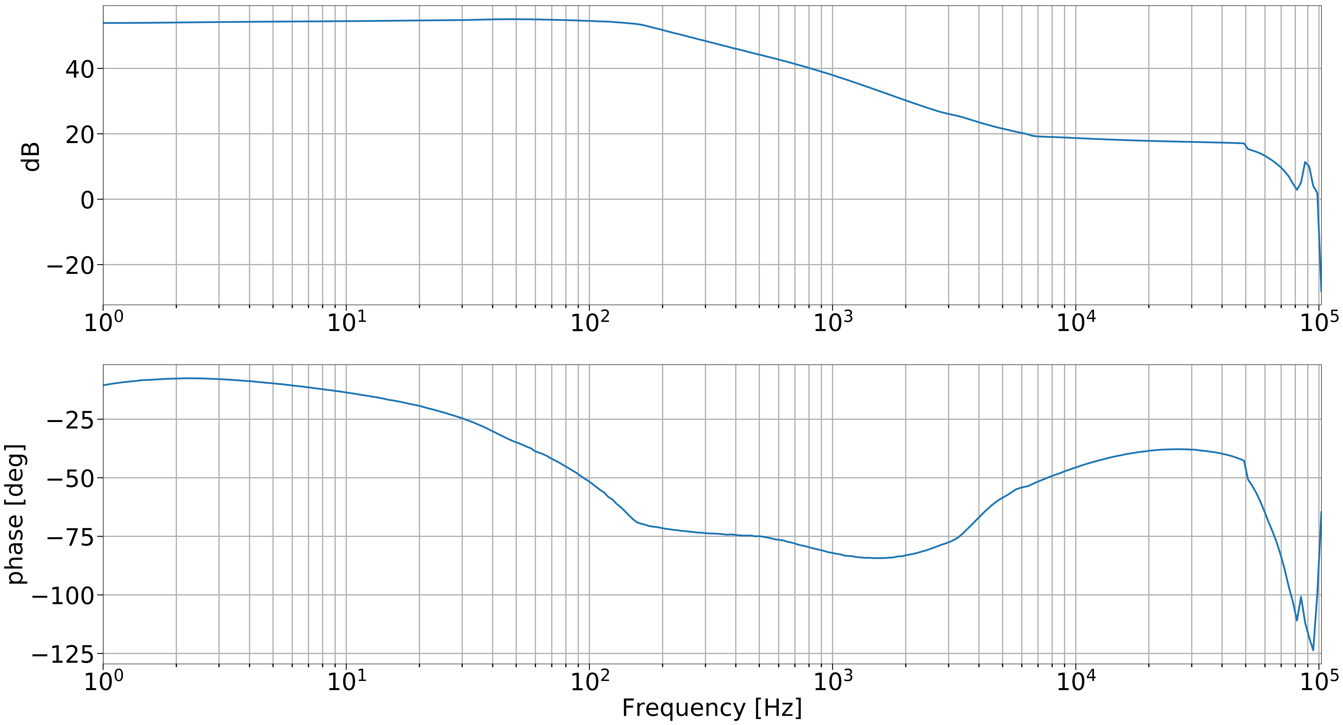
measurements/FSS_tfs/05_31_2020/exc300mV_long_range/plot.png
