dancvan/AlGaAs_electrooptic_effect/measurements/FSS_tfs/12_13_2019/FSS_servo_tf.png

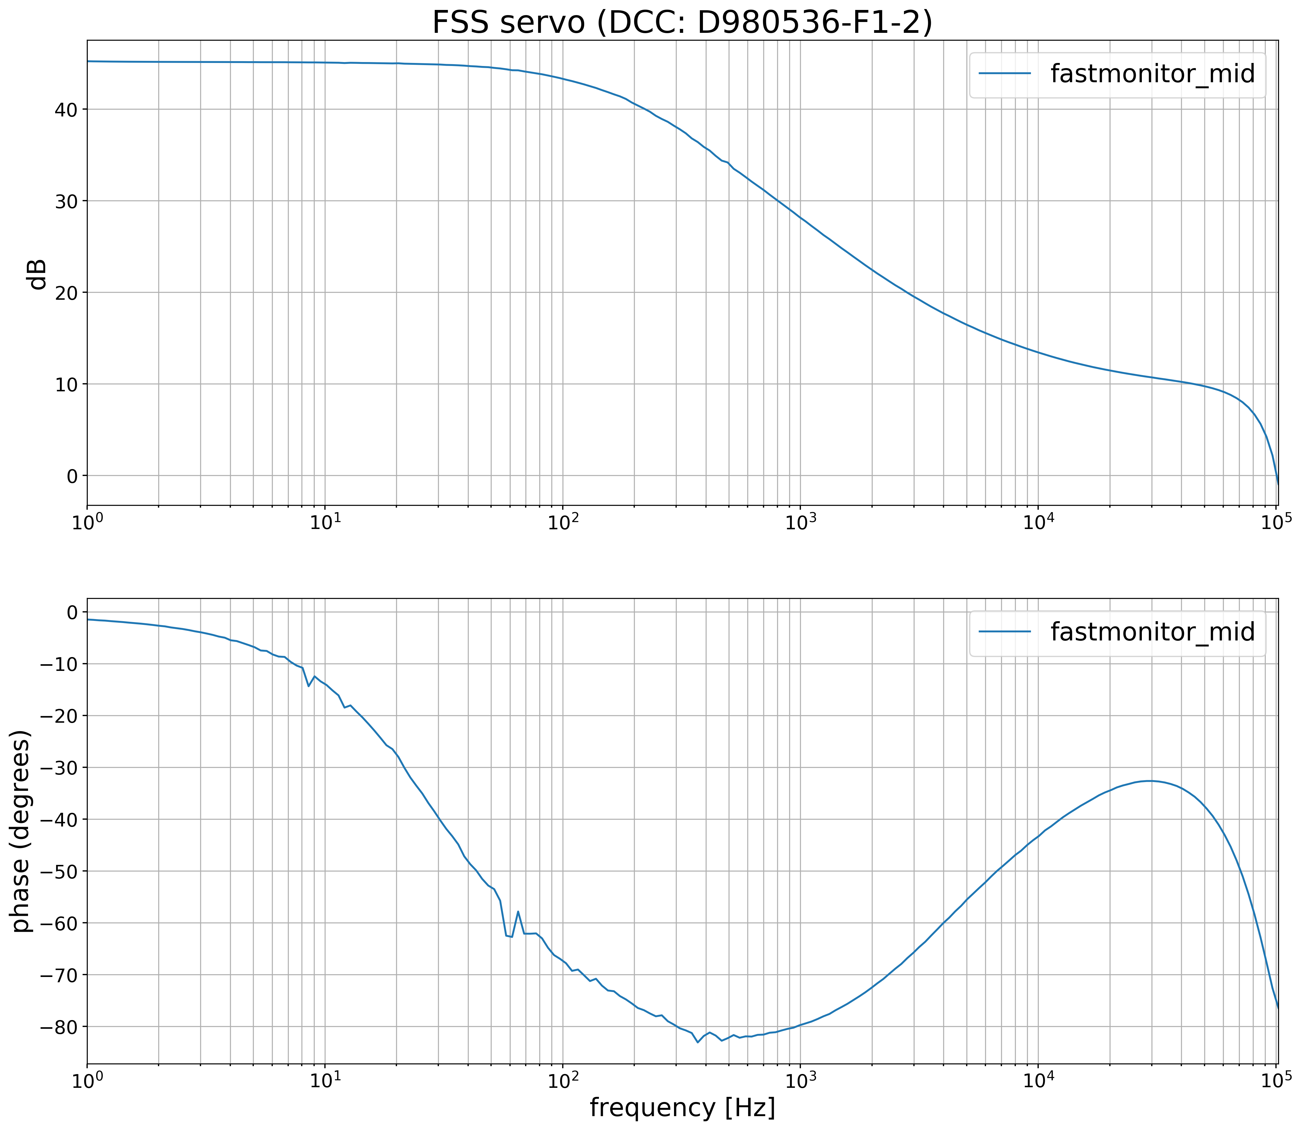
measurements/FSS_tfs/12_13_2019/FSS_servo_tf.png
