dancvan/AlGaAs_electrooptic_effect/measurements/FSS_tfs/12_14_2019a/FSS_servo_tf_fastmonitor_lasergain.png

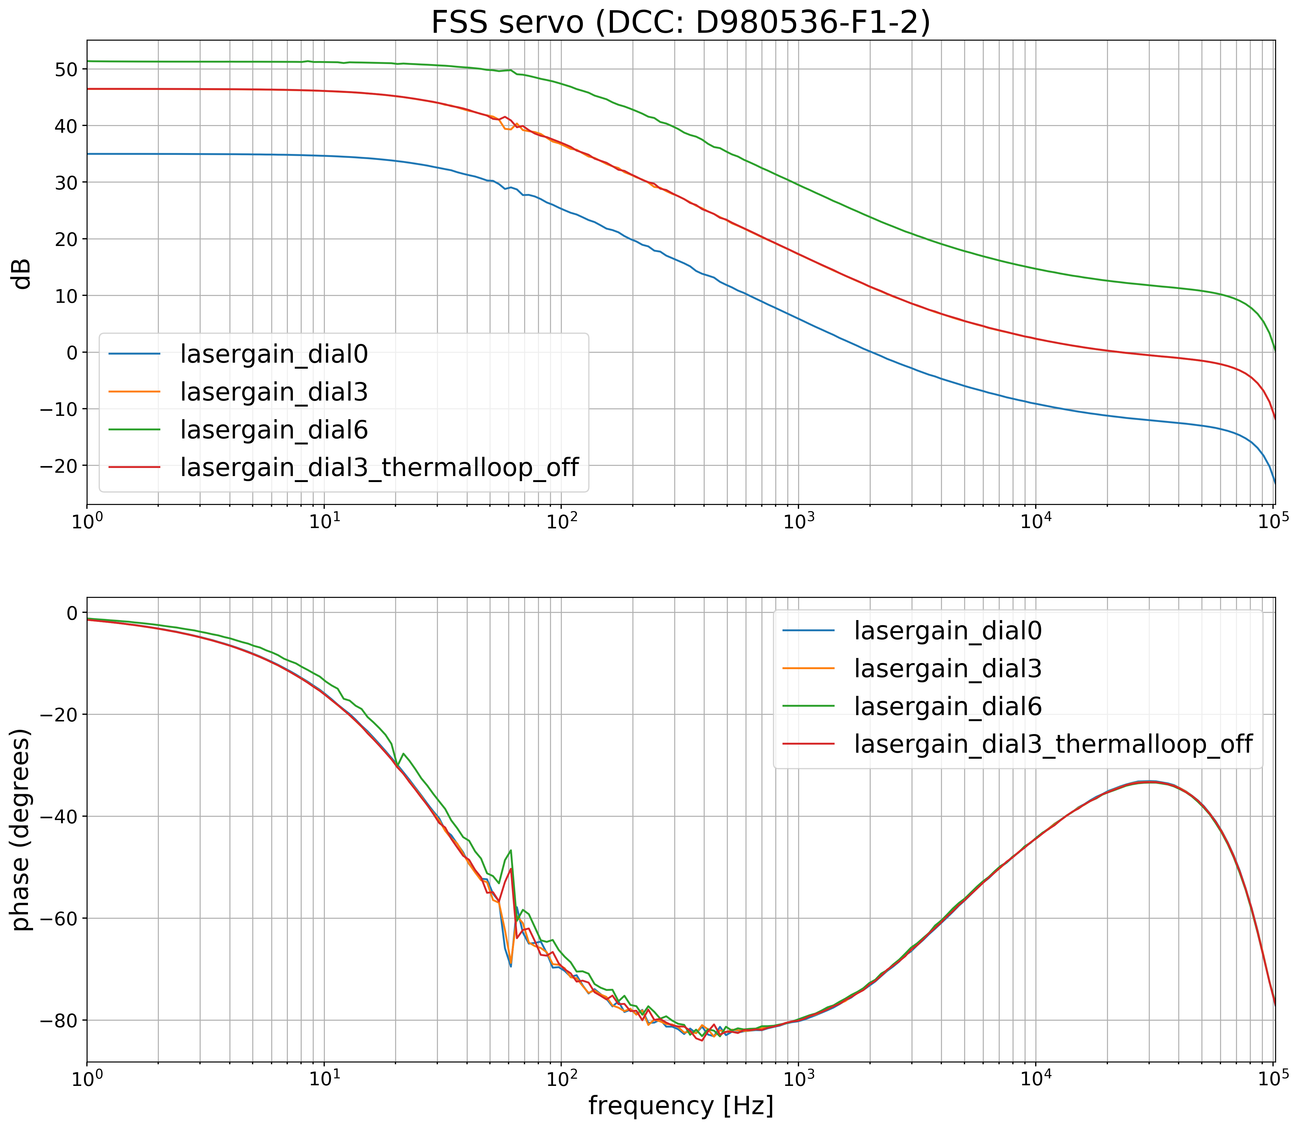
measurements/FSS_tfs/12_14_2019a/FSS_servo_tf_fastmonitor_lasergain.png
