dancvan/AlGaAs_electrooptic_effect/measurements/FSS_tfs/12_14_2019b/FSS_servo_SR560_1_tf_fastmonitor_lasergain.png

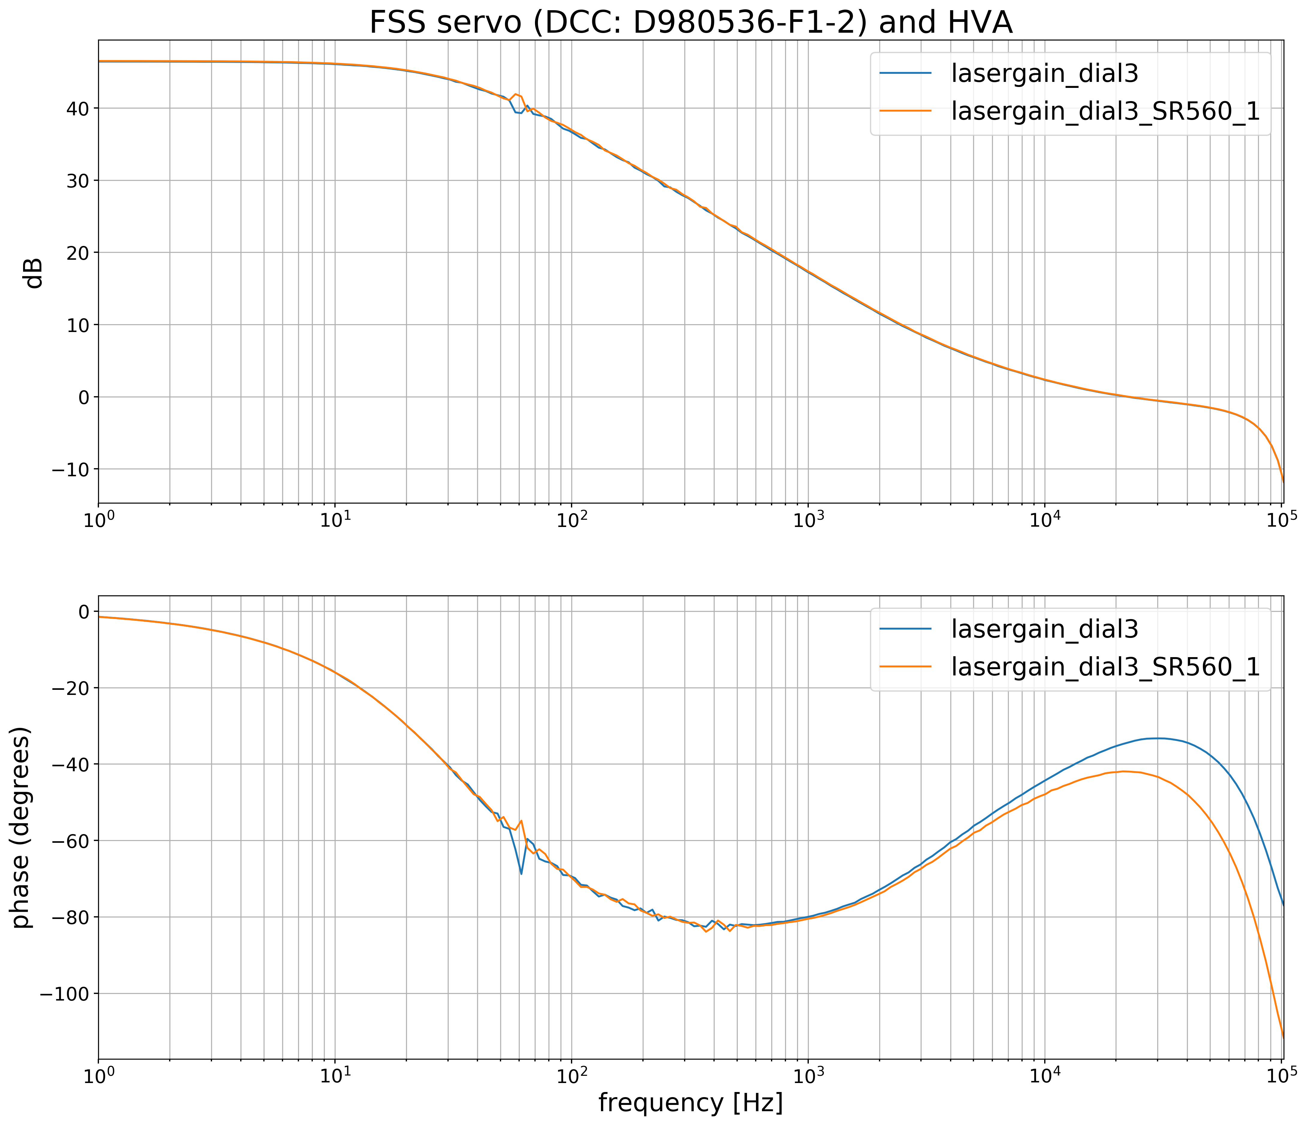
measurements/FSS_tfs/12_14_2019b/FSS_servo_SR560_1_tf_fastmonitor_lasergain.png
