dancvan/AlGaAs_electrooptic_effect/measurements/FSS_tfs/PNG image.png

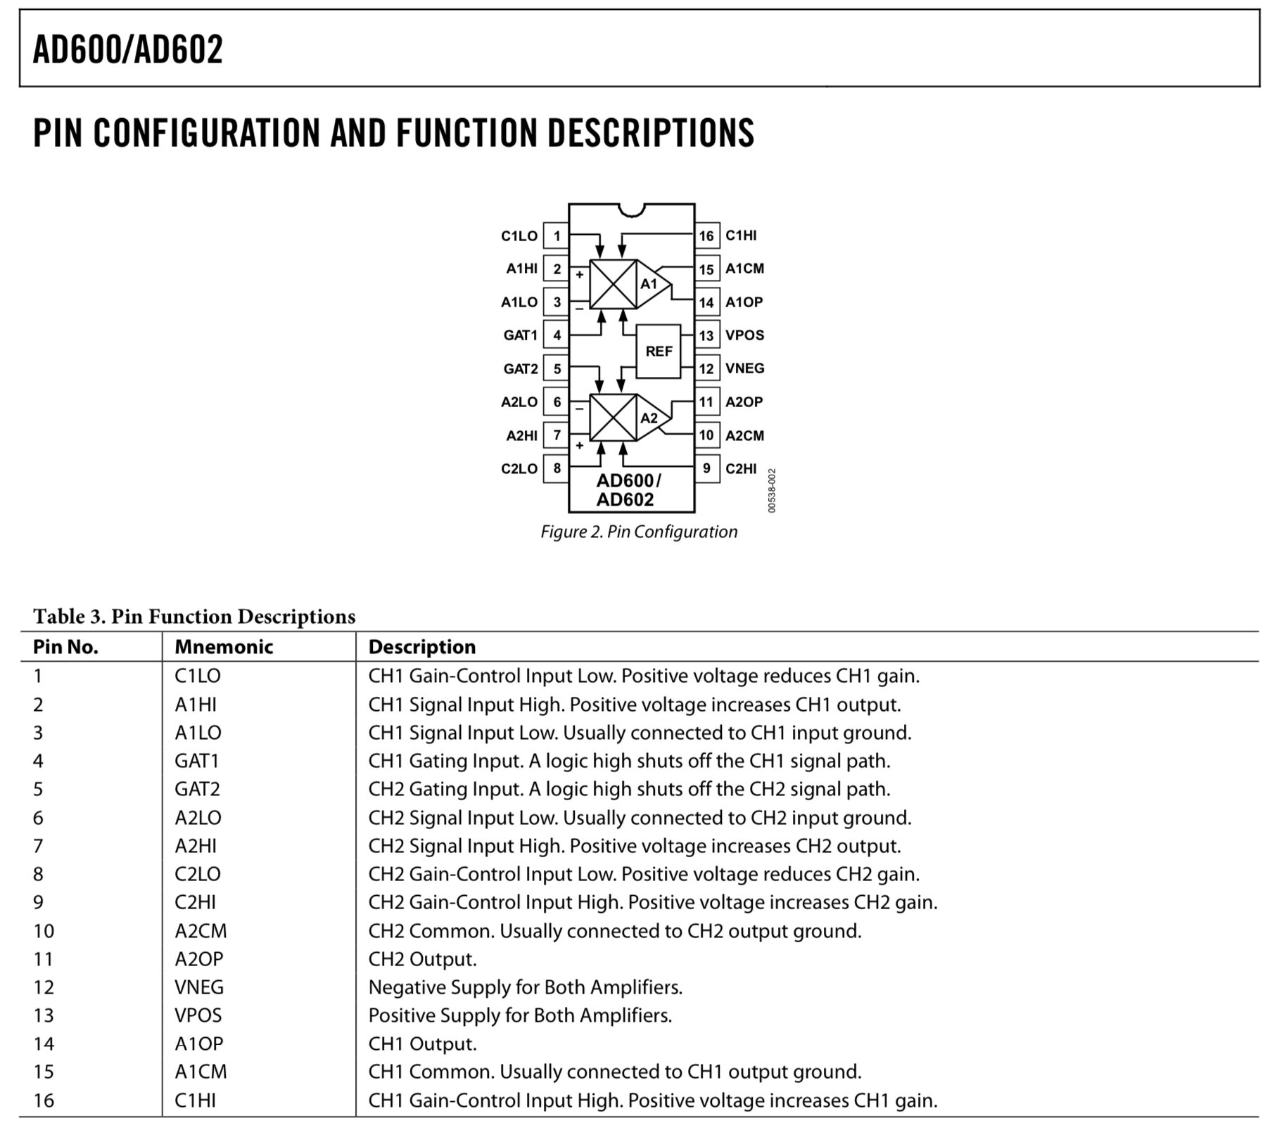
measurements/FSS_tfs/PNG image.png
