dancvan/AlGaAs_electrooptic_effect/measurements/FSS_tfs/spice/10_14_2020/ellip.png

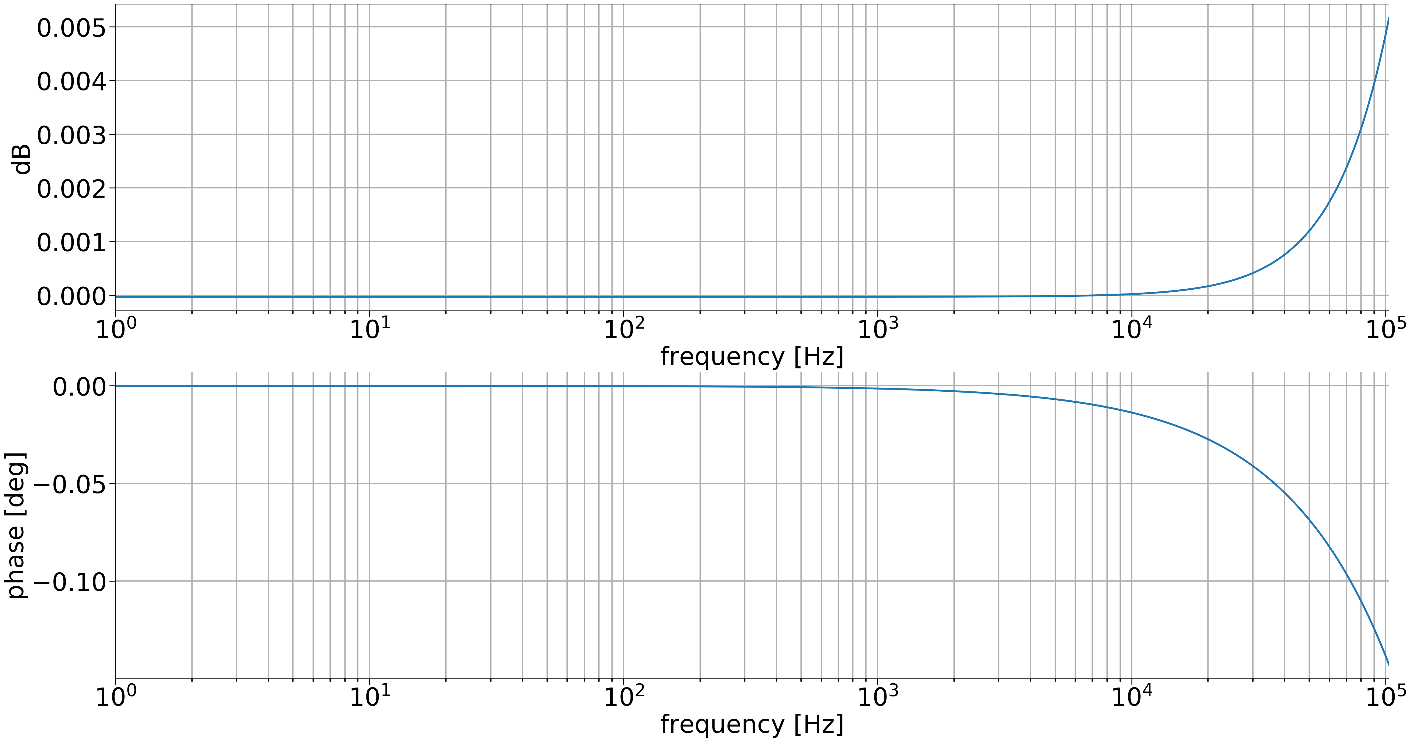
measurements/FSS_tfs/spice/10_14_2020/ellip.png
