dancvan/AlGaAs_electrooptic_effect/measurements/FSS_tfs/spice/10_14_2020/tp14.png

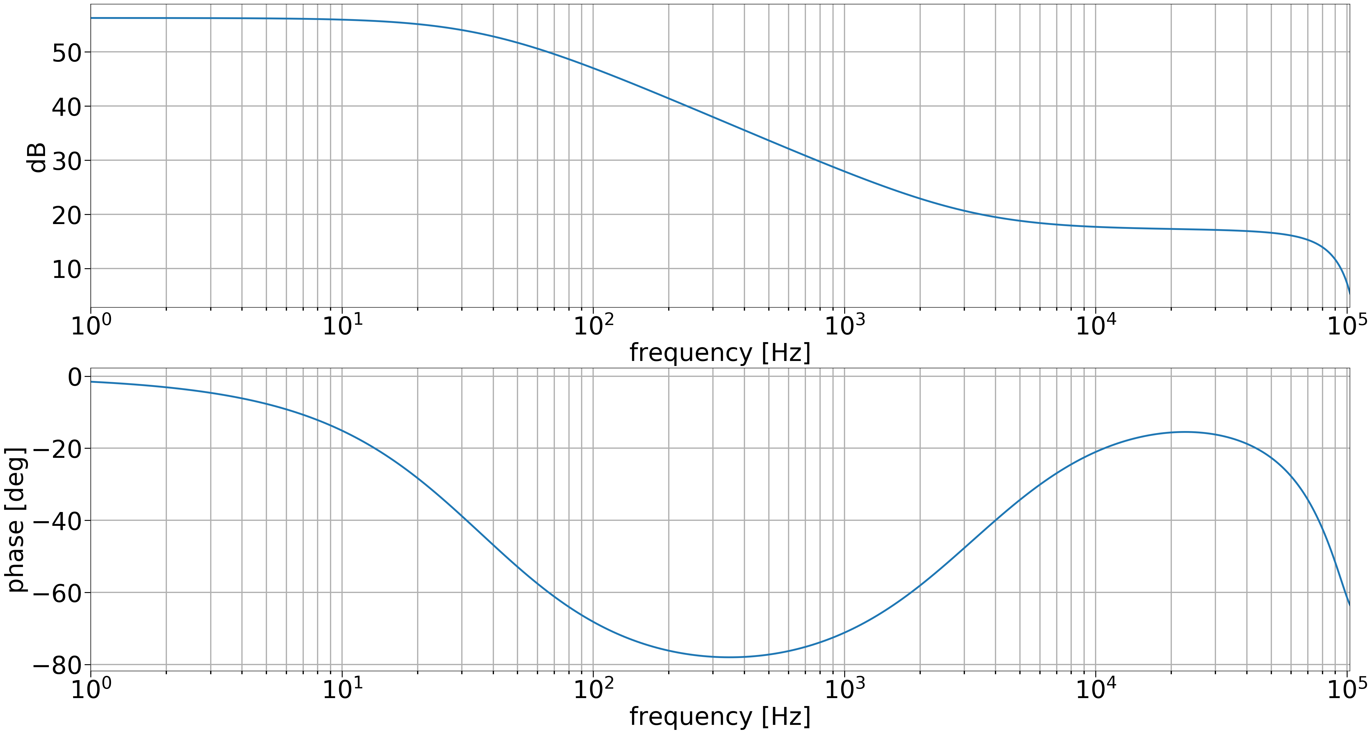
measurements/FSS_tfs/spice/10_14_2020/tp14.png
