dancvan/AlGaAs_electrooptic_effect/measurements/FSS_tfs/stages/in2_fm/plot.png

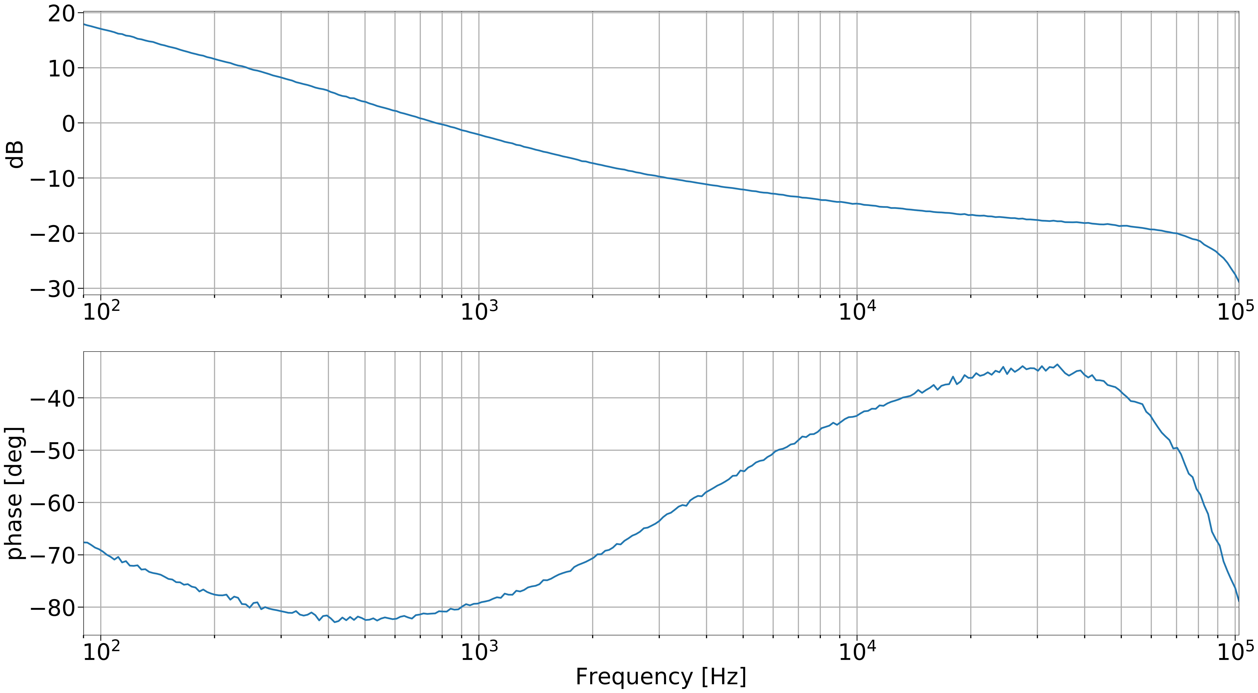
measurements/FSS_tfs/stages/in2_fm/plot.png
