dancvan/AlGaAs_electrooptic_effect/measurements/FSS_tfs/stages/in2_tp13/plot.png

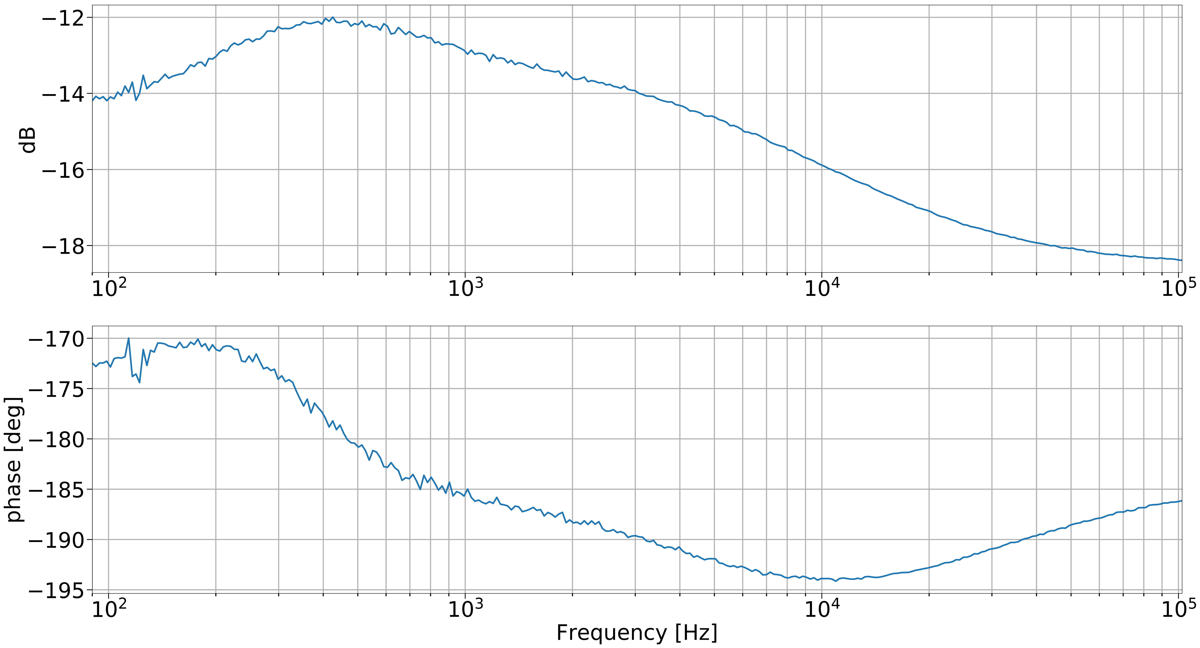
measurements/FSS_tfs/stages/in2_tp13/plot.png
