dancvan/AlGaAs_electrooptic_effect/measurements/FSS_tfs/with_IN2_switch_off/FSS_servo_tfs.png

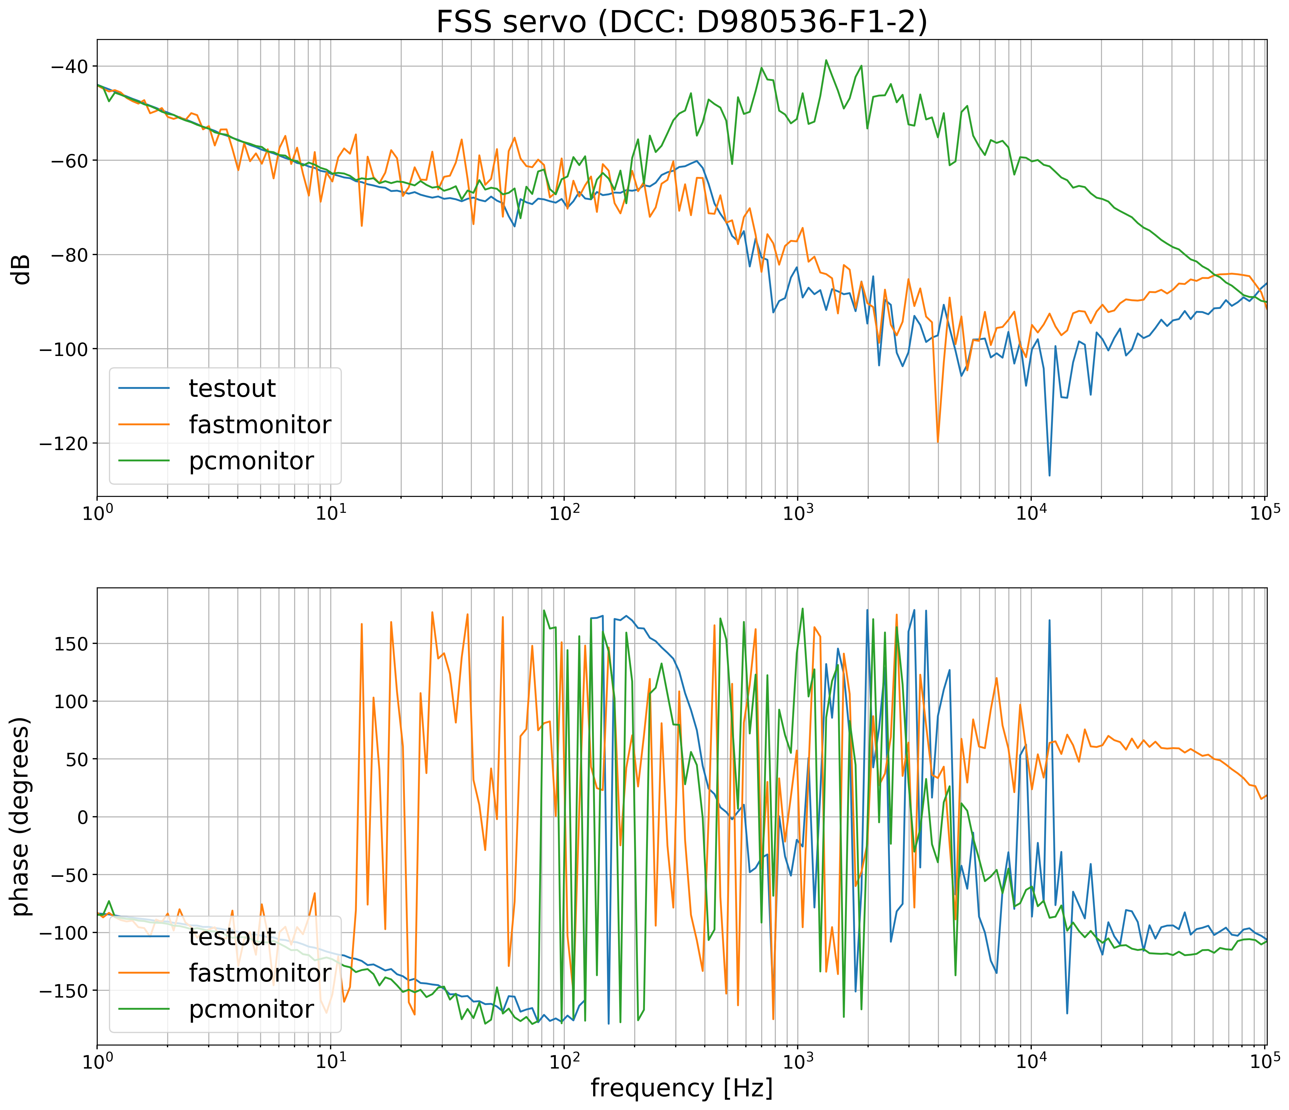
measurements/FSS_tfs/with_IN2_switch_off/FSS_servo_tfs.png
