dancvan/AlGaAs_electrooptic_effect/measurements/HP35670A/noise_floor/HP35670a_noise_flooor.png

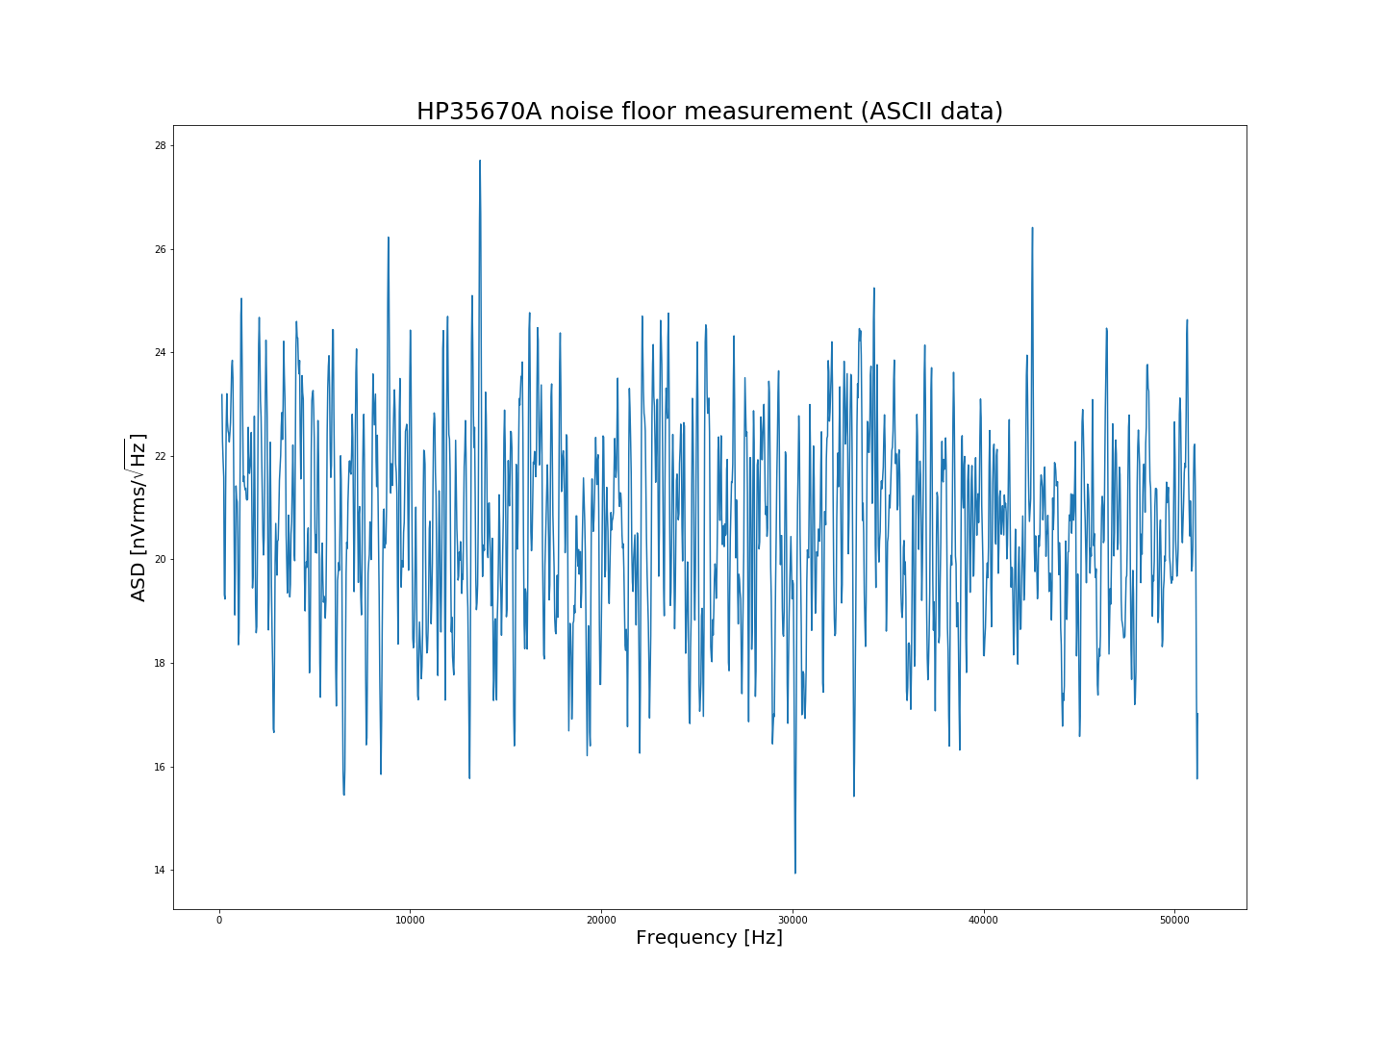
measurements/HP35670A/noise_floor/HP35670a_noise_flooor.png
