dancvan/AlGaAs_electrooptic_effect/measurements/HVA_PI/03_02_2020/HVA_PI.png

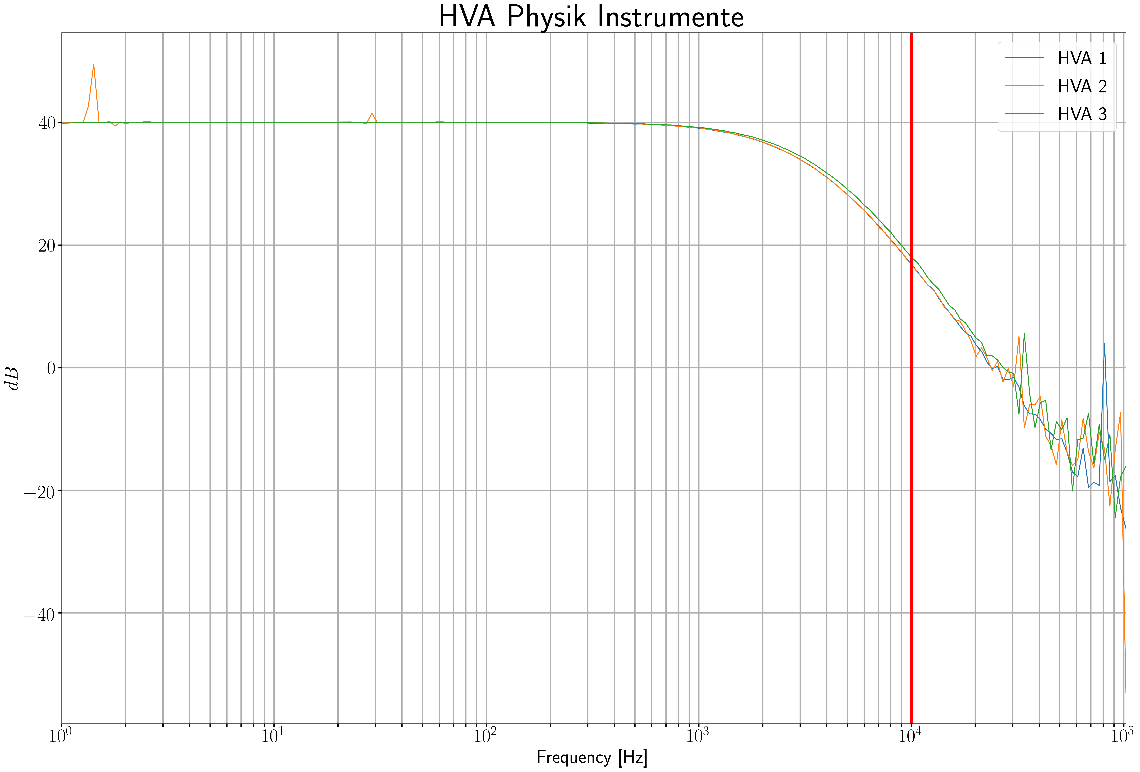
measurements/HVA_PI/03_02_2020/HVA_PI.png
