dancvan/AlGaAs_electrooptic_effect/measurements/HVASVR_tf/HVACH3_plus_pomona/02_19_2020/HVA_plus_pomona_tf.png

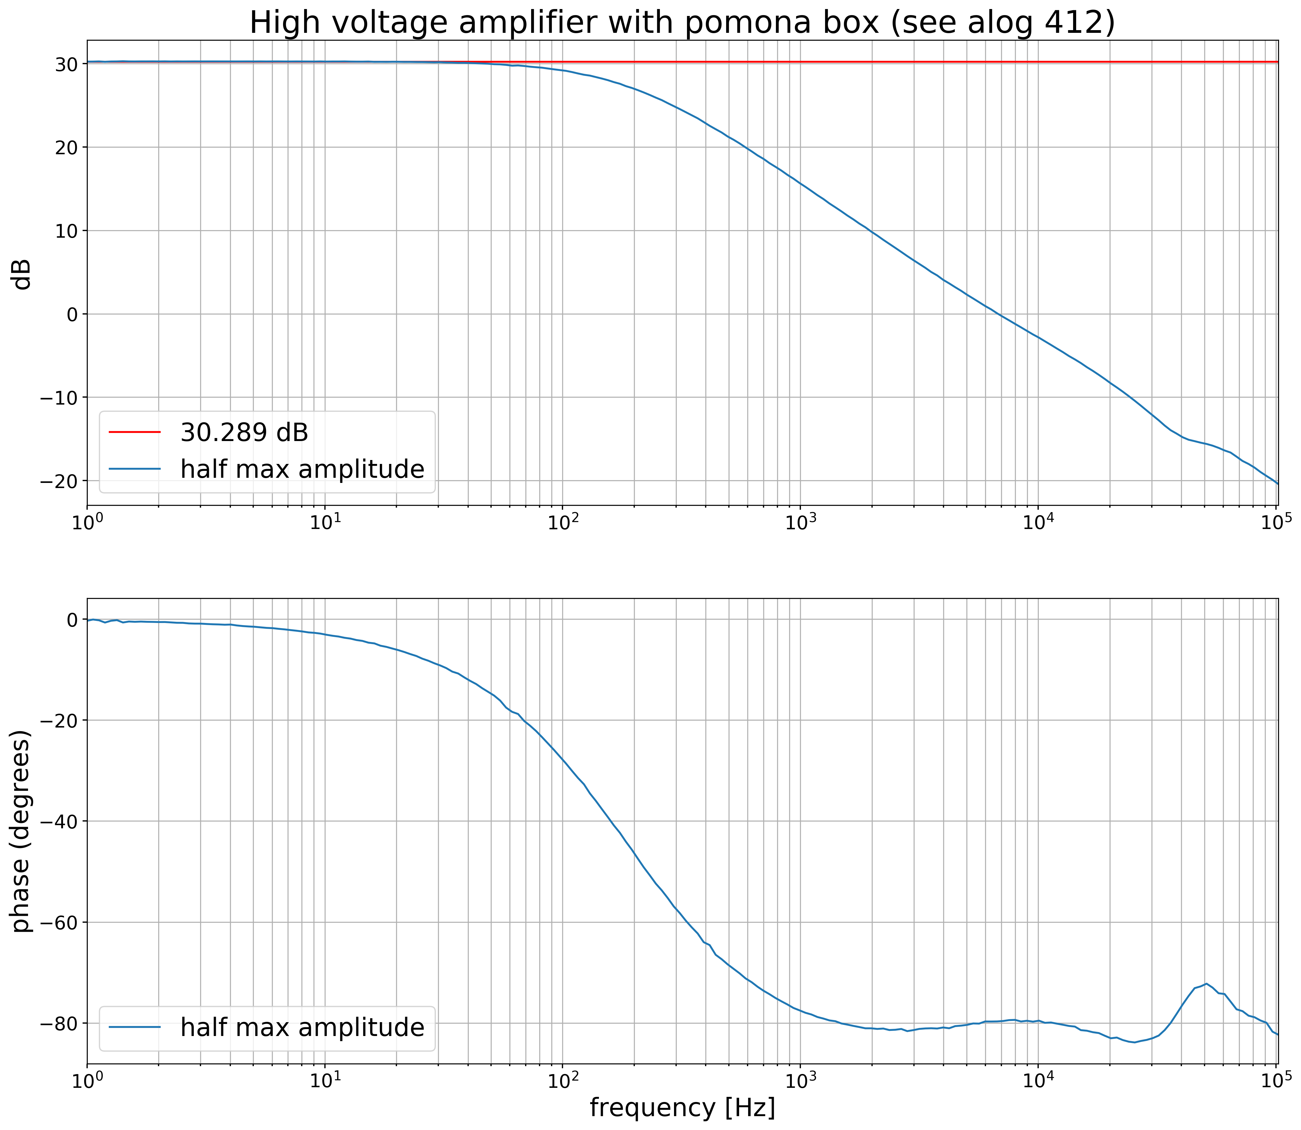
measurements/HVASVR_tf/HVACH3_plus_pomona/02_19_2020/HVA_plus_pomona_tf.png
