dancvan/AlGaAs_electrooptic_effect/measurements/HVASVR_tf/HVACH3_plus_pomona/05_31_2020/range3/plot.png

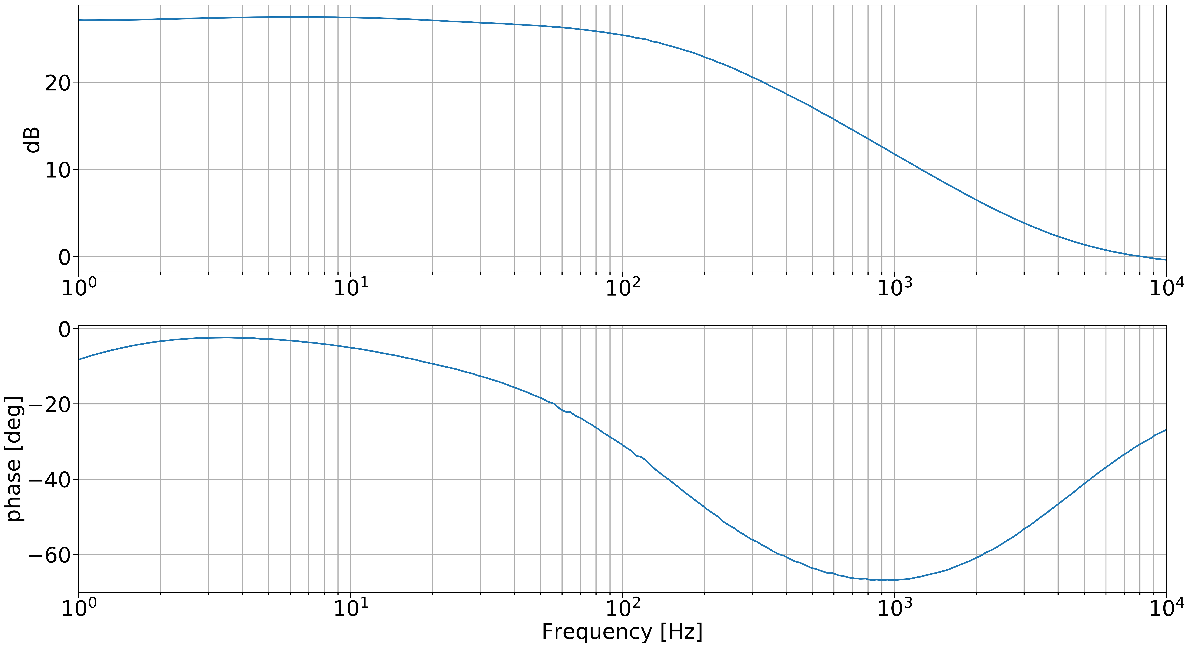
measurements/HVASVR_tf/HVACH3_plus_pomona/05_31_2020/range3/plot.png
