dancvan/AlGaAs_electrooptic_effect/measurements/HVASVR_tf/HVACH3_wo_pomona/05_31_2020/plot.png

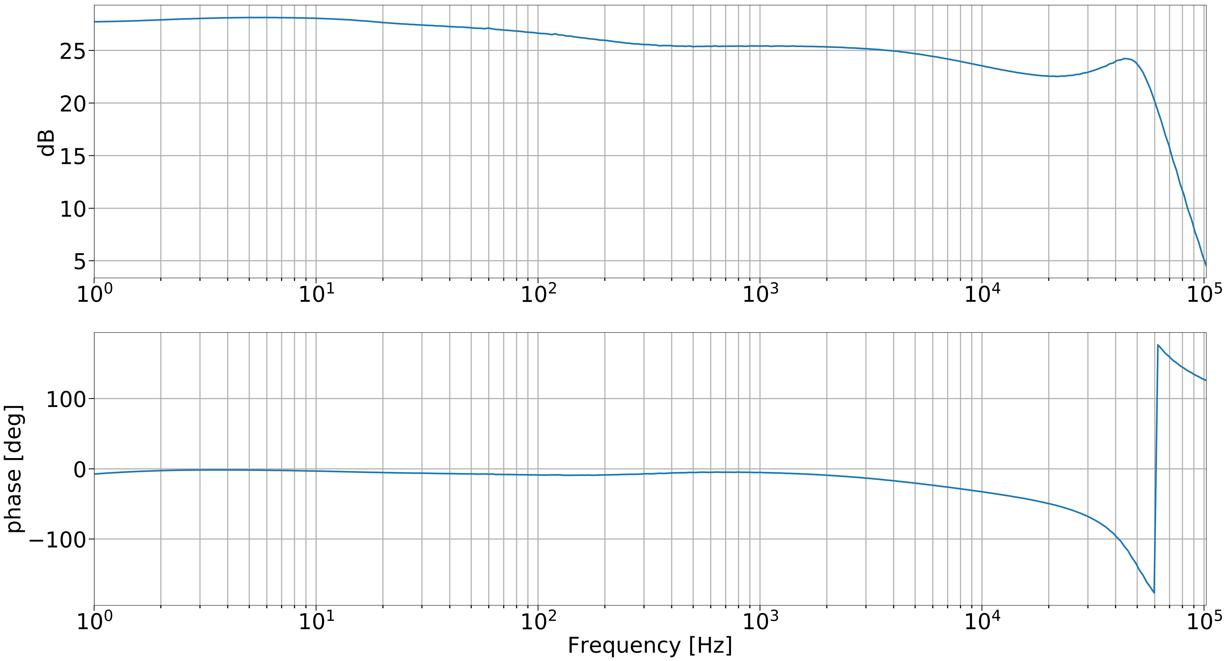
measurements/HVASVR_tf/HVACH3_wo_pomona/05_31_2020/plot.png
