dancvan/AlGaAs_electrooptic_effect/measurements/HVASVR_tf/measurements_HVA_crosstalk/HVA_CH1_CH3_cc_measurement.jpg

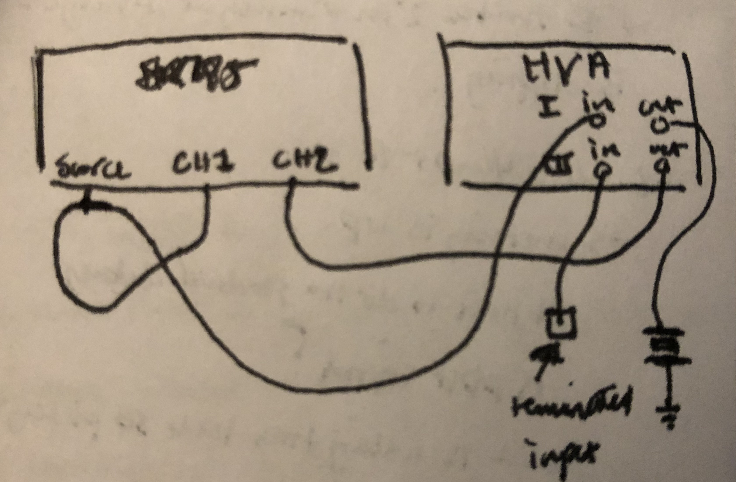
measurements/HVASVR_tf/measurements_HVA_crosstalk/HVA_CH1_CH3_cc_measurement.jpg
