dancvan/AlGaAs_electrooptic_effect/measurements/OLG/algaas/05_31_2020/plot.png

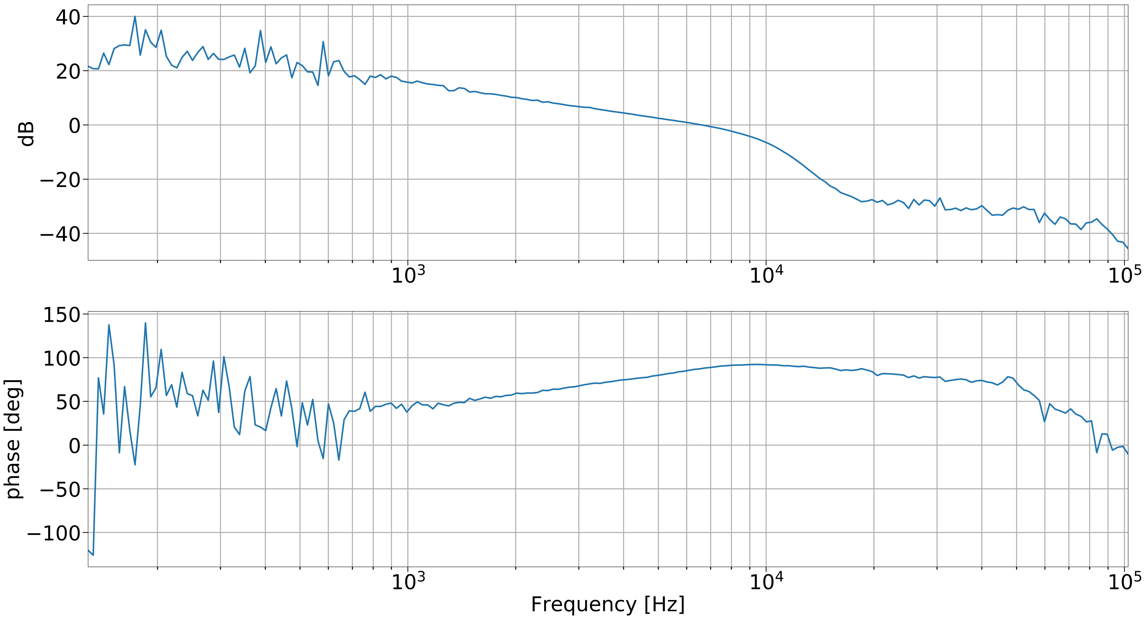
measurements/OLG/algaas/05_31_2020/plot.png
