dancvan/AlGaAs_electrooptic_effect/measurements/OLG/algaas/08_21_2020/plot.png

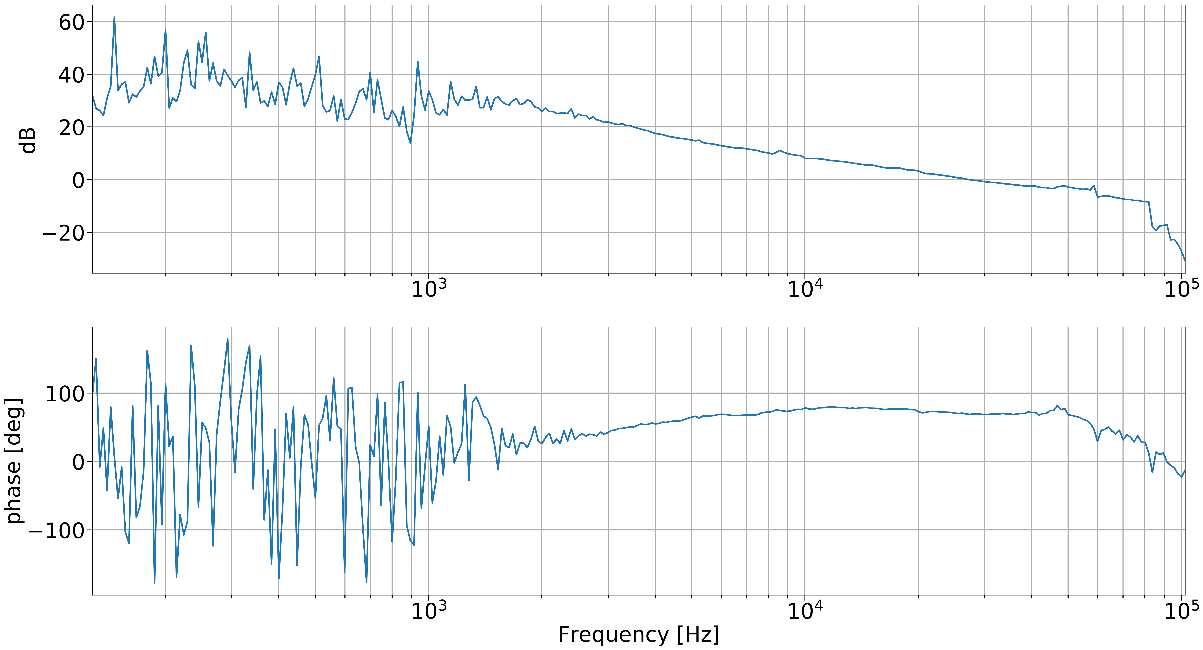
measurements/OLG/algaas/08_21_2020/plot.png
