dancvan/AlGaAs_electrooptic_effect/measurements/pomona_box/02_17_2021/IMG_6488.jpeg

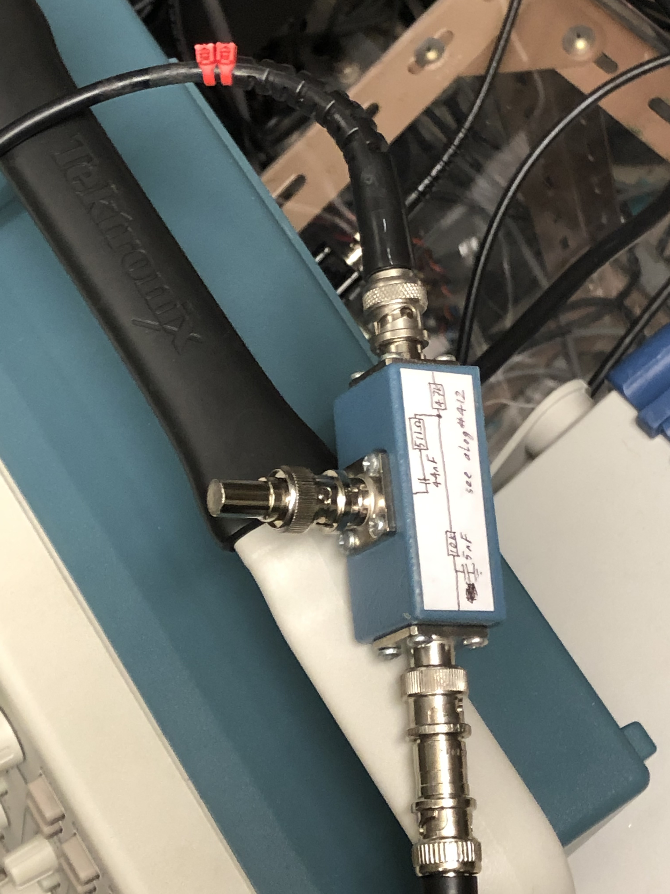
measurements/pomona_box/02_17_2021/IMG_6488.jpeg
