dancvan/AlGaAs_electrooptic_effect/measurements/single_frequency/algaas/04_26_2020/AlGaAs_driven/displacement_noise_floor_driven.png

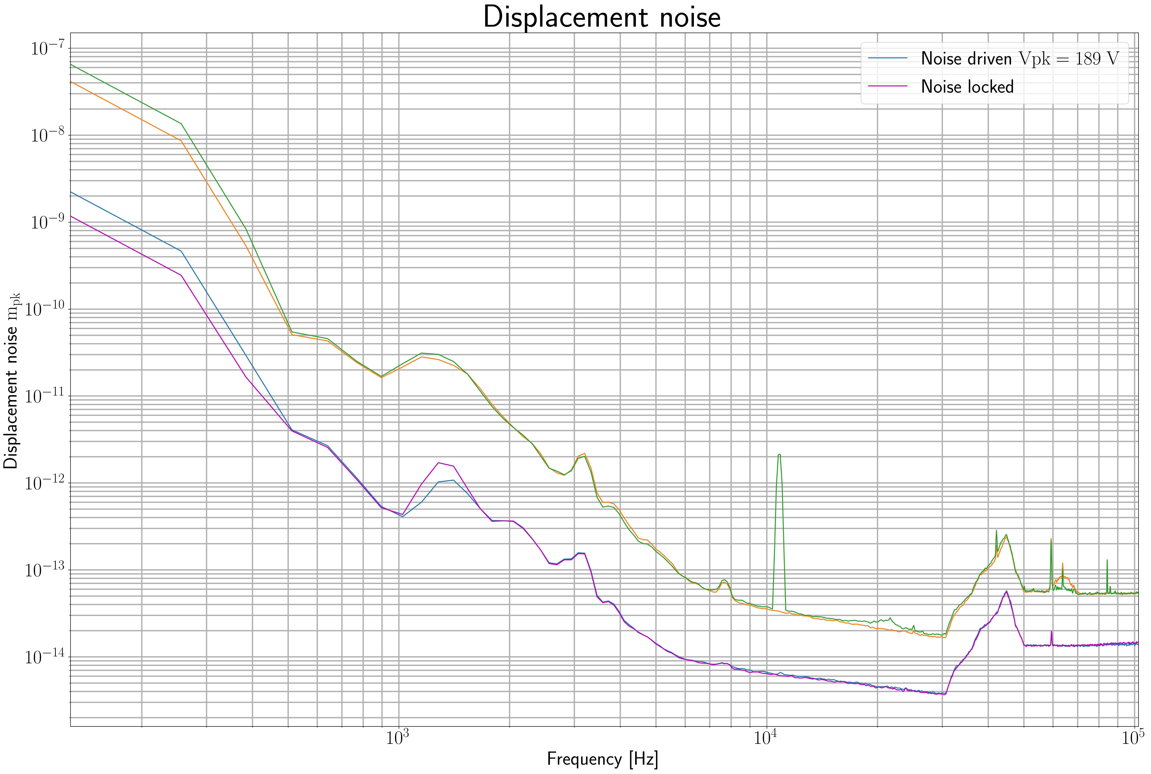
measurements/single_frequency/algaas/04_26_2020/AlGaAs_driven/displacement_noise_floor_driven.png
