dancvan/AlGaAs_electrooptic_effect/measurements/single_frequency/algaas/04_26_2020/init_drive_voltage/input_drive.png

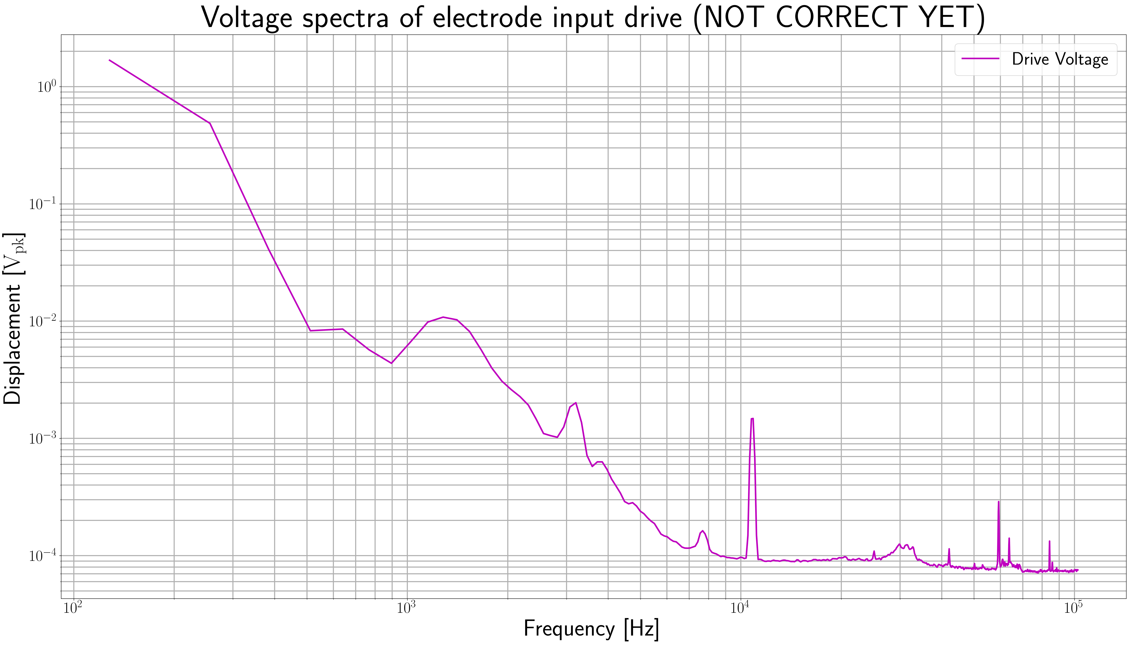
measurements/single_frequency/algaas/04_26_2020/init_drive_voltage/input_drive.png
