dancvan/AlGaAs_electrooptic_effect/measurements/single_frequency/sio2ta2o5/03_04_2020/displacement_electrodes_driven_300V.png

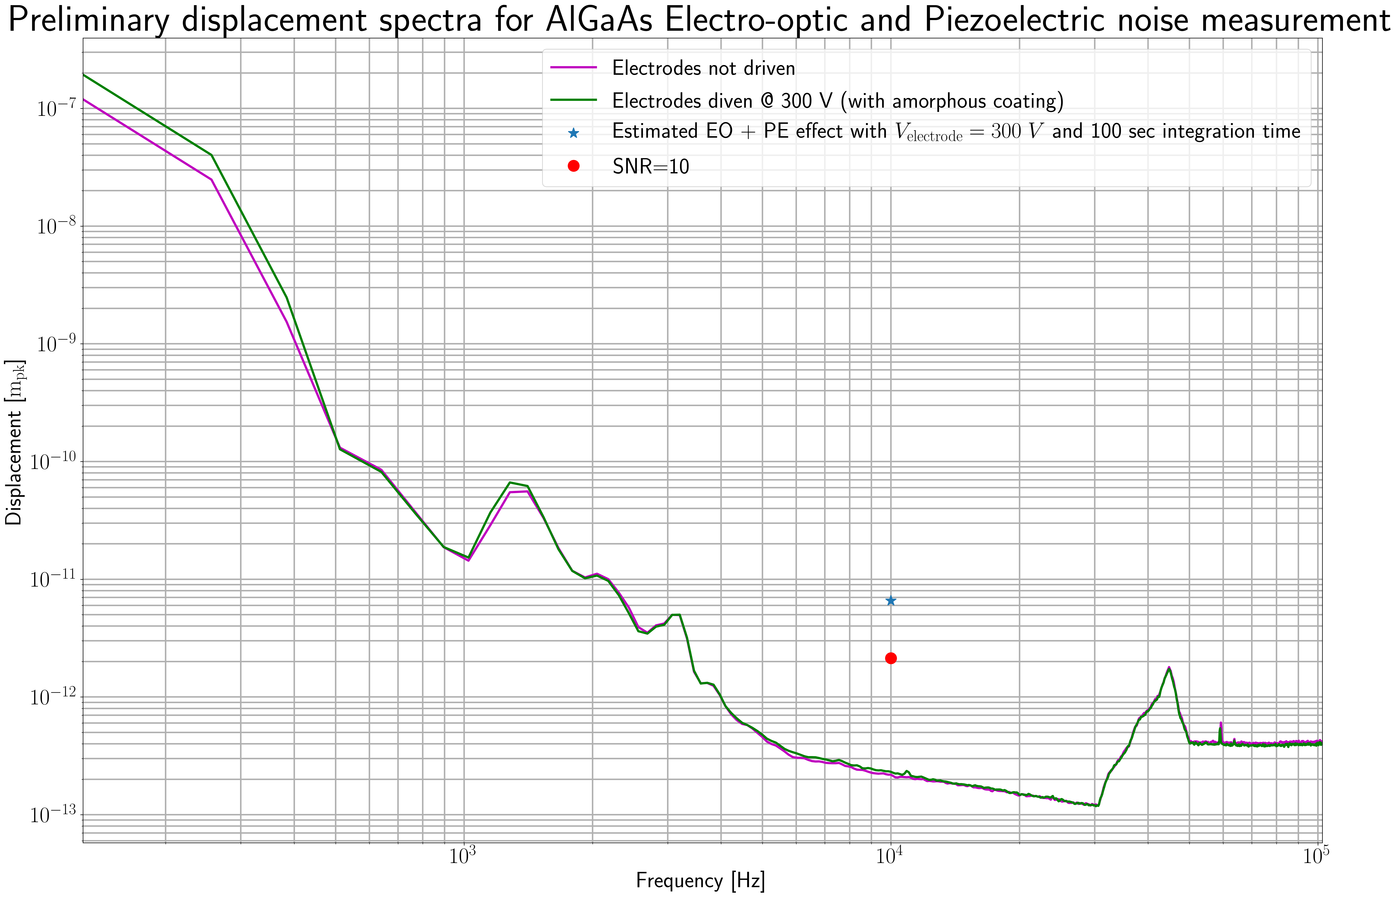
measurements/single_frequency/sio2ta2o5/03_04_2020/displacement_electrodes_driven_300V.png
