dancvan/AlGaAs_electrooptic_effect/measurements/single_frequency/sio2ta2o5/03_04_2020/noise_ratio2.png

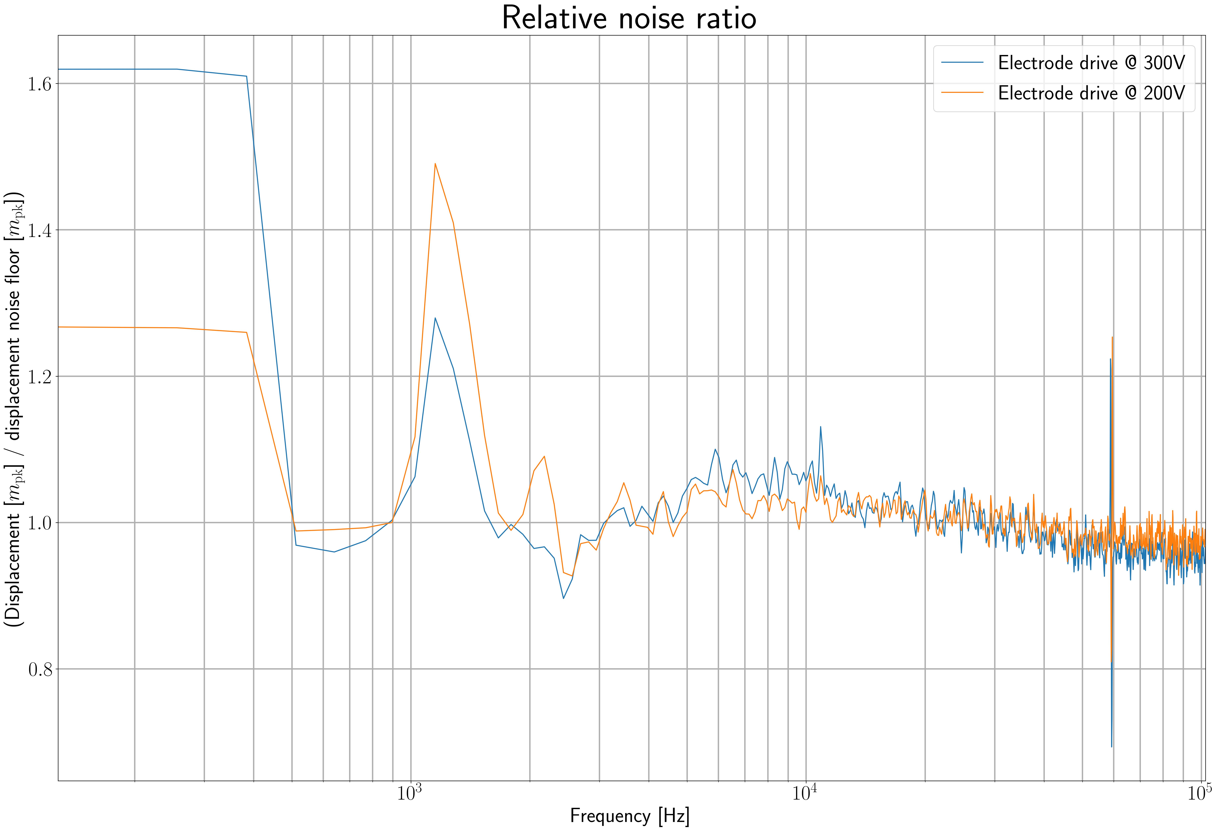
measurements/single_frequency/sio2ta2o5/03_04_2020/noise_ratio2.png
