dancvan/AlGaAs_electrooptic_effect/measurements/SR785_coherence_measurement/03_08_2021/meas2/plot.png

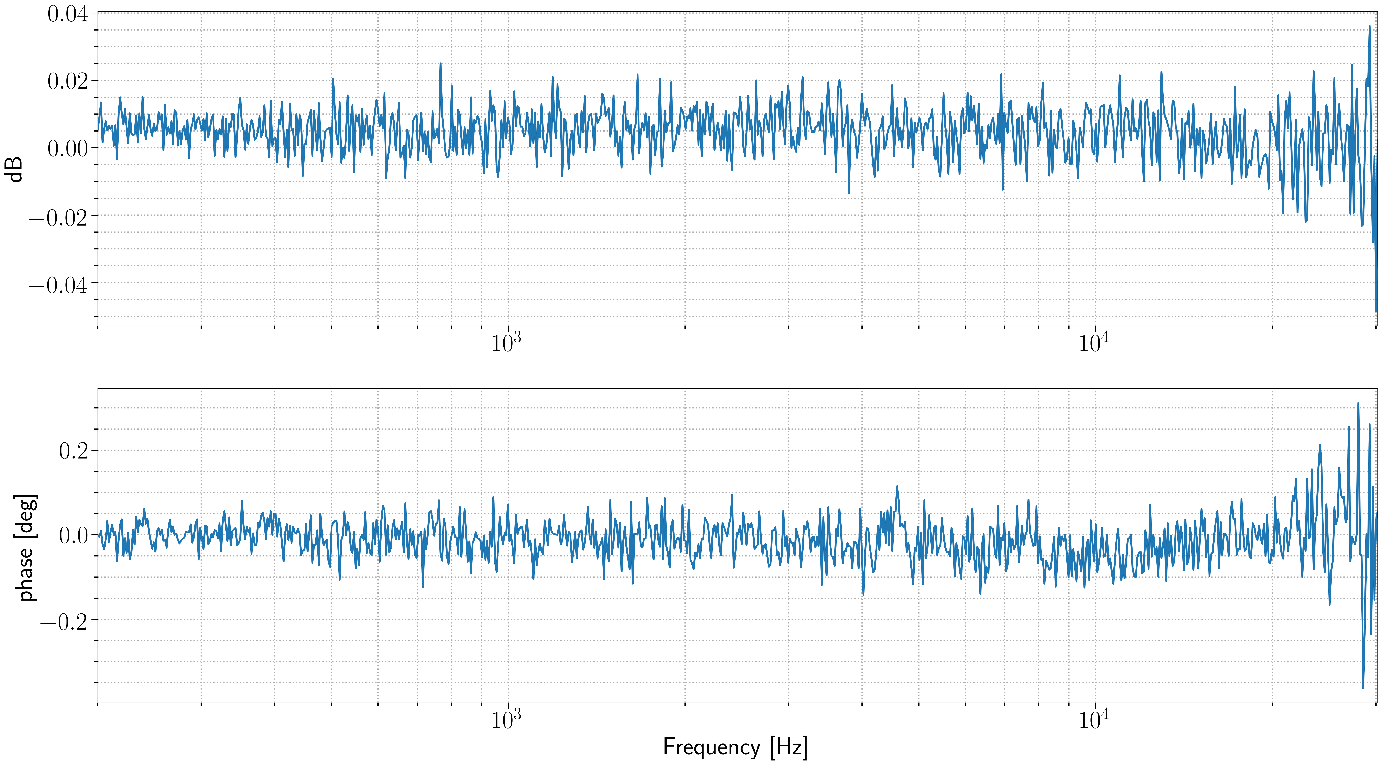
measurements/SR785_coherence_measurement/03_08_2021/meas2/plot.png
