dancvan/AlGaAs_electrooptic_effect/results/figures/electrodes/split_electrode_config.png

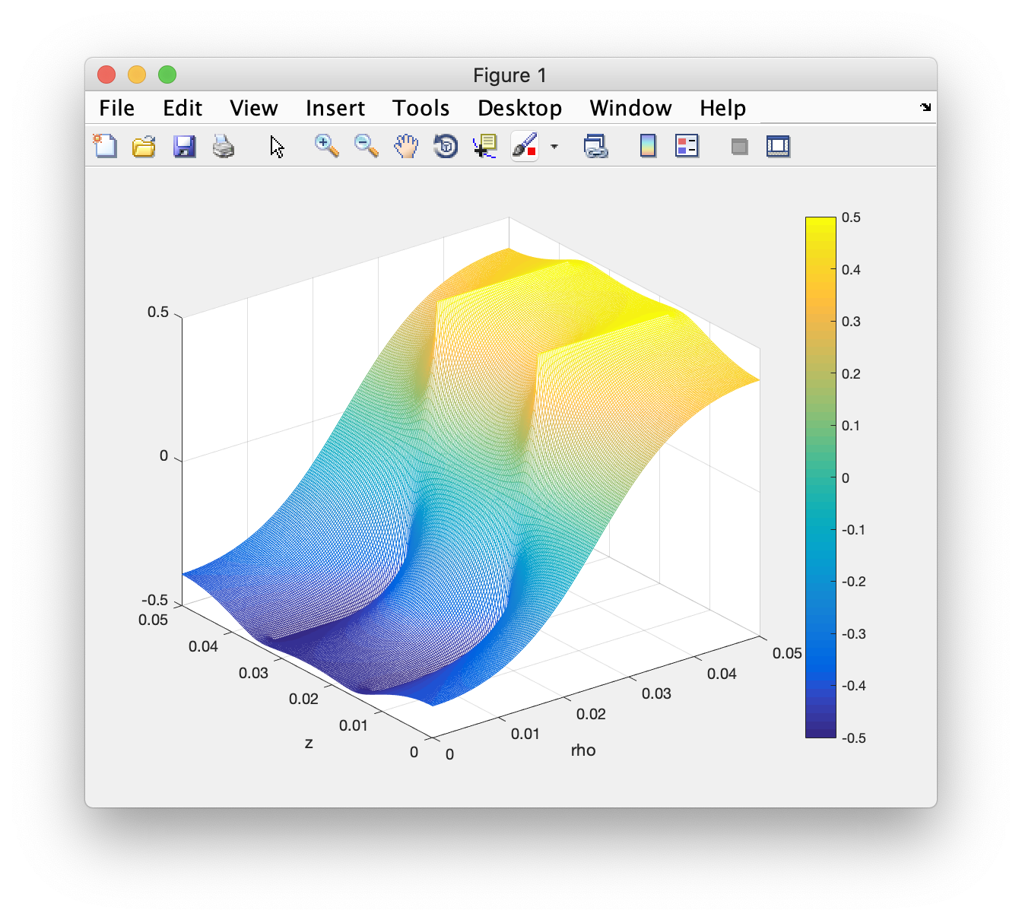
results/figures/electrodes/split_electrode_config.png
