dancvan/AlGaAs_electrooptic_effect/results/figures/electrodes/toy_figure_disks.png

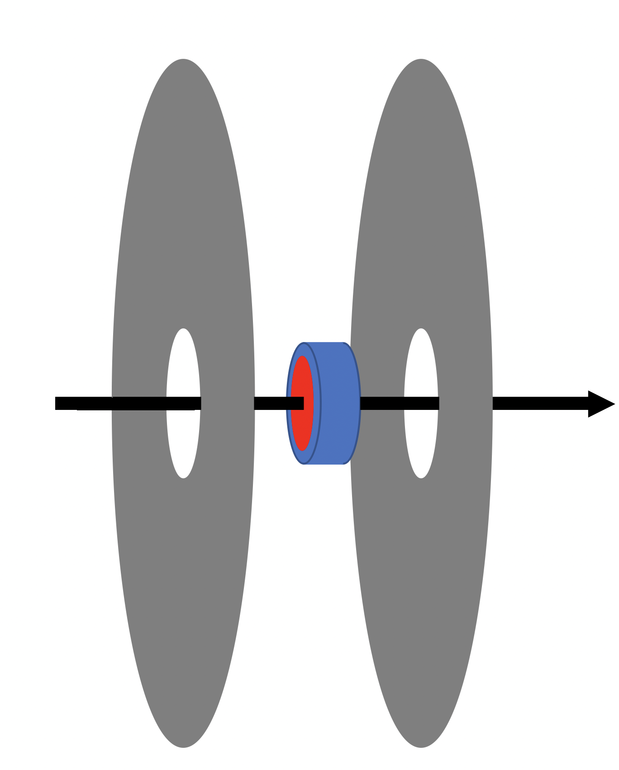
results/figures/electrodes/toy_figure_disks.png
