dancvan/AlGaAs_electrooptic_effect/results/figures/electrodes/toy_figure_disks_w_labl.png

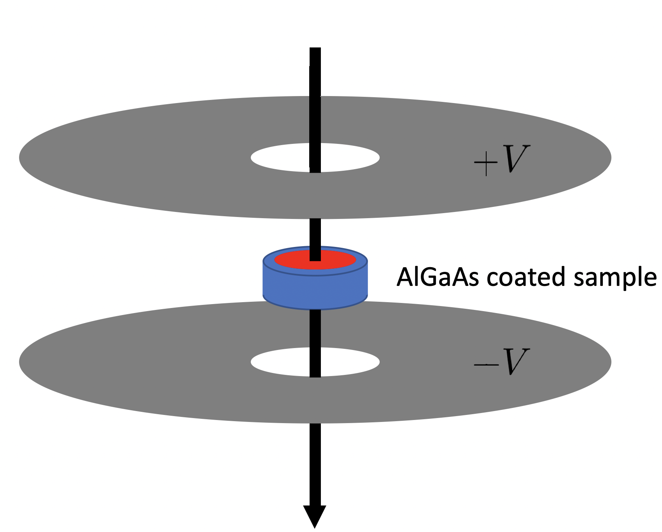
results/figures/electrodes/toy_figure_disks_w_labl.png
