dancvan/AlGaAs_electrooptic_effect/results/figures/schema/algaas_pockels_swept_sine.png

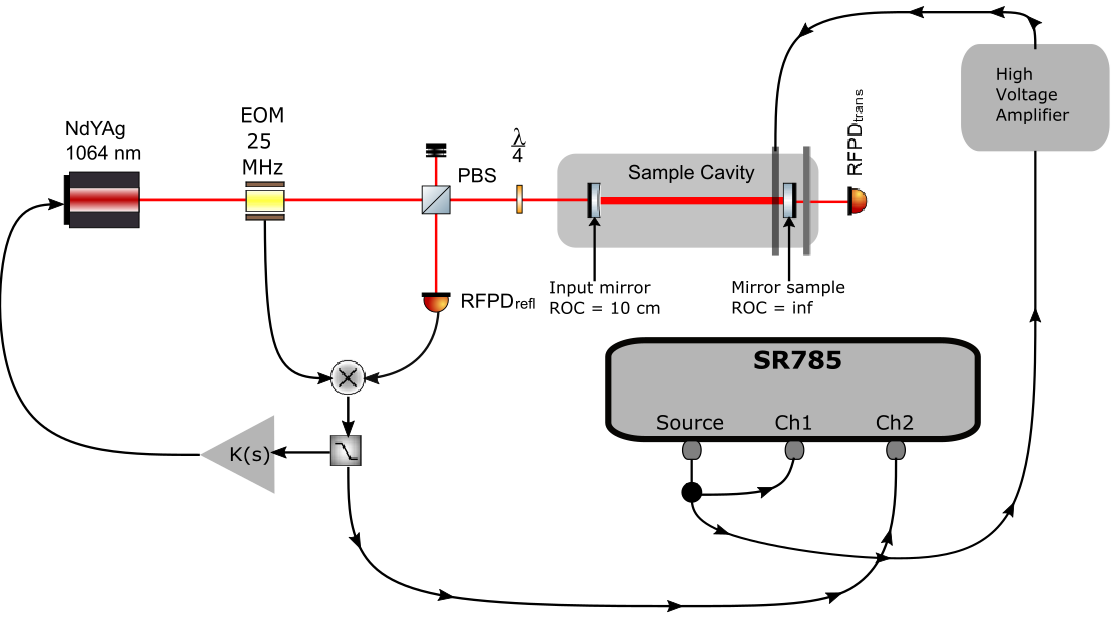
results/figures/schema/algaas_pockels_swept_sine.png
