dancvan/AlGaAs_electrooptic_effect/results/frequency_comb/03_13_2021a_comb_pk_sio2ta2o5/HVACH3+pomona.png

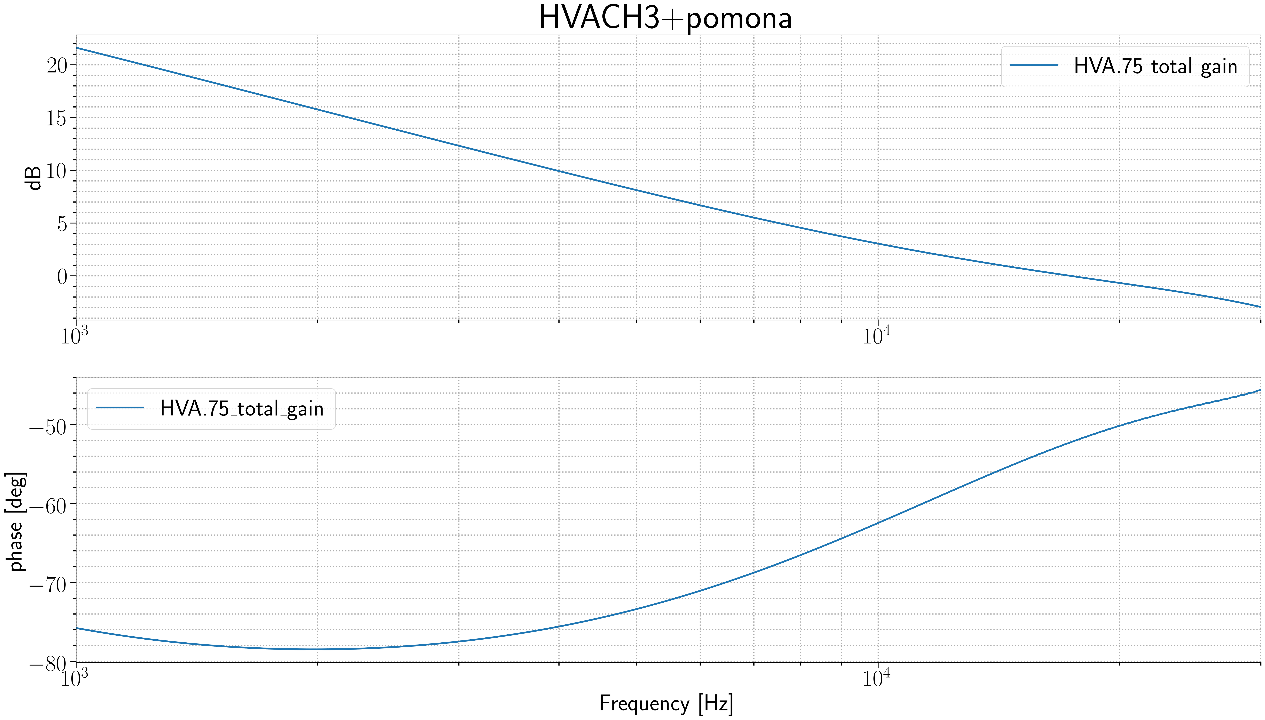
results/frequency_comb/03_13_2021a_comb_pk_sio2ta2o5/HVACH3+pomona.png
