dancvan/AlGaAs_electrooptic_effect/results/frequency_comb/FEB172021freqcomb/FEB172021freqcomb_displacement_normal_electrodes.png

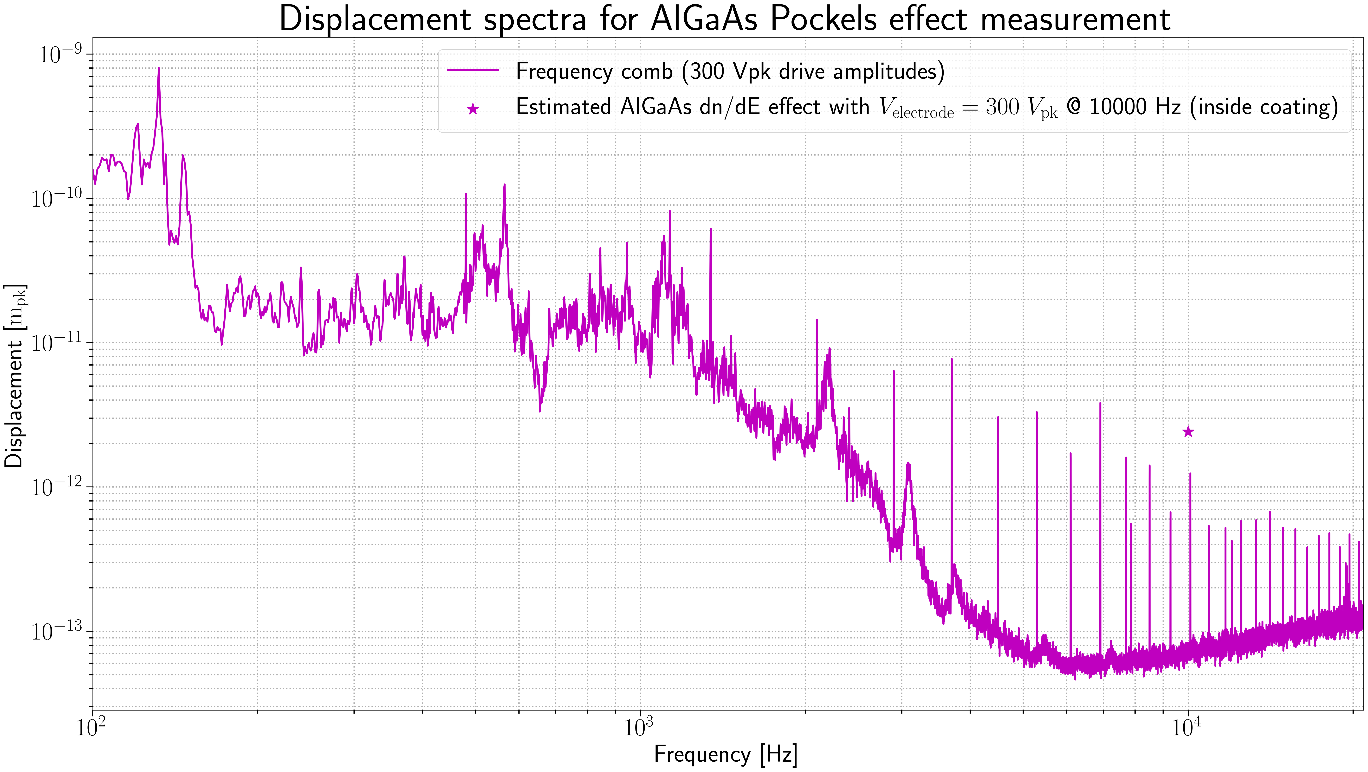
results/frequency_comb/FEB172021freqcomb/FEB172021freqcomb_displacement_normal_electrodes.png
