dancvan/AlGaAs_electrooptic_effect/results/frequency_comb/FEB172021freqcomb/HVA.png

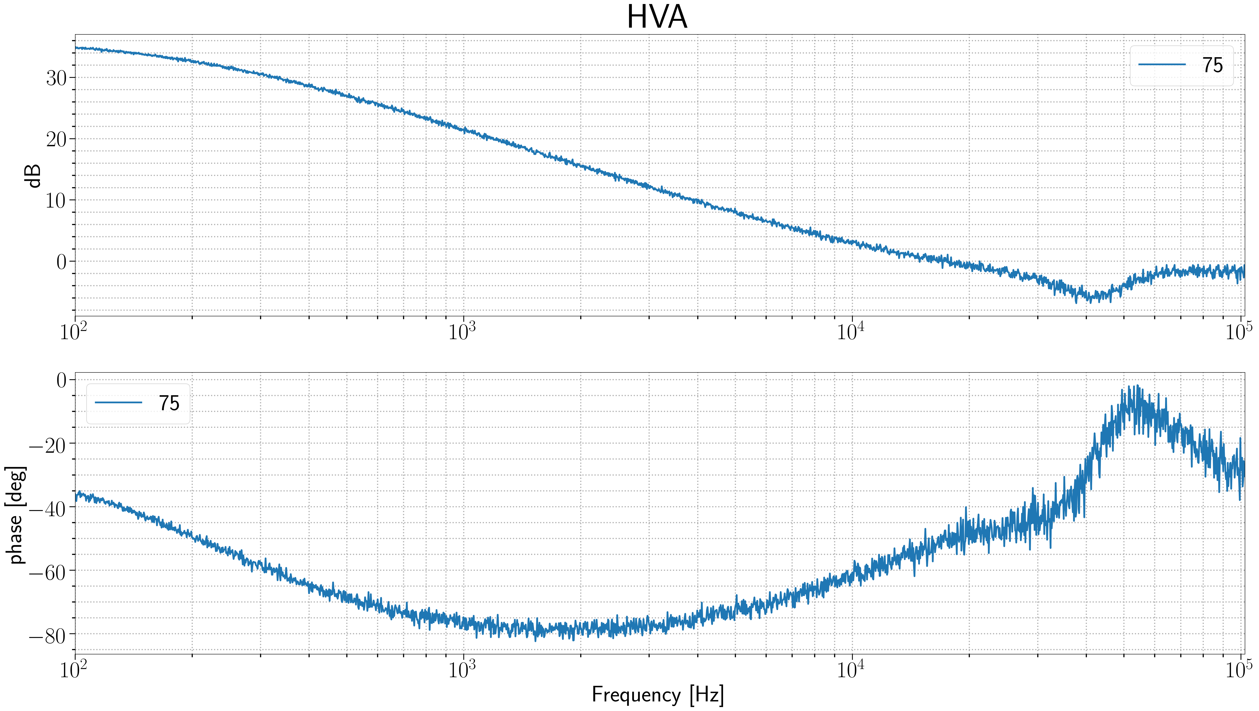
results/frequency_comb/FEB172021freqcomb/HVA.png
