dancvan/AlGaAs_electrooptic_effect/results/frequency_comb/FEB172021freqcomb/OLG.png

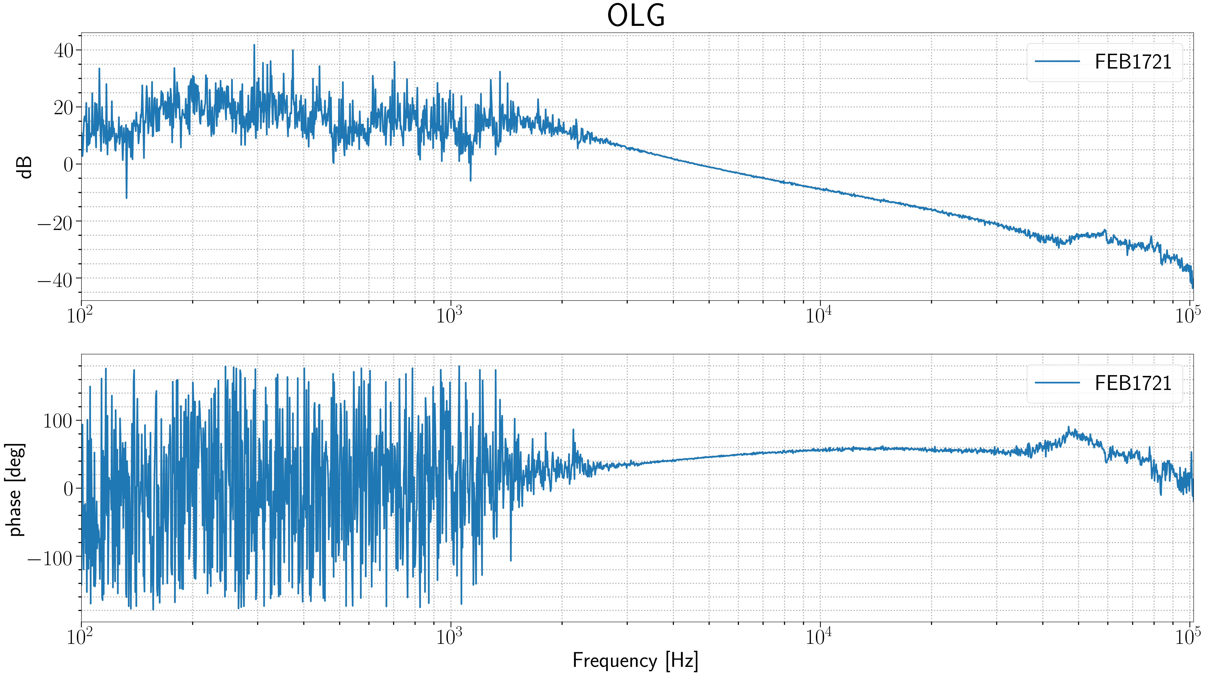
results/frequency_comb/FEB172021freqcomb/OLG.png
