dancvan/AlGaAs_electrooptic_effect/results/frequency_comb/FEB172021noise/FEB172021noise_displacement_normal_electrodes.png

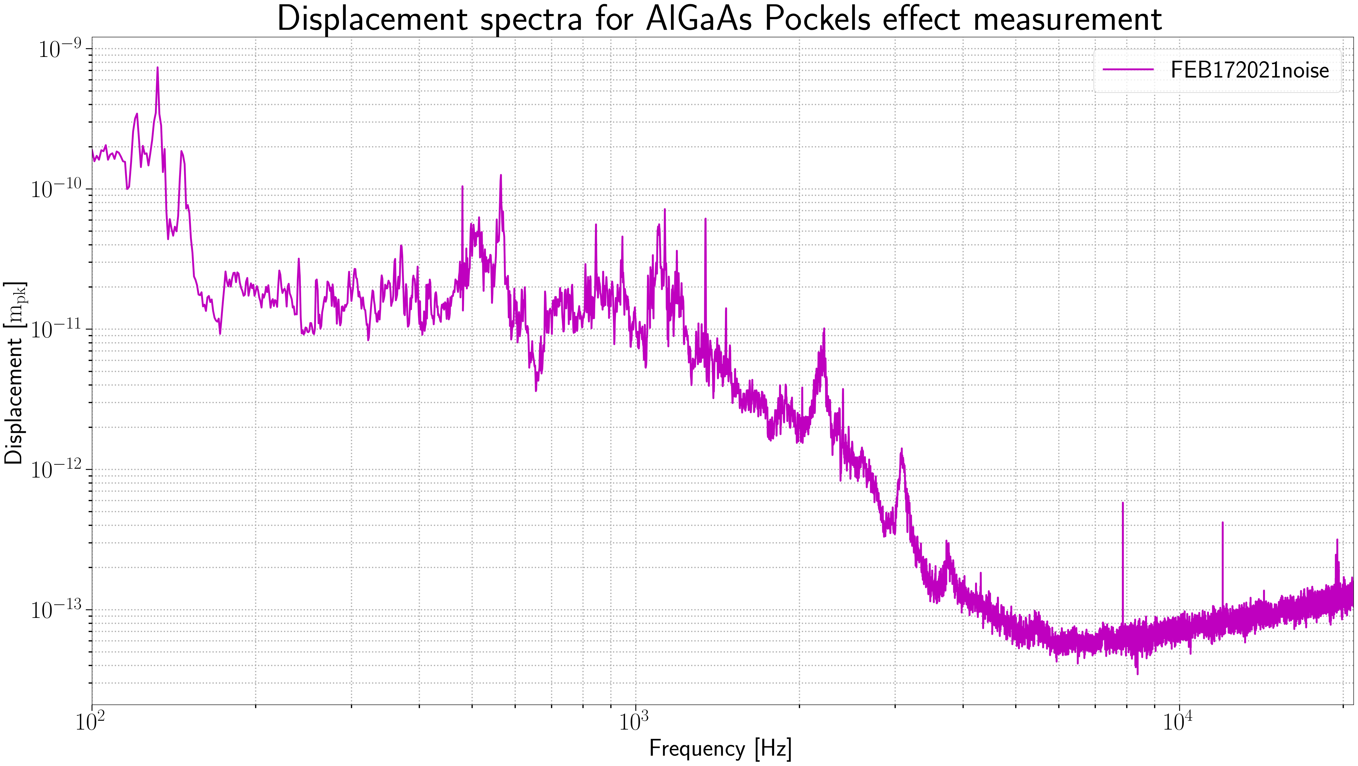
results/frequency_comb/FEB172021noise/FEB172021noise_displacement_normal_electrodes.png
