dancvan/AlGaAs_electrooptic_effect/results/JAMMT/10_24_2019_in_air_2.png

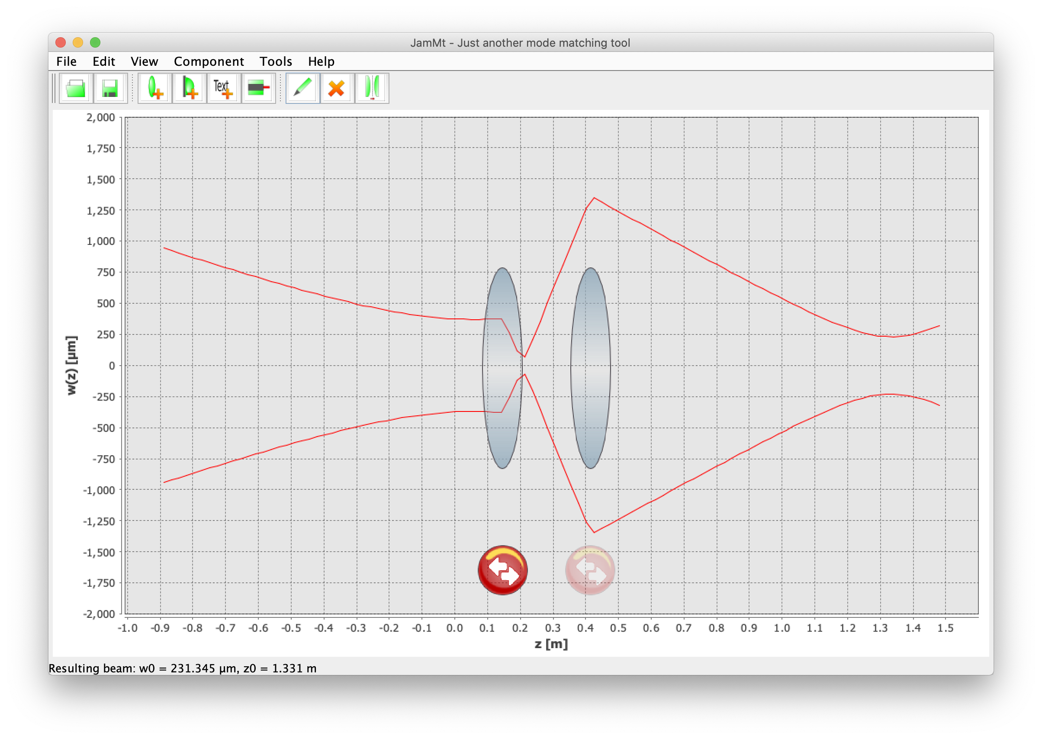
results/JAMMT/10_24_2019_in_air_2.png
