dancvan/AlGaAs_electrooptic_effect/results/JAMMT/power_overlap_single_asymmetric_beam.png

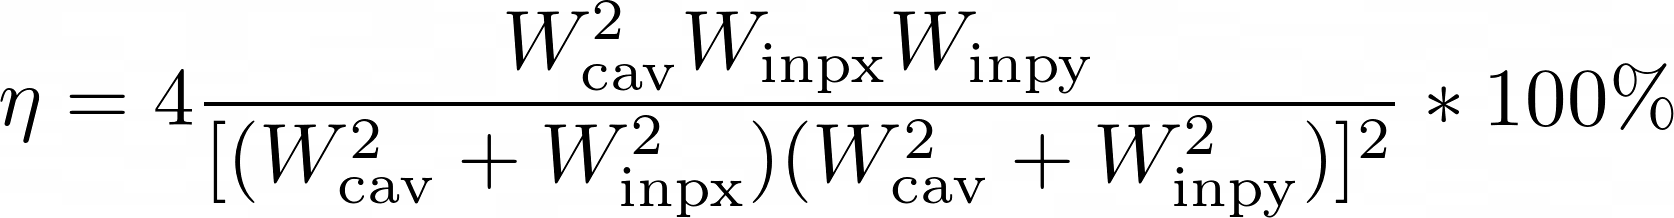
results/JAMMT/power_overlap_single_asymmetric_beam.png
