dancvan/AlGaAs_electrooptic_effect/results/JAMMT/Screen Shot 2020-12-16 at 4.39.46 AM.png

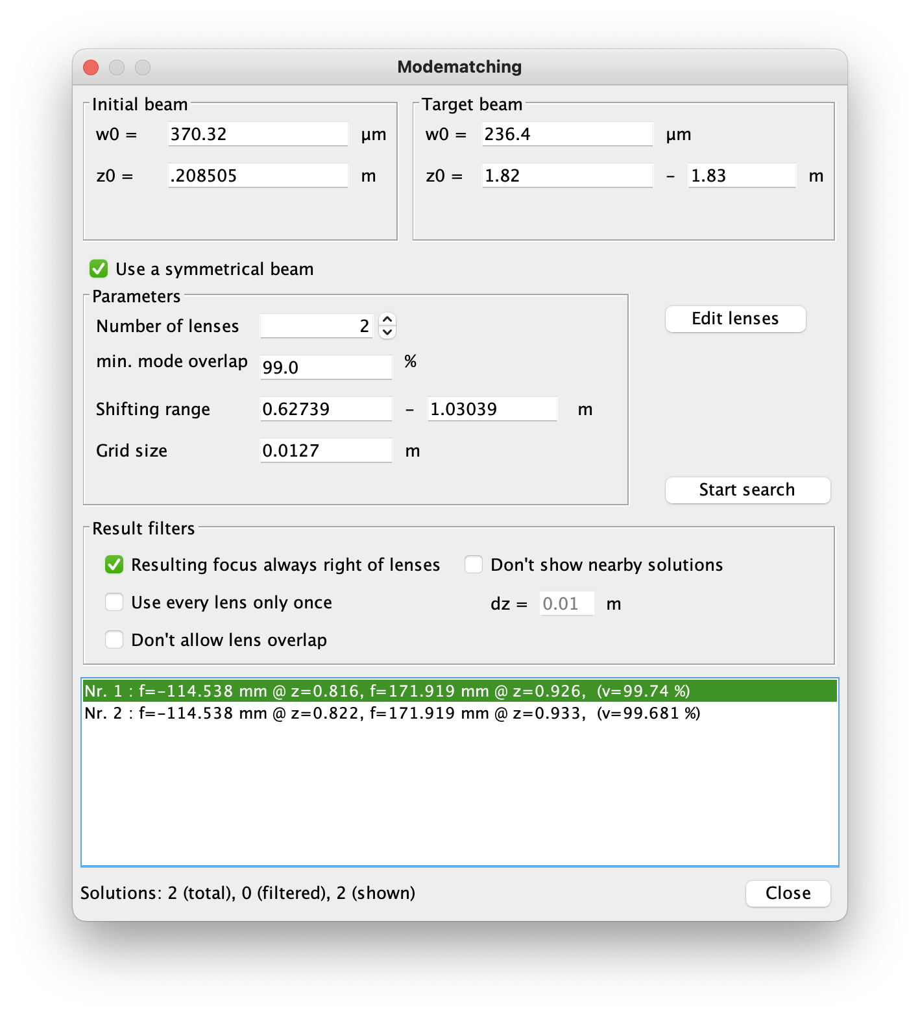
results/JAMMT/Screen Shot 2020-12-16 at 4.39.46 AM.png
