dancvan/AlGaAs_electrooptic_effect/results/noise/03_07_2021_frequency_comb_pk/OLG.png

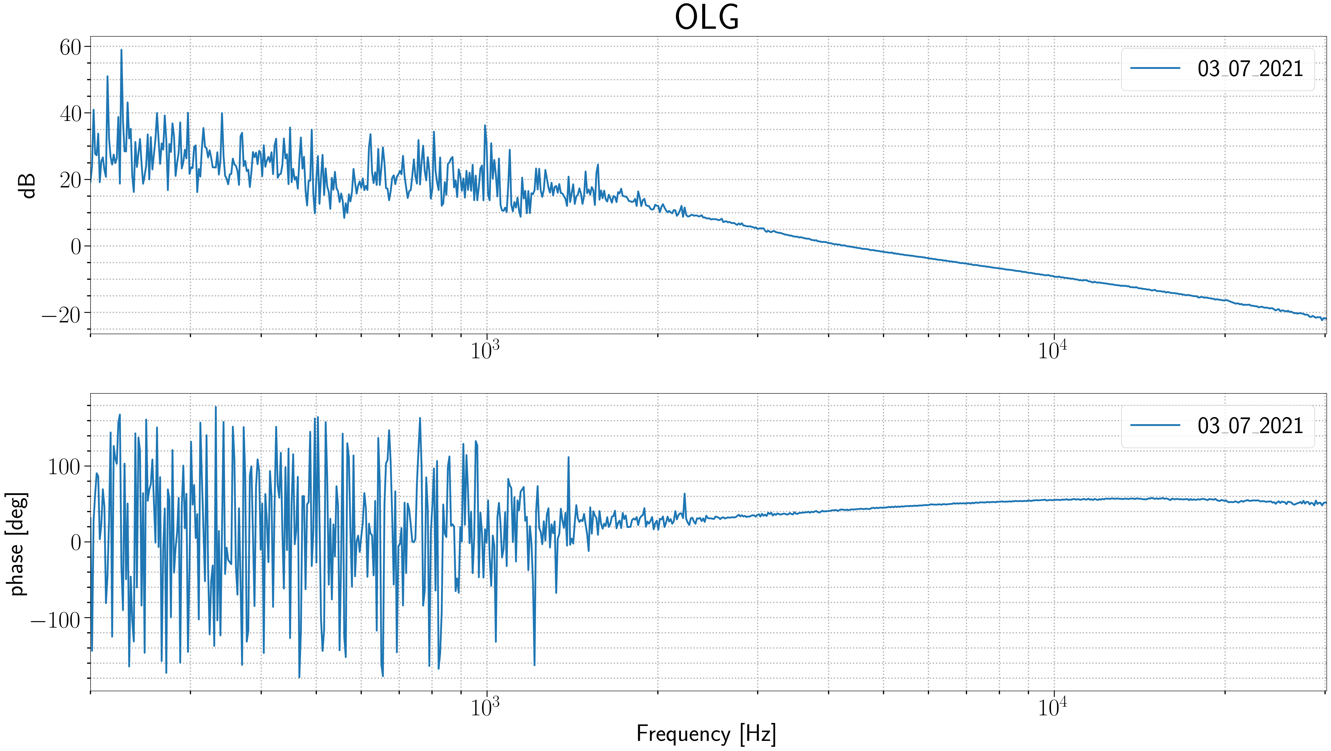
results/noise/03_07_2021_frequency_comb_pk/OLG.png
