dancvan/AlGaAs_electrooptic_effect/results/simulations/electrodes/disk/14-Mar-2021/14-Mar-2021_e_field_inside_outside_normal.png

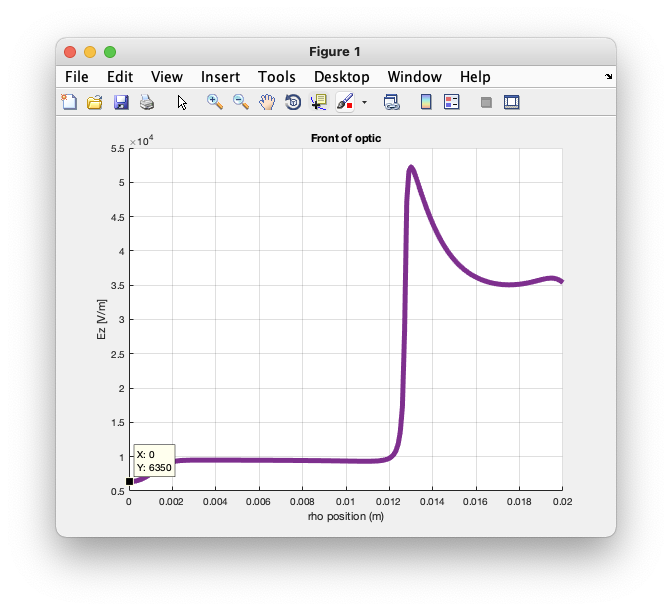
results/simulations/electrodes/disk/14-Mar-2021/14-Mar-2021_e_field_inside_outside_normal.png
