dancvan/AlGaAs_electrooptic_effect/results/swept_frequency/02_22_2021_swept_pk/Frequency_response_of_Pockels_effect.png

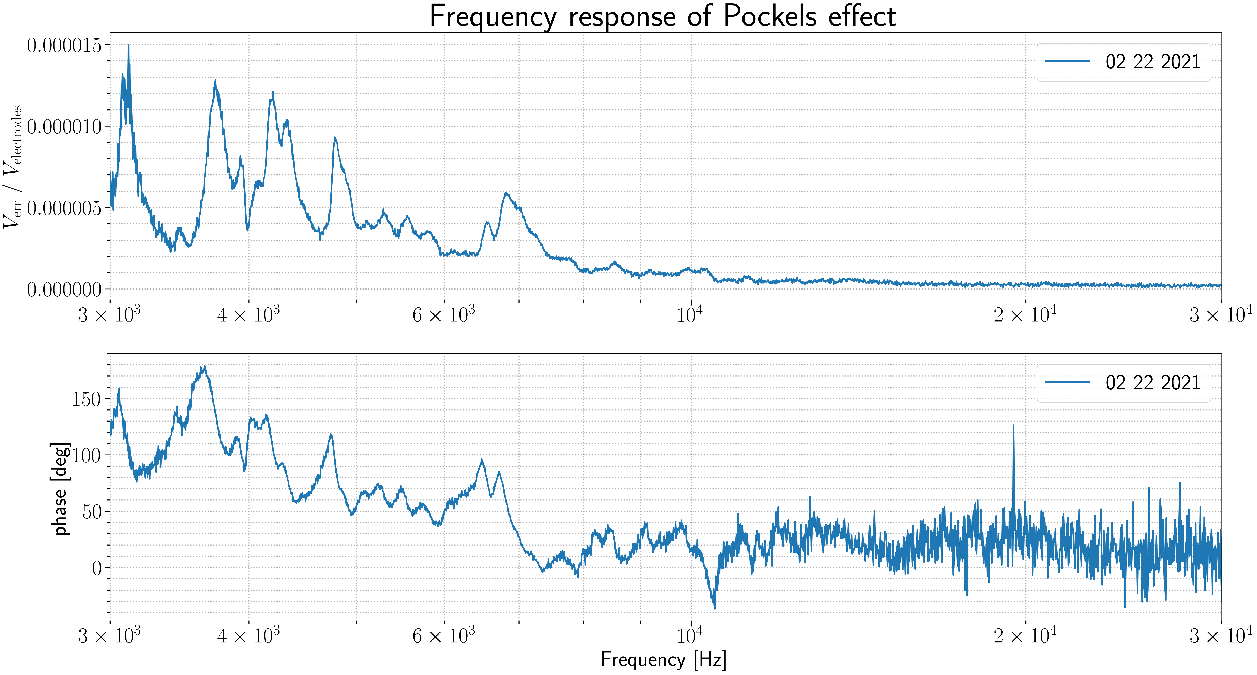
results/swept_frequency/02_22_2021_swept_pk/Frequency_response_of_Pockels_effect.png
