dancvan/AlGaAs_electrooptic_effect/results/swept_frequency/02_22_2021_swept_pk/OLG.png

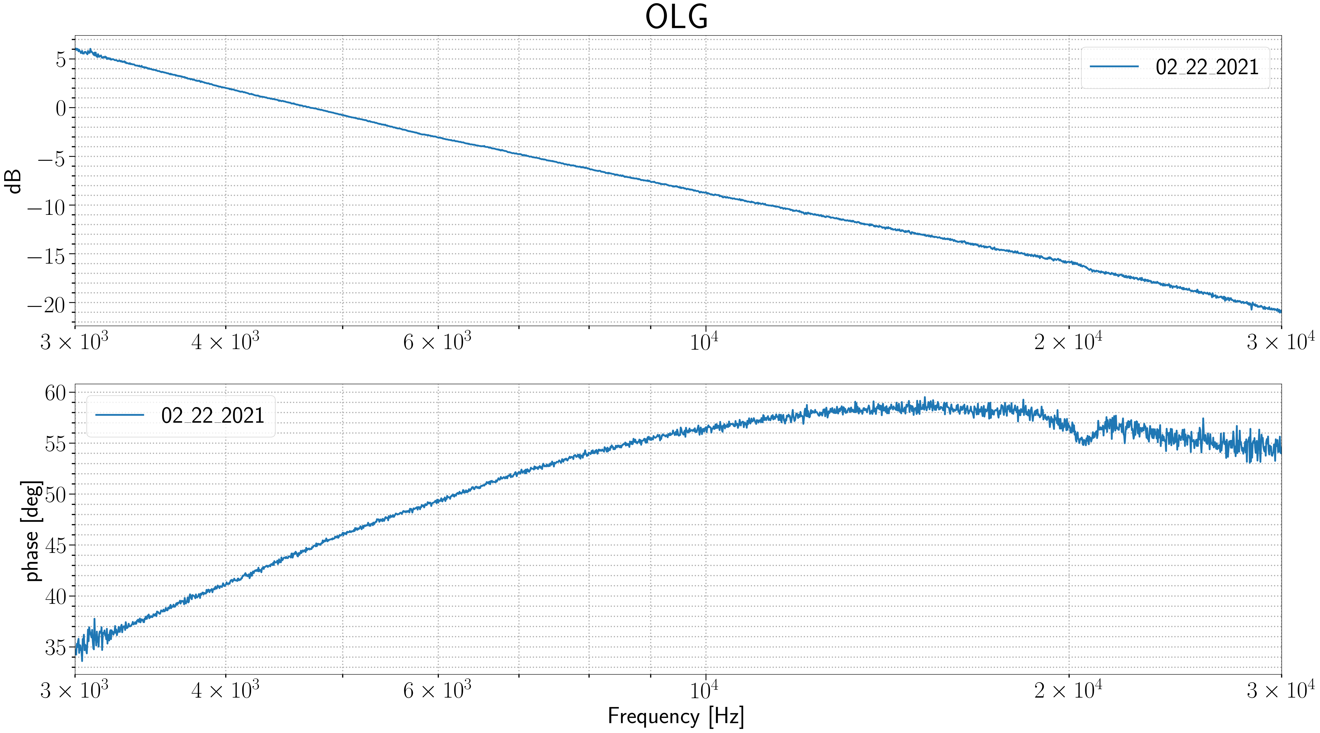
results/swept_frequency/02_22_2021_swept_pk/OLG.png
