dancvan/AlGaAs_electrooptic_effect/results/swept_frequency/02_22_2021_swept_pk/Pockels_effect_frequency_response_vspectra.png

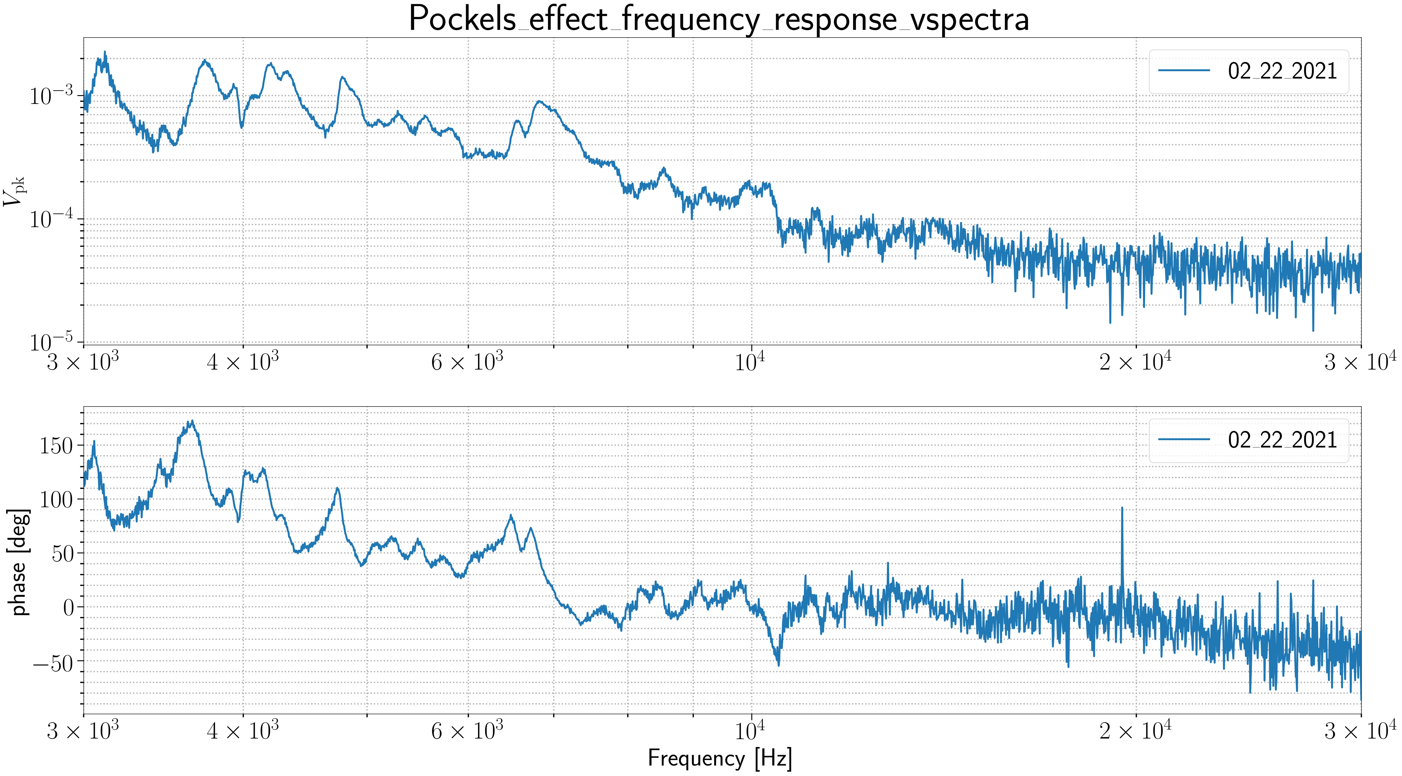
results/swept_frequency/02_22_2021_swept_pk/Pockels_effect_frequency_response_vspectra.png
