dancvan/AlGaAs_electrooptic_effect/results/swept_frequency/02_22_2021_swept_pk/Potential difference across electrodes.png

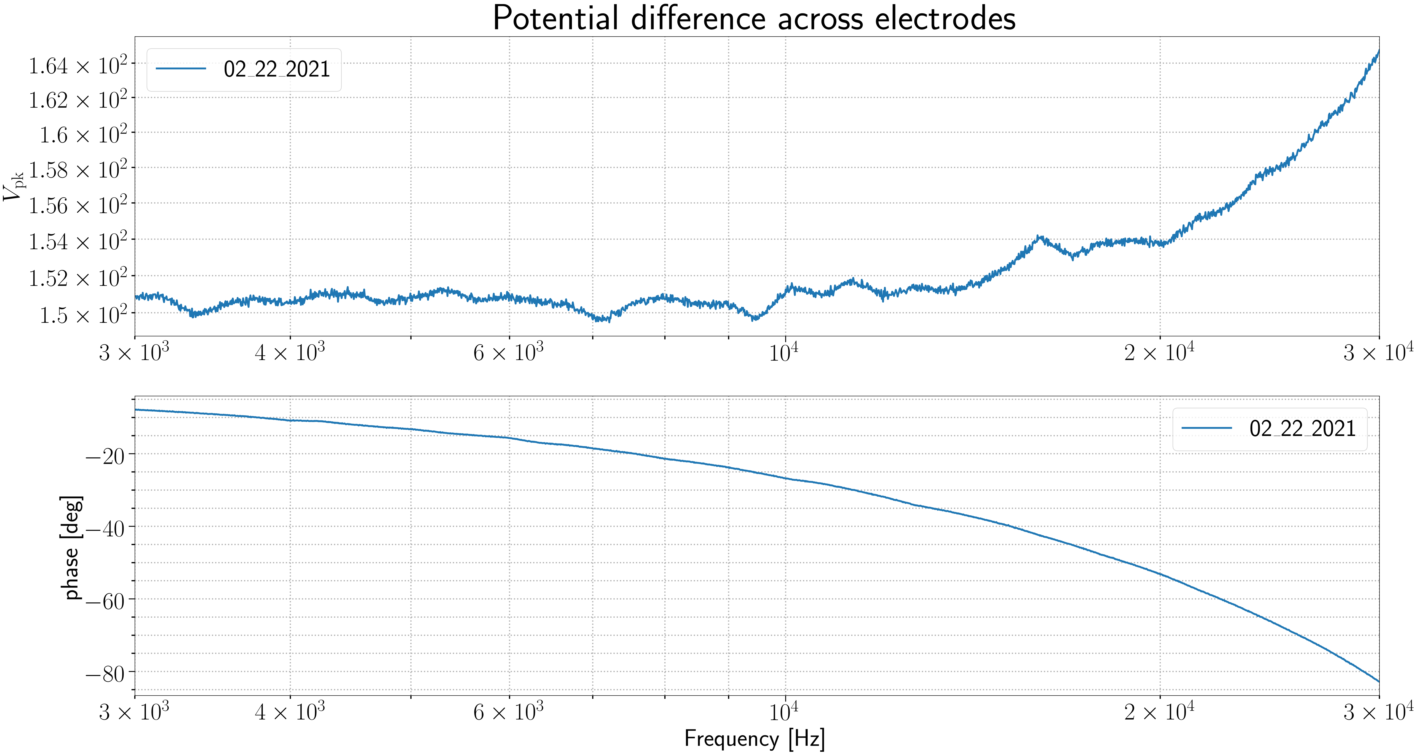
results/swept_frequency/02_22_2021_swept_pk/Potential difference across electrodes.png
