dancvan/AlGaAs_electrooptic_effect/results/swept_frequency/03_23_2021_swept_pk_sio2ta2o5/Displacement spectra for AlGaAs Pockels effect measurement.png

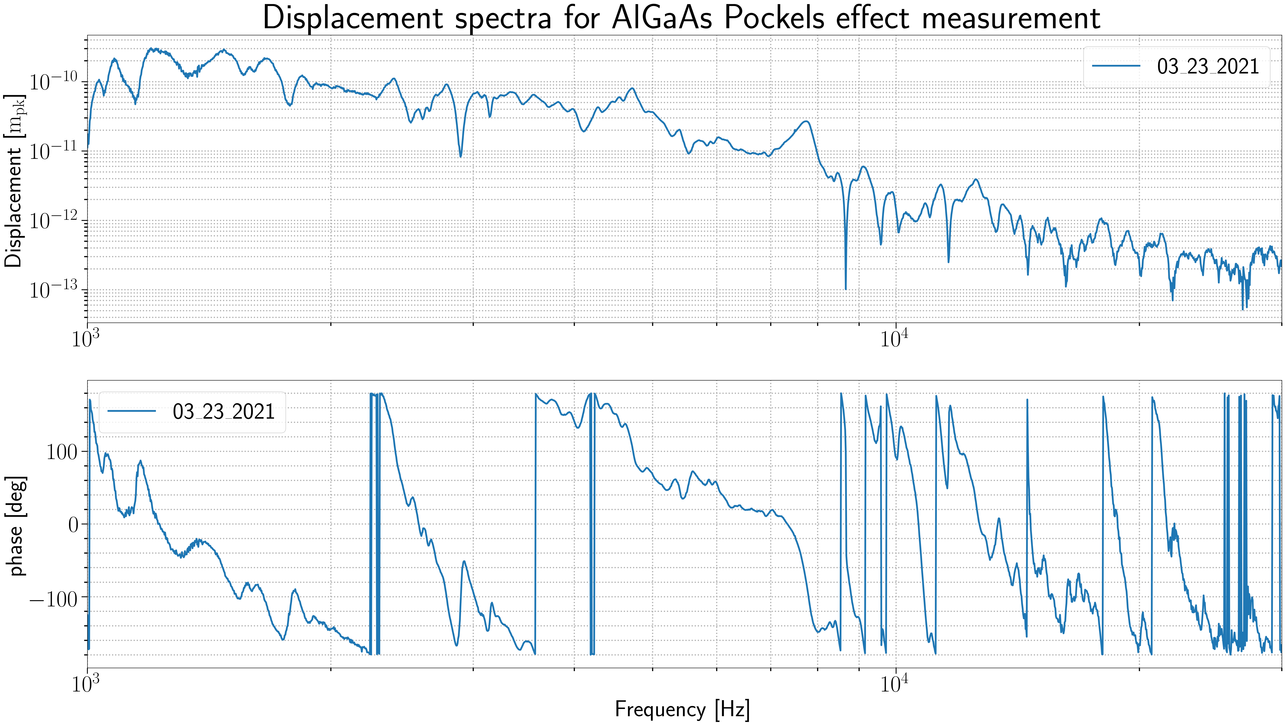
results/swept_frequency/03_23_2021_swept_pk_sio2ta2o5/Displacement spectra for AlGaAs Pockels effect measurement.png
