dancvan/AlGaAs_electrooptic_effect/results/updates/10_27_2020/laser_pzt_sweep/part_FSR.png

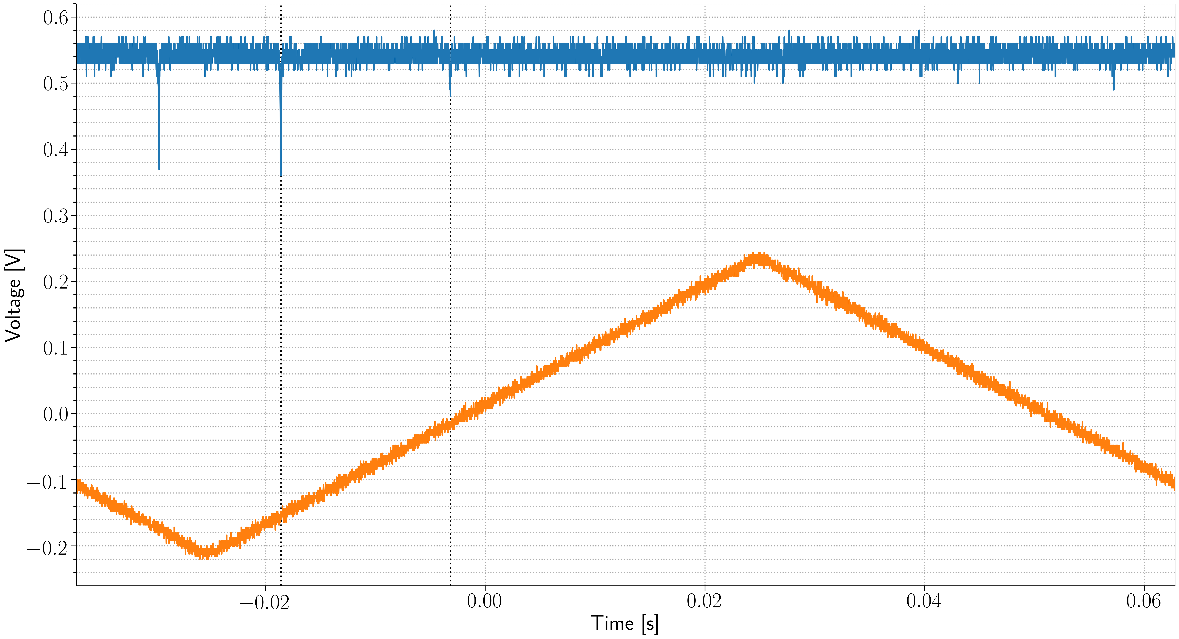
results/updates/10_27_2020/laser_pzt_sweep/part_FSR.png
