dancvan/AlGaAs_electrooptic_effect/results/updates/12_01_2020/Screen Shot 2020-11-18 at 10.35.21 AM.png

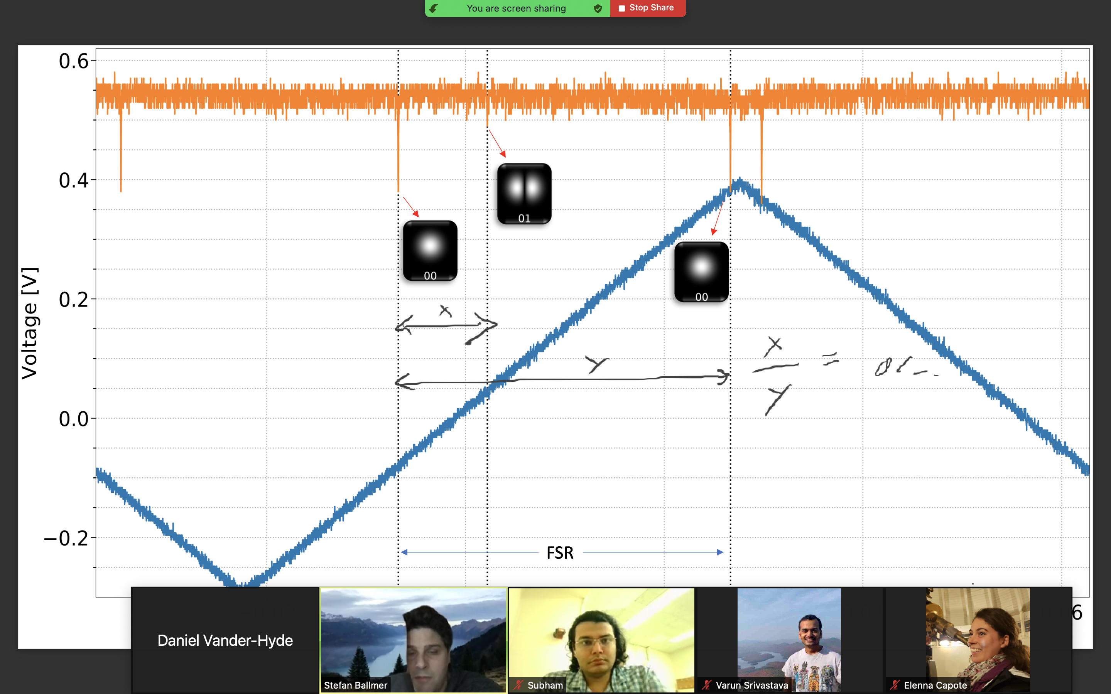
results/updates/12_01_2020/Screen Shot 2020-11-18 at 10.35.21 AM.png
