dancvan/AlGaAs_electrooptic_effect/results/updates/12_08_2020/IMG_0278.jpeg

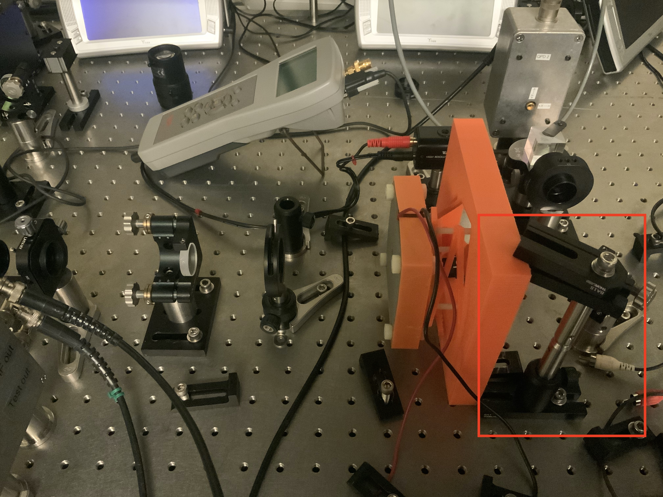
results/updates/12_08_2020/IMG_0278.jpeg
