dancvan/AlGaAs_electrooptic_effect/results/updates/ellip_model_v_measured.png

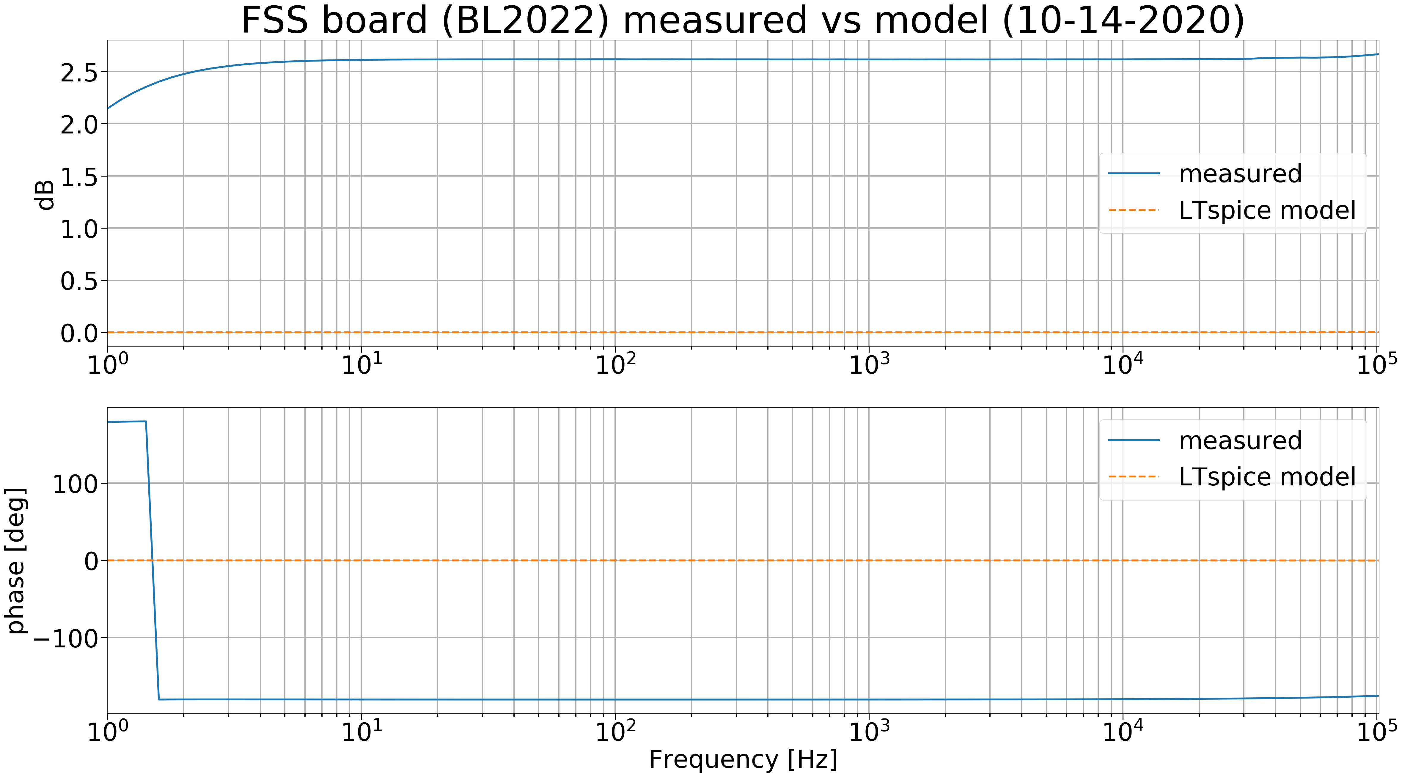
results/updates/ellip_model_v_measured.png
