dancvan/AlGaAs_electrooptic_effect/results/updates/fss_measure_v_model.png

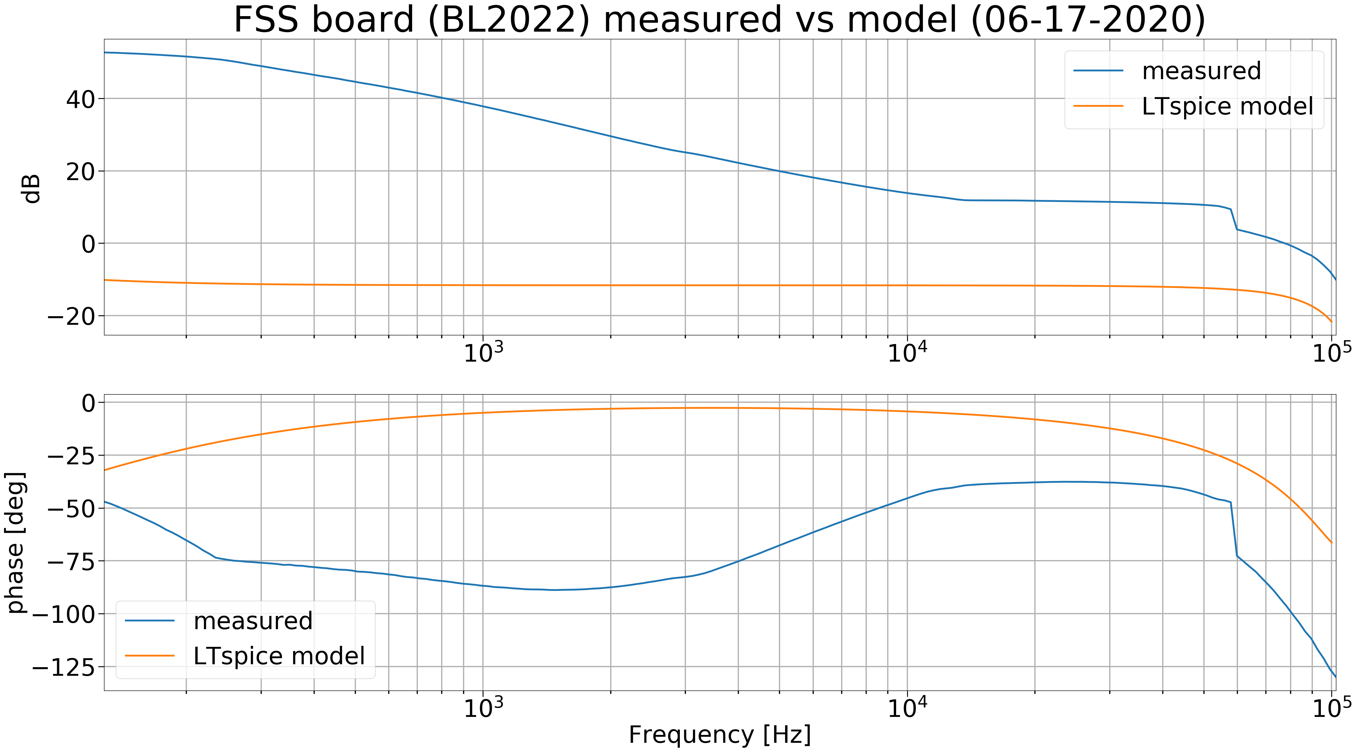
results/updates/fss_measure_v_model.png
