dancvan/AlGaAs_electrooptic_effect/results/updates/tp02_model_v_measured.png

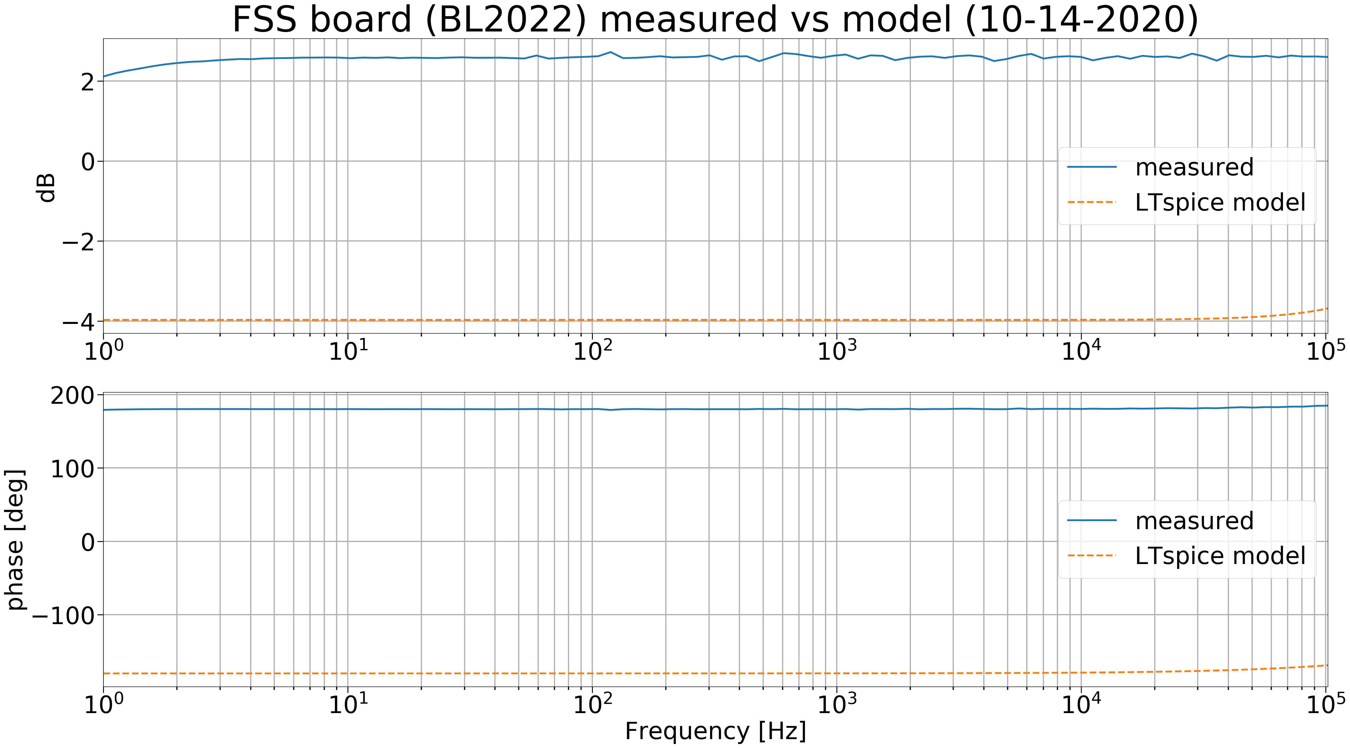
results/updates/tp02_model_v_measured.png
