dancvan/AlGaAs_electrooptic_effect/results/updates/tp11_model_v_measured.png

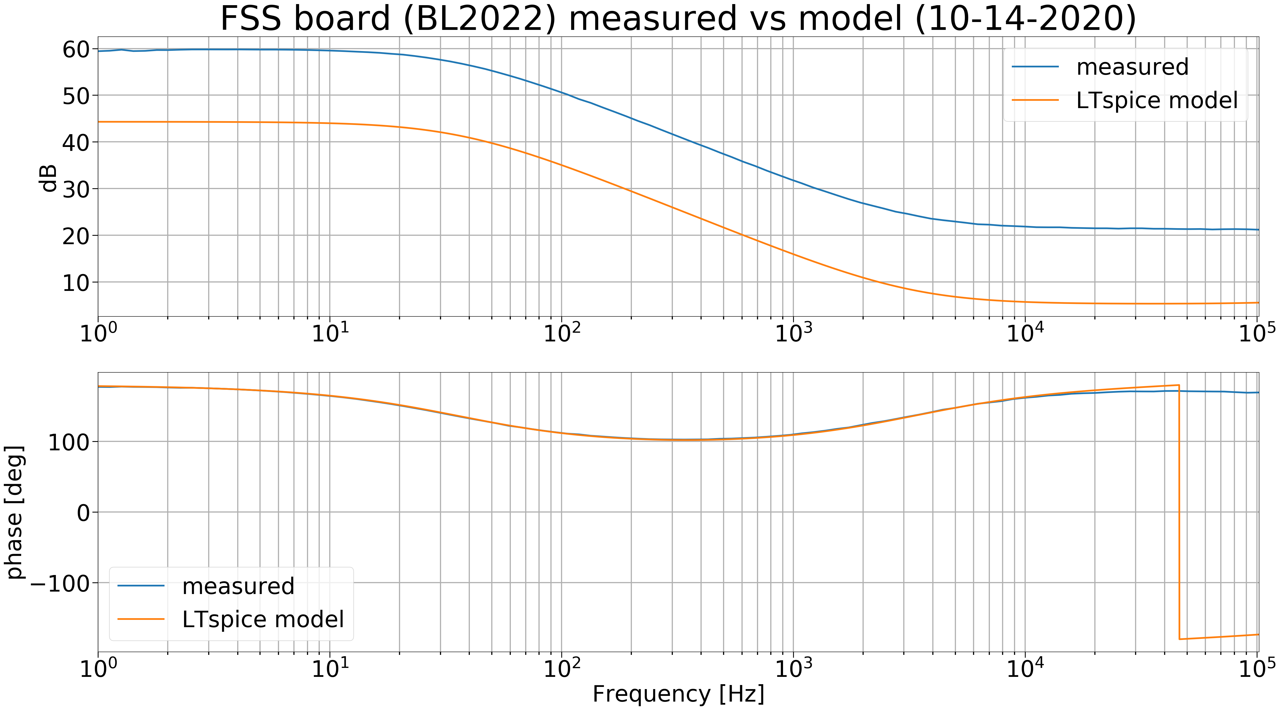
results/updates/tp11_model_v_measured.png
