dancvan/AlGaAs_electrooptic_effect/results/updates/tp12_model_v_measured.png

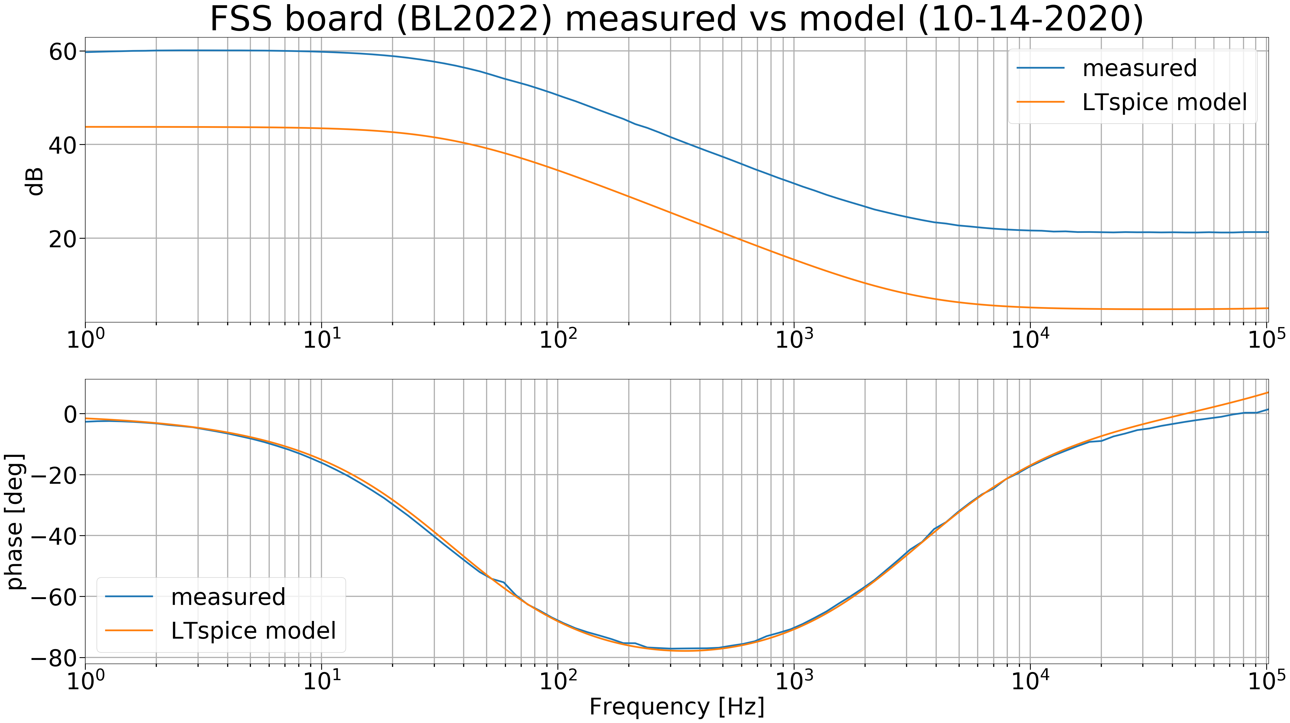
results/updates/tp12_model_v_measured.png
