dancvan/AlGaAs_electrooptic_effect/measurements/gain_and_probe_box/model.asc

R1: res; 10k
R2: res; 60k
R3: res; 100000
R4: res; 10
U1: OP27G
V1: voltage; 12
V2: voltage; 12
V3: voltage; ""; AC 1
Named nets: 0, V+, V-
.ac dec 100 1 20MEG
