dancvan/AlGaAs_electrooptic_effect/measurements/FSS_tfs/spice/10_14_2020/model.asc

C1: cap; 200p
C2: cap; 47p
C3: cap; 200p
C4: cap; 1n
C5: cap; 10n
C6: cap; 470p
C7: cap; 120p
L1: ind; 1.2µ
L2: ind; 3.3m
R1: res; 200
R2: res; 316
R3: res; 100
R4: res; 10k
R5: res; 10k
R6: res; 4.99k
R7: res; 430k
R8: res; 4870
R9: res; 3.16k
R10: res; 3k
R11: res; 7500
R12: res; 3.74k
R13: res; 3.74k
R14: res; 50
U1: AD829J
U2: AD602
U3: AD602
U4: OP27G
U5: AD847J
U6: AD847J
V1: voltage; ""; AC 1
V2: voltage; 15
V3: voltage; 15
V4: voltage; 0
V5: voltage; 0
V6: voltage; 5
V7: voltage; 5
Named nets: Vout, 0, V+, V-, Vlow+, Vlow-, Total_gain, Laser_Gain, Total_Gain
.ac dec 1k 1 103k
